ksr/YACC1-2020/PCB/Working - Under Develolpment/Index Registers 1.2/Notes.rtf

Index registers V1.0

Next version 1.1

Changes since 1.0

Signal -IN and -OUT converted to In and OUT. Neither used in Index Register board

BUS Description PDF dated June 18 2020 is updated to new spec

NOTE from old design

Up or Down on rising edge other line must be high

IC38 switched to 4077 pin compatible with 74266

Version 1.1 to production

Next version 1.2
SEE page 7
Is bus direction correct, should it be based on -rd-sel
