ksr/YACC1-2020/PCB/Production/ALU-V3.0-2 layer/Notes.rtf

SCRAP. ARGh no vcc and gnd

Board labeled YACC1 ALYU BOARD V1.0

ALU V3.0

Sent to Production using files in “gerbers” directory. This was missing outline file, should have used alu4_2020-06-14.zip in this directory this had outline file.

This is a 2 layer board, should have been a 4 layer board

Signal -IN and -OUT converted to In and OUT. Only IN is used in ALU

No changes made to production files but BUS is now treated as active HI for IN and OUT. TBC Schematic/PCB shows active low but will be assumed input from bus is active HI

BUS Description PDF dated June 18 2020 is updated to new spec

Mask shows V1.0, should read 3.0
