ksr/YACC1-2020/PCB/Production/Bus Jumper Horizontal V3.2/Notes.rtf

Changes since production Horizontal Bus Jumper 3.0

3.2
Increase trace width spacing and add layers

Next version V3.3
