ksr/YACC1-2020/PCB/Production/Index Registers - no address1.0/Notes.rtf

Index registers V3.0

Signal -IN and -OUT converted to In and OUT. Neither used in Index Register board

BUS Description PDF dated June 18 2020 is updated to new spec

IC38 switched to 4077 pin compatible with 74266
