ksr/YACC1-2020/PCB/Production/Mem Switch V1.0/Notes.rtf

Changes since production to V3.1

Added -Valid Memory Address (-VMA) to bus Row C pin 12)

Next version V3.2
