ksr/YACC1-2020/Photos & Videos/alu v3.2 top.jpeg

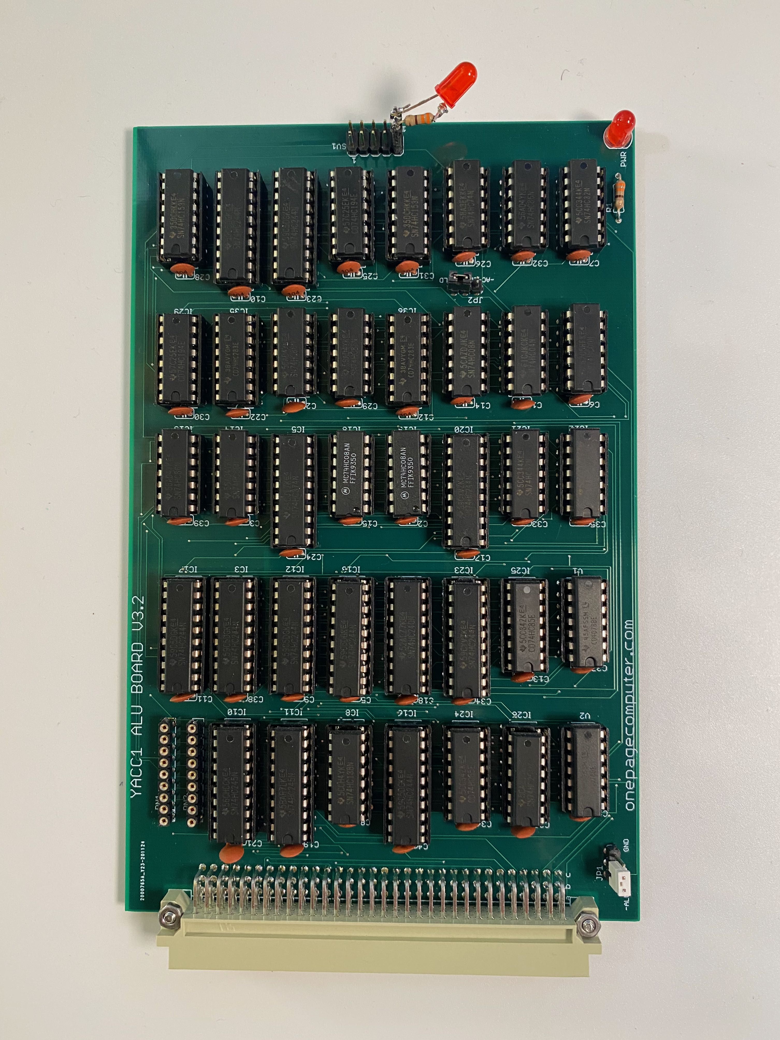
Photos & Videos/alu v3.2 top.jpeg
