ksr/YACC1-2020/Photos & Videos/bus v1.0 top.jpeg

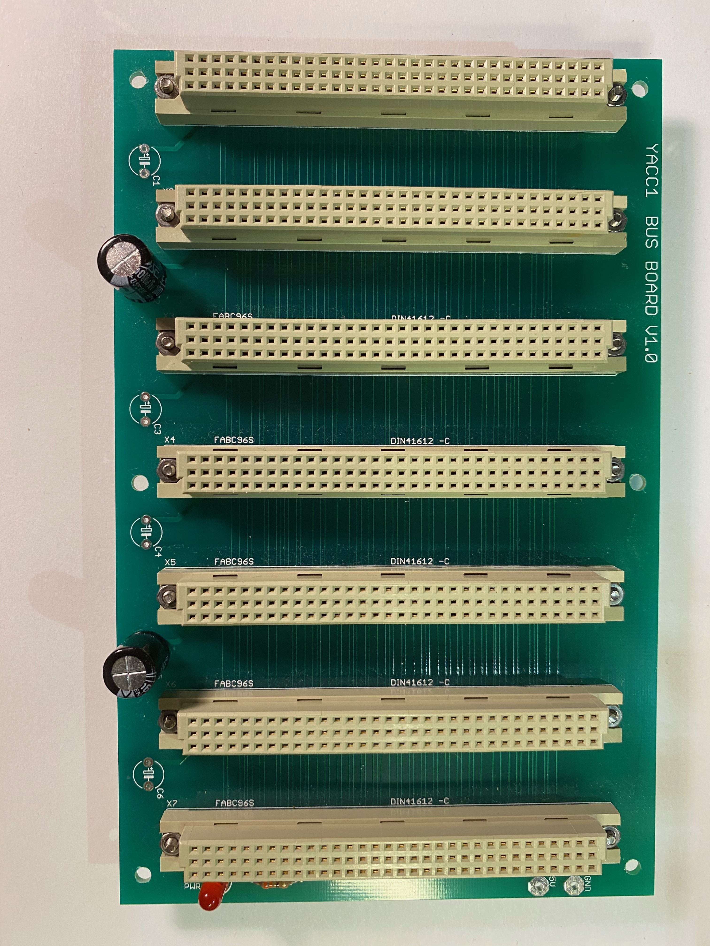
Photos & Videos/bus v1.0 top.jpeg
