ksr/YACC1-2020/Photos & Videos/index register v1.1 top.jpeg

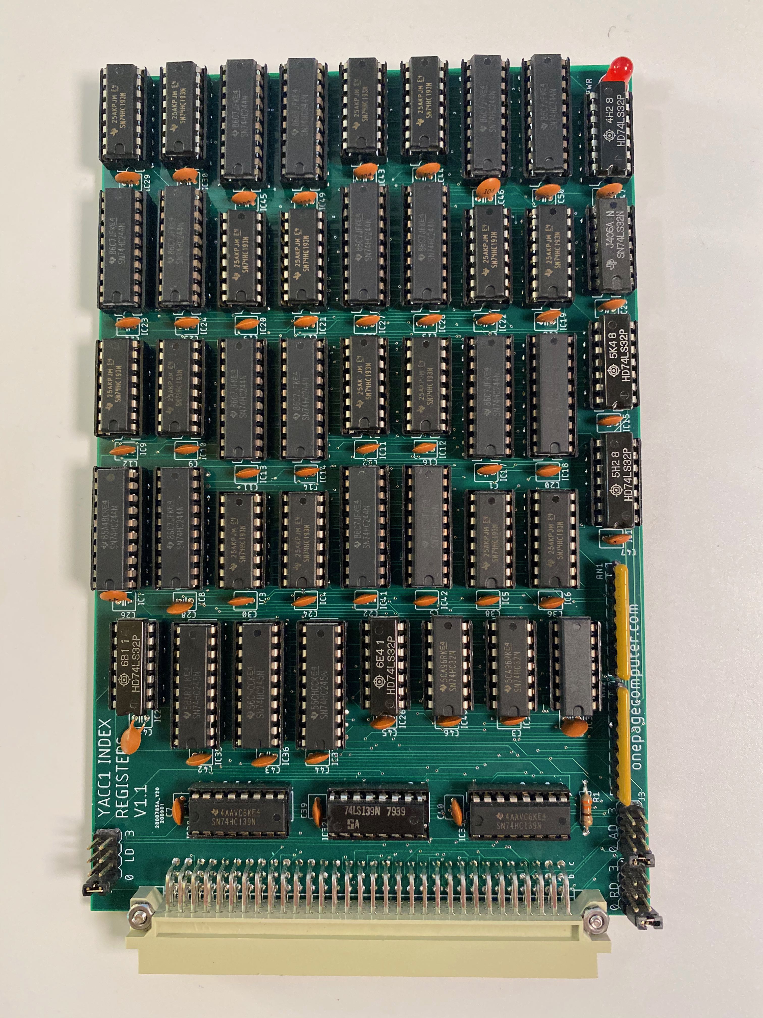
Photos & Videos/index register v1.1 top.jpeg
