ksr/YACC1-2020/Photos & Videos/io v1.1 bottom.jpeg

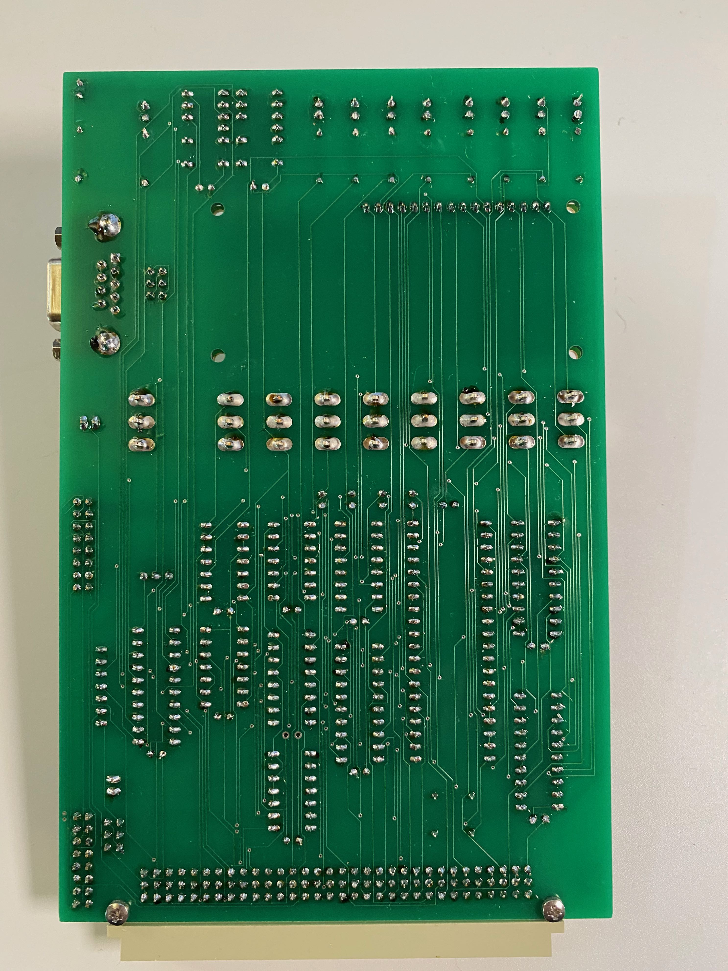
Photos & Videos/io v1.1 bottom.jpeg
