ksr/YACC1-2020/Photos & Videos/sequencer memory v2.1 top.jpeg

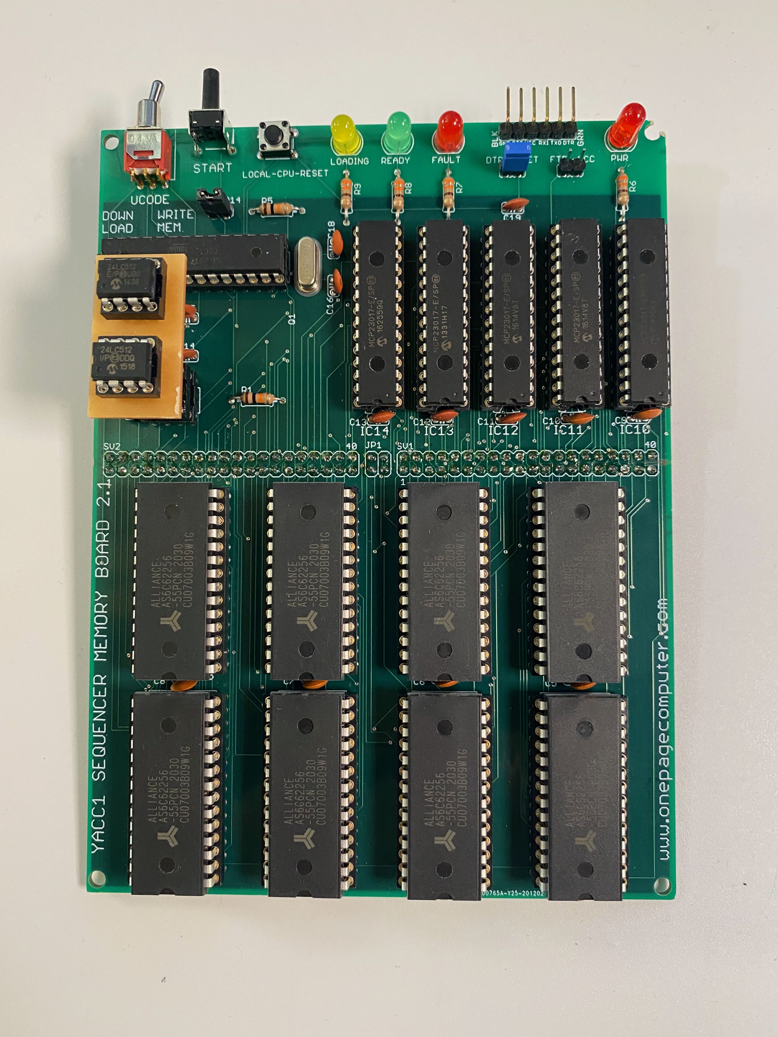
Photos & Videos/sequencer memory v2.1 top.jpeg
