ksr/YACC1-2020/Photos & Videos/sequencer top.jpeg

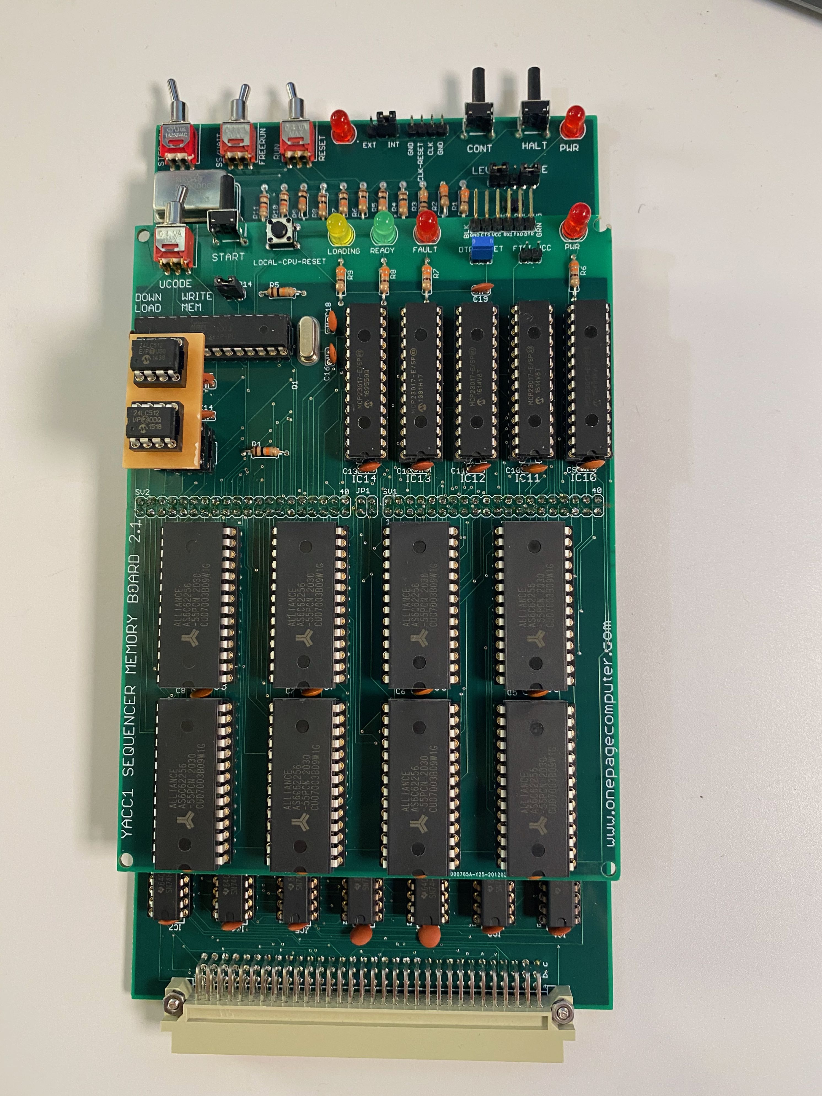
Photos & Videos/sequencer top.jpeg
