ksr/YACC1-2020/Photos & Videos/system1.jpeg

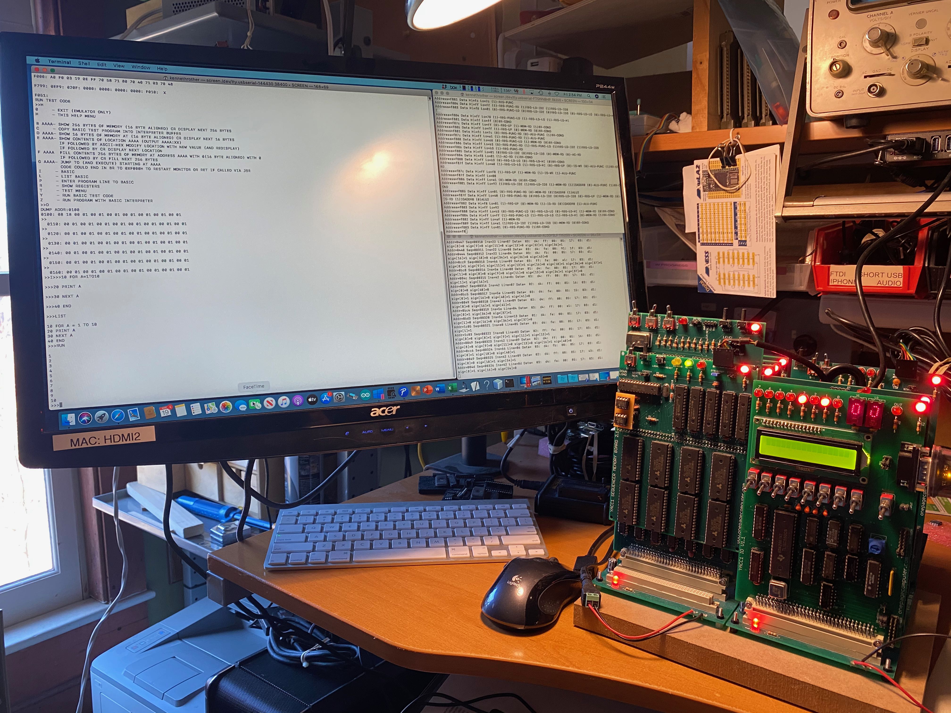
Photos & Videos/system1.jpeg
