ksr/YACC1-2020/Photos & Videos/bus v1.1 solder.jpeg

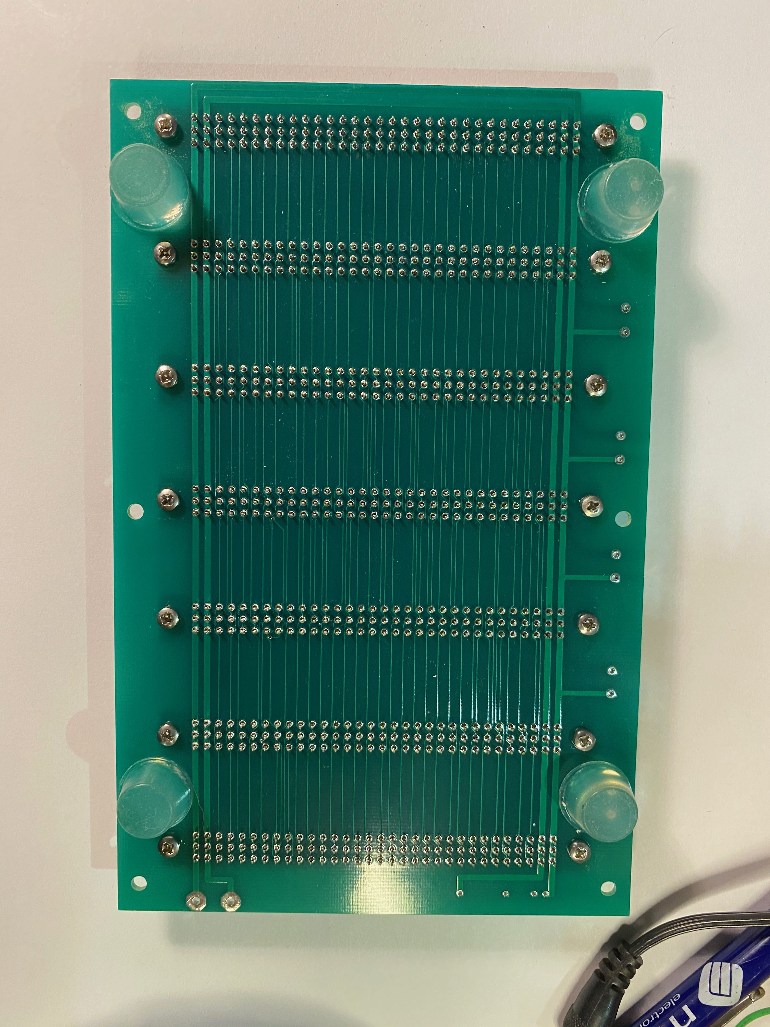
Photos & Videos/bus v1.1 solder.jpeg
