ksr/YACC1-2020/Photos & Videos/index register v1.1 solder.jpeg

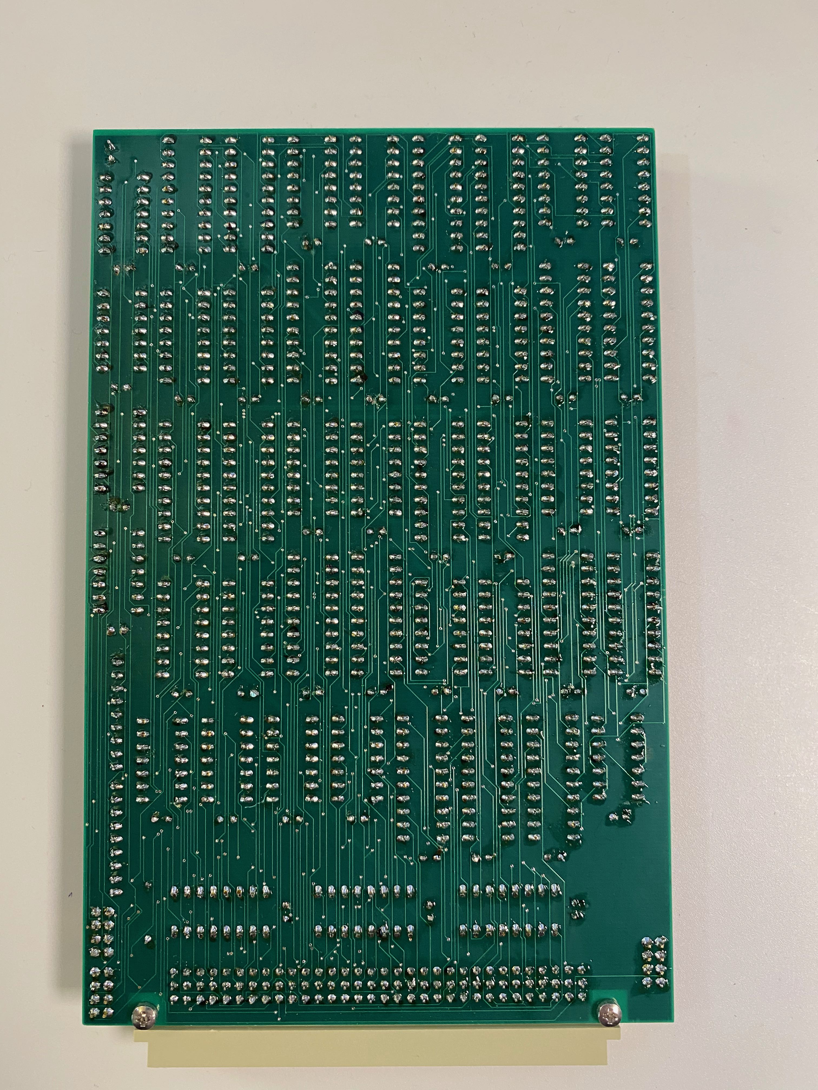
Photos & Videos/index register v1.1 solder.jpeg
