ksr/YACC1-2020/Photos & Videos/sequencer memory v2.1 solder.jpeg

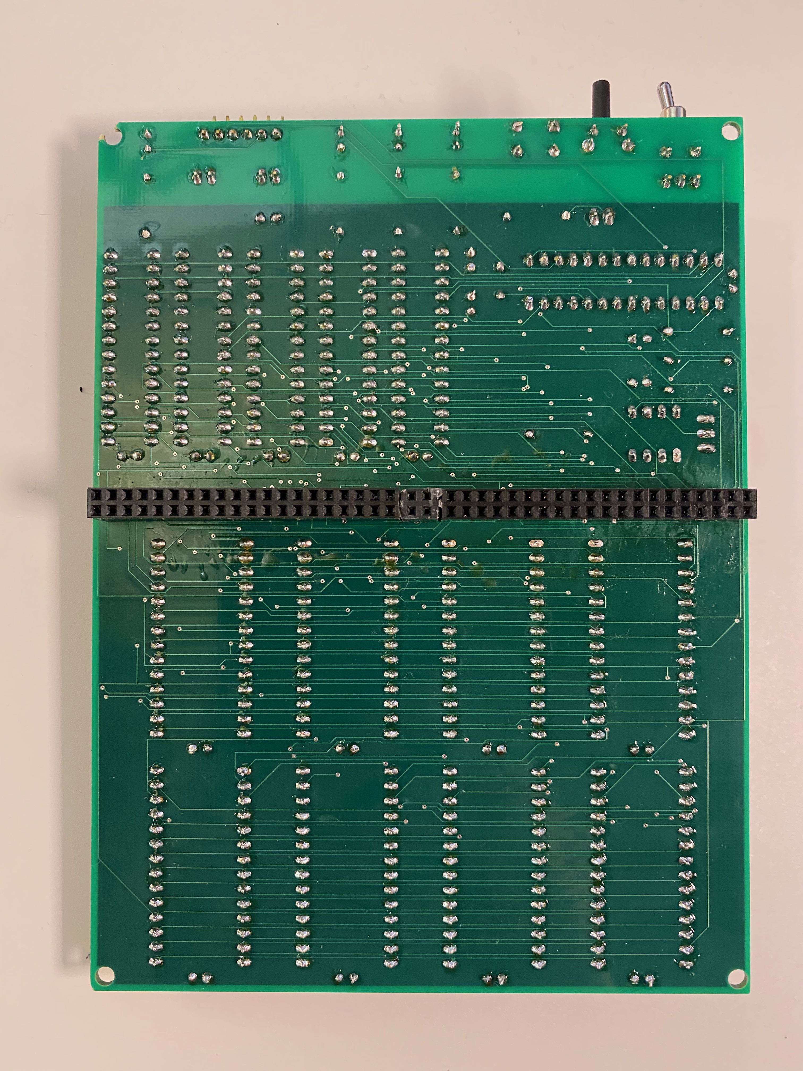
Photos & Videos/sequencer memory v2.1 solder.jpeg
