ksr/YACC1-2020/Photos & Videos/test board v1.1 top.jpeg

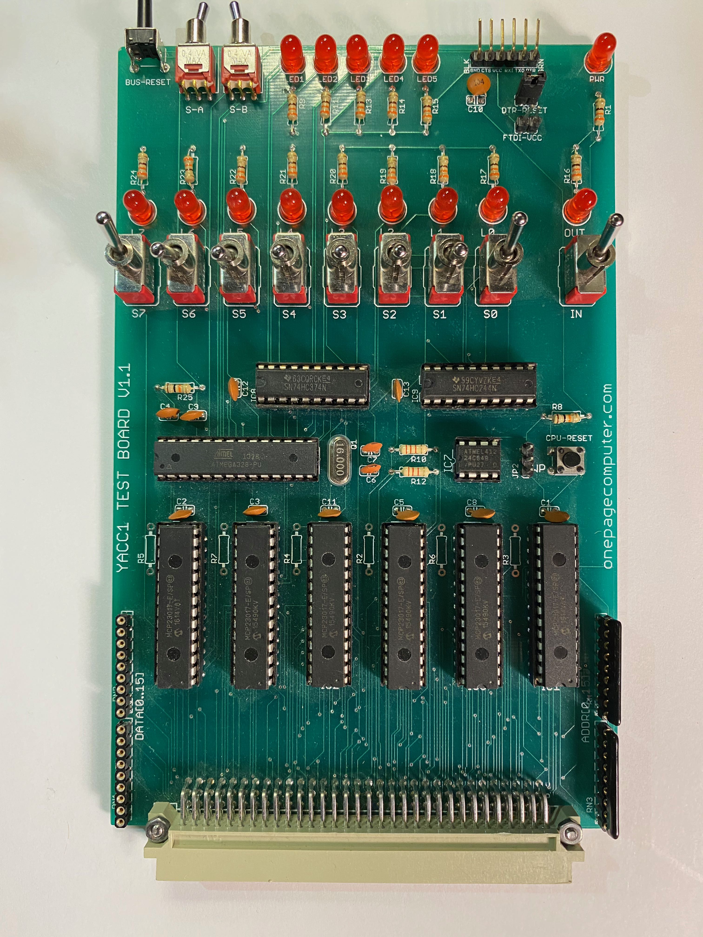
Photos & Videos/test board v1.1 top.jpeg
