ksr/YACC1-2020/PCB/Working - Under Develolpment/Mem Register V1.0/YACC1 Connector - V3.1.pdf

YACC1 Connector | YACC 3.1
Pin | A | A | A | B | B | B | C | C | C

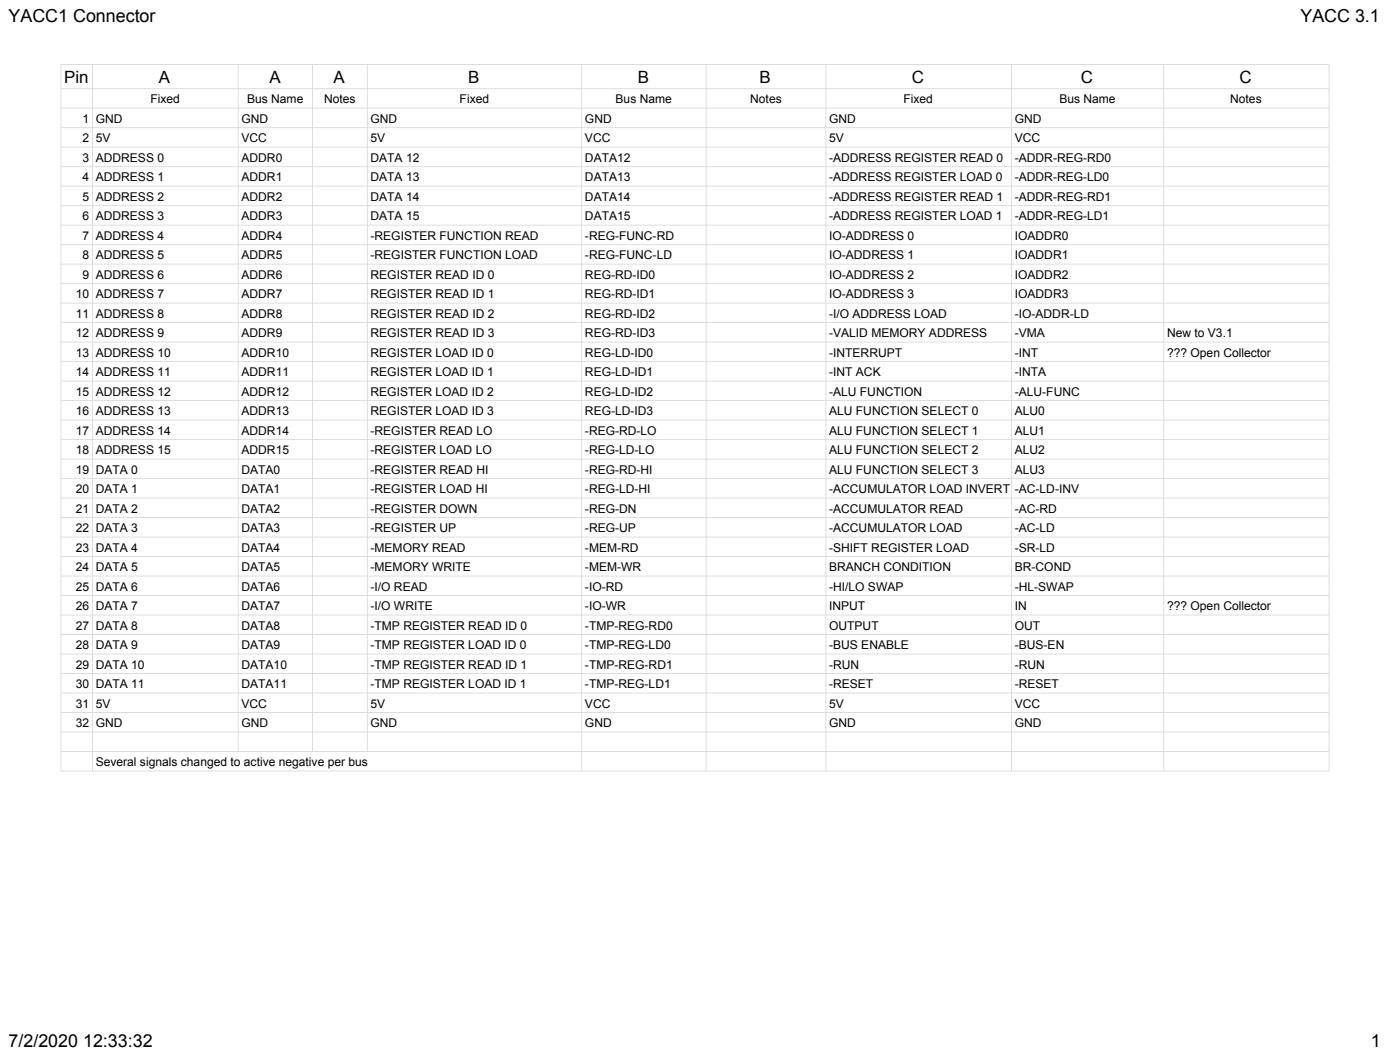
[picture p26: page 1]
Fixed; Bus Name; Notes; 1 GND; GND; VCC; 3 ADDRESS 0; ADDR0; DATA 12; DATA12; -ADDRESS REGISTER READ 0 -ADDR-REG-RD0; 4 ADDRESS 1; ADDR1; DATA 13; DATA13; -ADDRESS REGISTER LOAD 0 -ADDR-REG-LD0; 5 ADDRESS 2; ADDR2; DATA 14; DATA14; -ADDRESS REGISTER READ 1 -ADDR-REG-RD1; 6 ADDRESS 3; ADDR3; DATA 15; DATA15; -ADDRESS REGISTER LOAD 1 -ADDR-REG-LD1; 7 ADDRESS 4; ADDR4; -REGISTER FUNCTION READ; -REG-FUNC-RD; IO-ADDRESS 0; IOADDR0; 8 ADDRESS 5; ADDR5; -REGISTER FUNCTION LOAD; -REG-FUNC-LD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

Several signals changed to active negative per bus
