ksr/YACC1-2020/PCB/Working - Under Develolpment/Memory v1.3/Memory V1.2.pdf

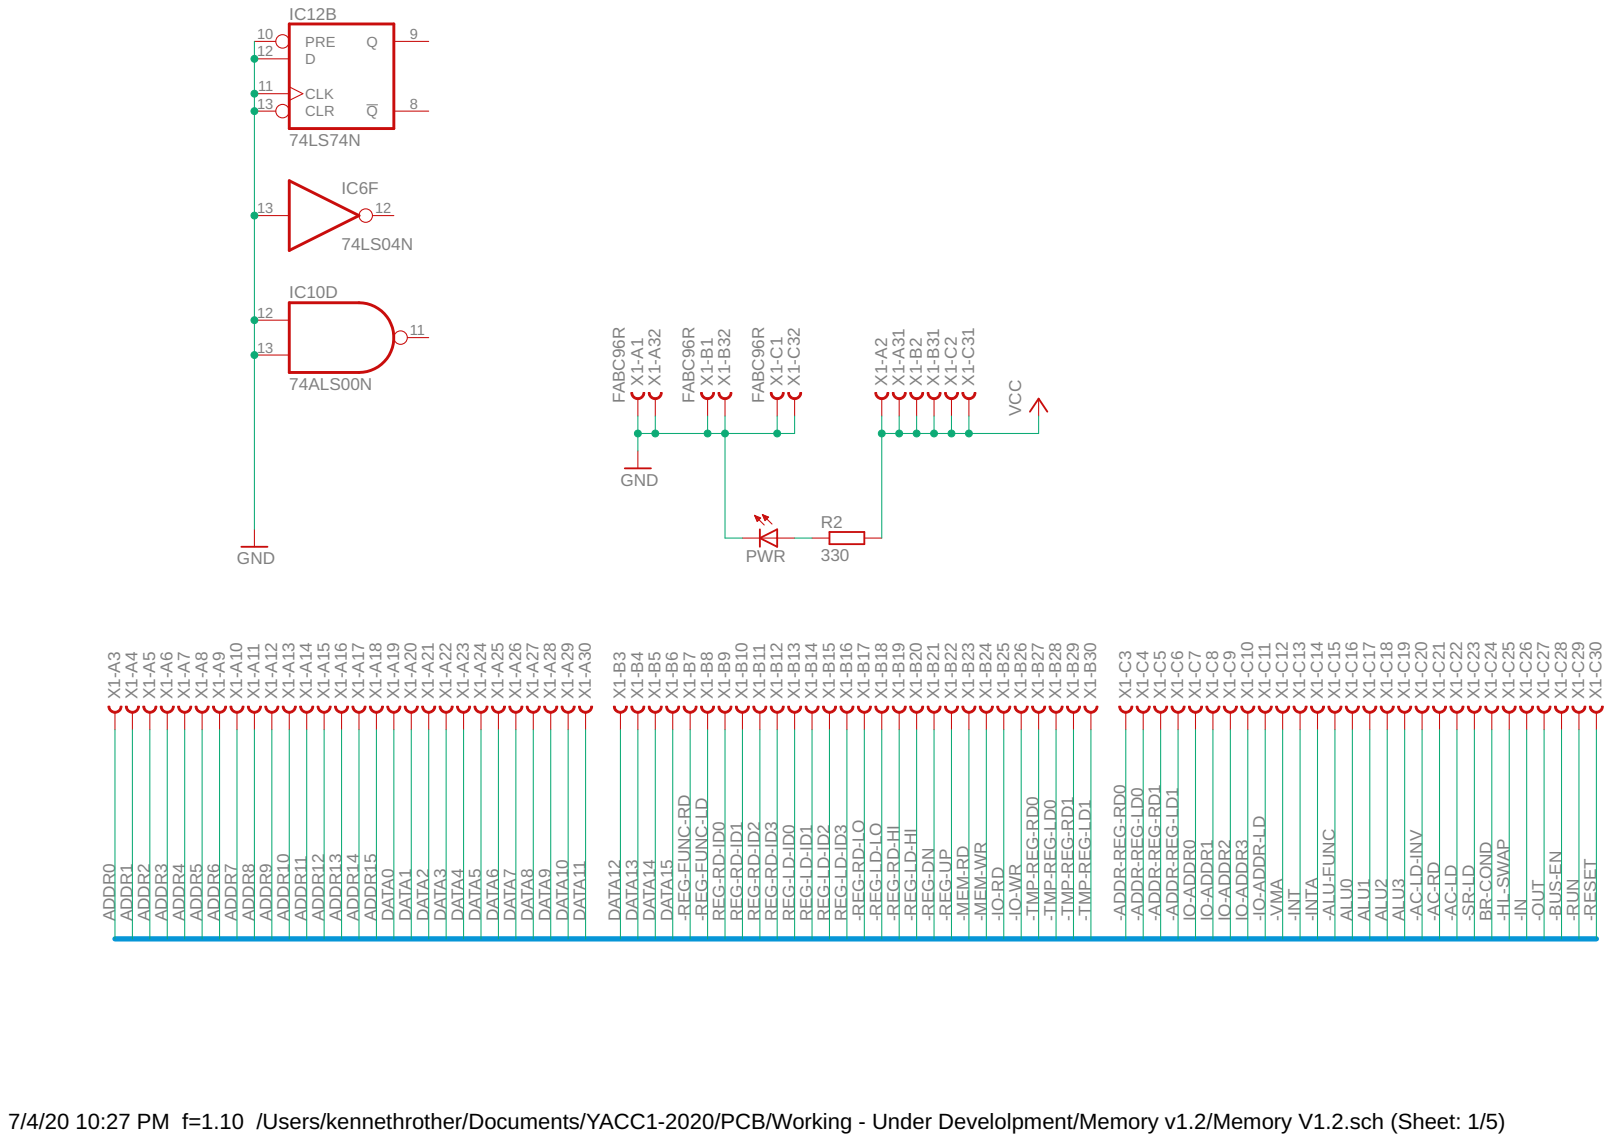
[picture p27: page 1]

D-ID2 REG-LD-ID3 REG-LD-ID1 REG-LD-ID2

D-HI -REG-LD-HI

7/4/20 10:27 PM f=1.10 /Users/kennethrother/Documents/YACC1-2020/PCB/Working - Under Develolpment/Memory v1.2/Memory V1.2.sch (Sheet: 1/5)

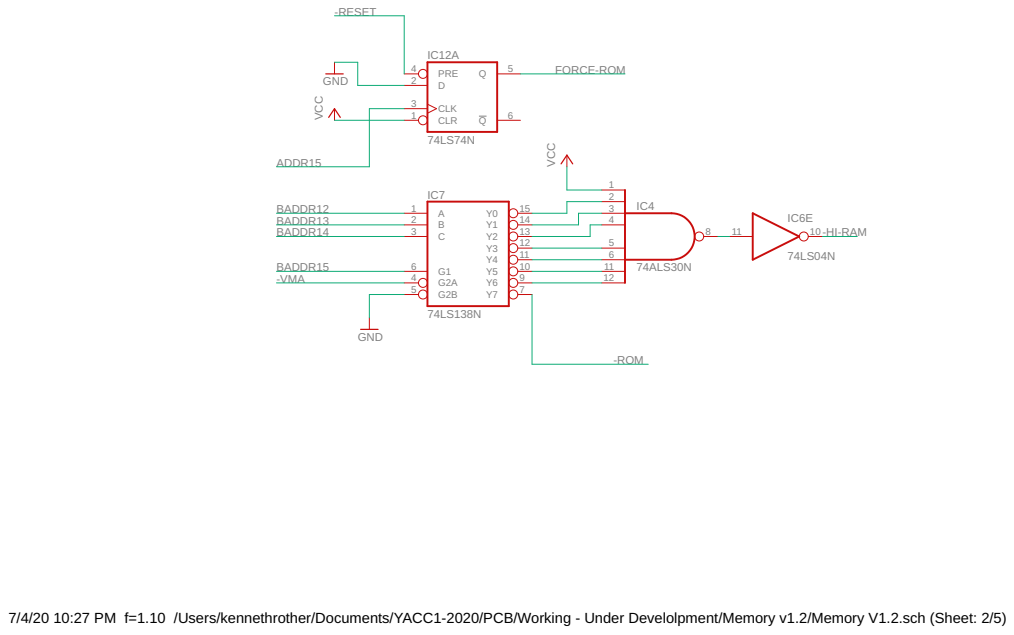
[picture p28: page 2]

7/4/20 10:27 PM f=1.10 /Users/kennethrother/Documents/YACC1-2020/PCB/Working - Under Develolpment/Memory v1.2/Memory V1.2.sch (Sheet: 2/5)

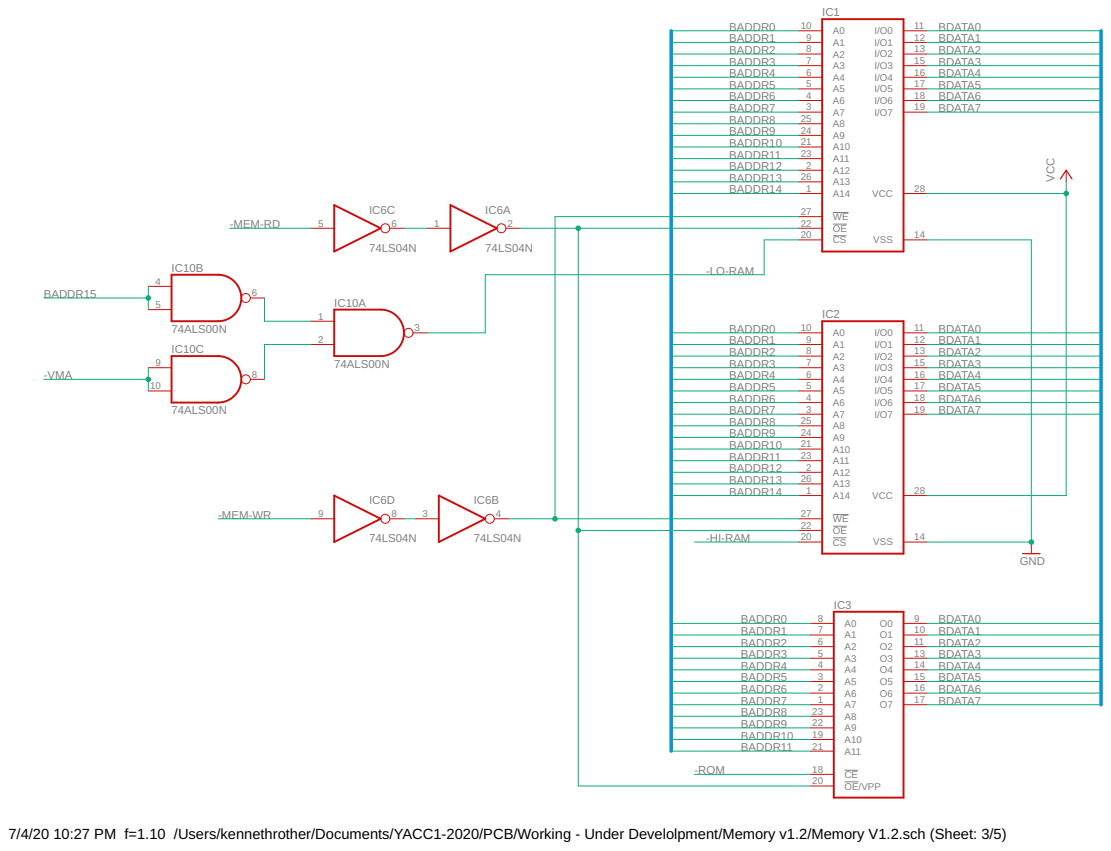
[picture p29: page 3]

BADDR1 9 | 12 BDATA1
BADDR2 8 | 13 BDATA2
BADDR3 7 | 15 BDATA3
BADDR4 6 | 16 BDATA4
BADDR5 5 | 17 BDATA5
BADDR6 4 | 18 BDATA6
3 BADDR7 | 19 BDATA7

27 | 14
22 20

4 BADDR6 | 18 BDATA6
BADDR7 3 | 19 BDATA7
BADDR8 25 | 28

7/4/20 10:27 PM f=1.10 /Users/kennethrother/Documents/YACC1-2020/PCB/Working - Under Develolpment/Memory v1.2/Memory V1.2.sch (Sheet: 3/5)

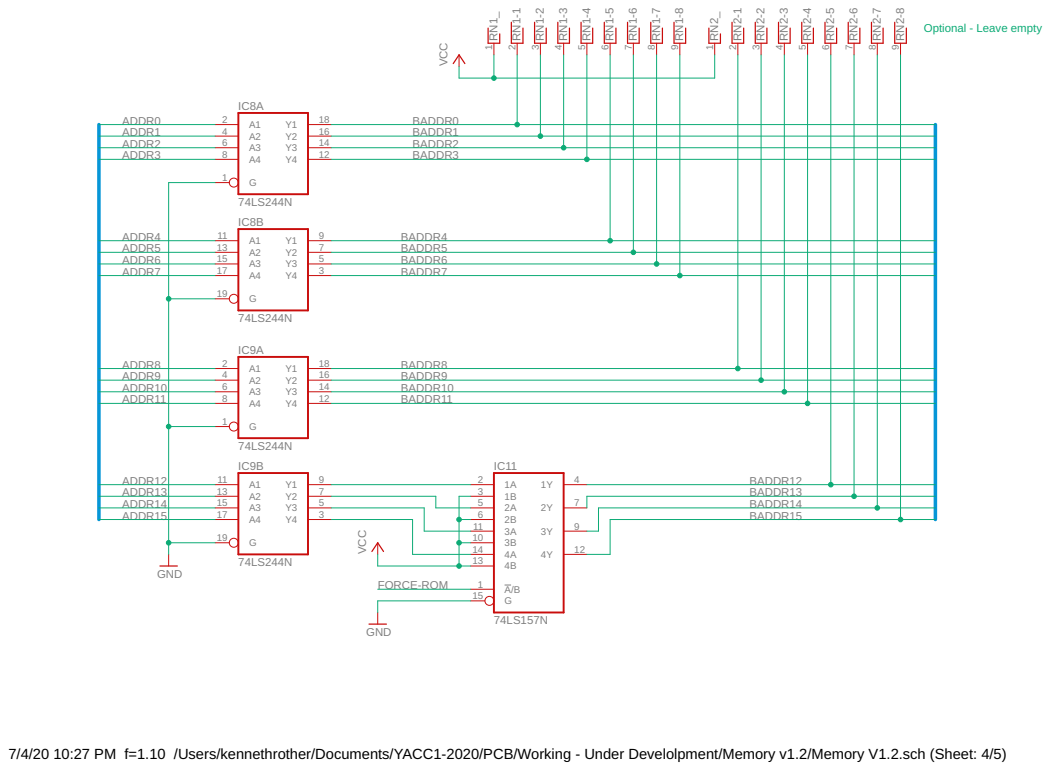
[picture p30: page 4]

ADDR1 4 | BADDR1
ADDR2 6 | 14 Y2 BADDR2
ADDR3 | 12 Y3 BADDR3

ADDR5 | 13 | 7 Y1 BADDR5 5 Y2
ADDR6 | 15 | BADDR6 3 Y3

ADDR9 | 4 | 16 Y1 BADDR9
ADDR10 | 6 | 14 Y2 BADDR10

7/4/20 10:27 PM f=1.10 /Users/kennethrother/Documents/YACC1-2020/PCB/Working - Under Develolpment/Memory v1.2/Memory V1.2.sch (Sheet: 4/5)

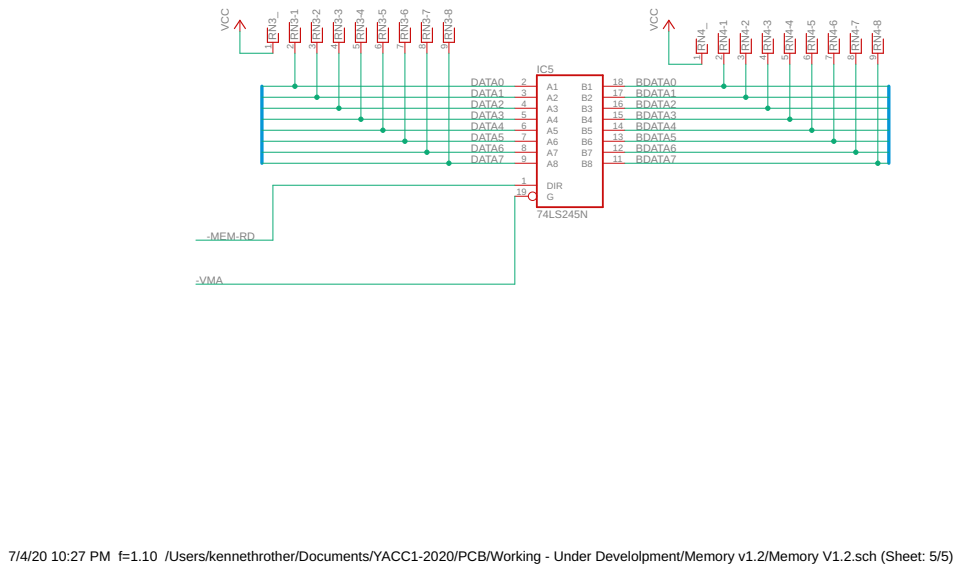
[picture p31: page 5]

DATA1 3 | 17 B1 BDATA1
DATA2 4 | 16 B2 BDATA2 15 B3
DATA3 5 | BDATA3 14 B4
DATA4 6 | BDATA4
DATA5 7 | 13 B5 BDATA5
DATA6 8 | 12 B6 BDATA6
DATA7 | 11 B7 BDATA7

7/4/20 10:27 PM f=1.10 /Users/kennethrother/Documents/YACC1-2020/PCB/Working - Under Develolpment/Memory v1.2/Memory V1.2.sch (Sheet: 5/5)
