ksr/YACC1-2020/PCB/Production/BUS-PROD-V1.1/yacc2buss.pdf

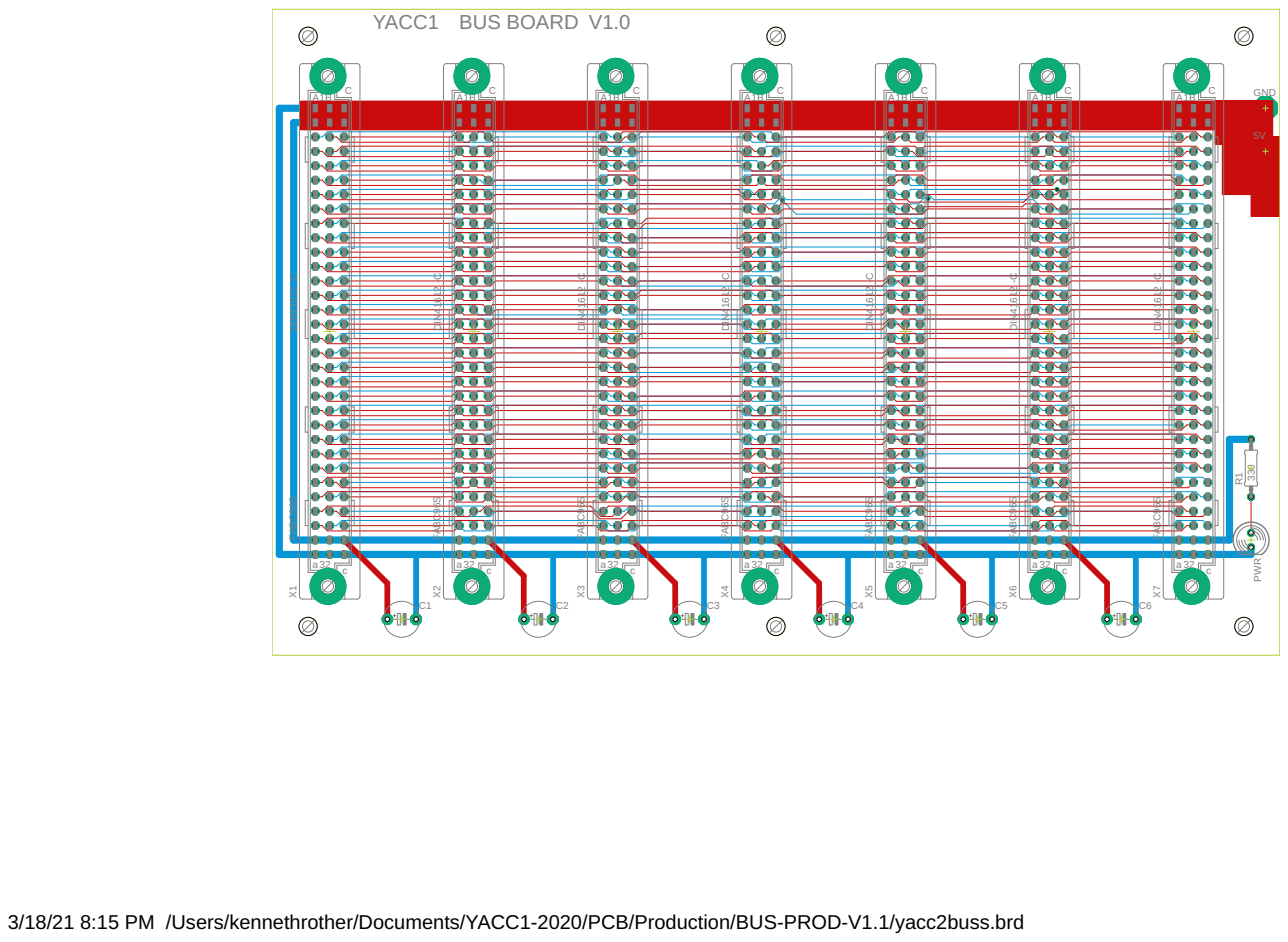
[picture p36: page 1]

3/18/21 8:15 PM /Users/kennethrother/Documents/YACC1-2020/PCB/Production/BUS-PROD-V1.1/yacc2buss.brd
