ksr/YACC1-2020/PCB/Working - Under Develolpment/Sequencer-Memory-V2.1/old-YACC1/Sequencer-Memory-V1.0-3.pdf

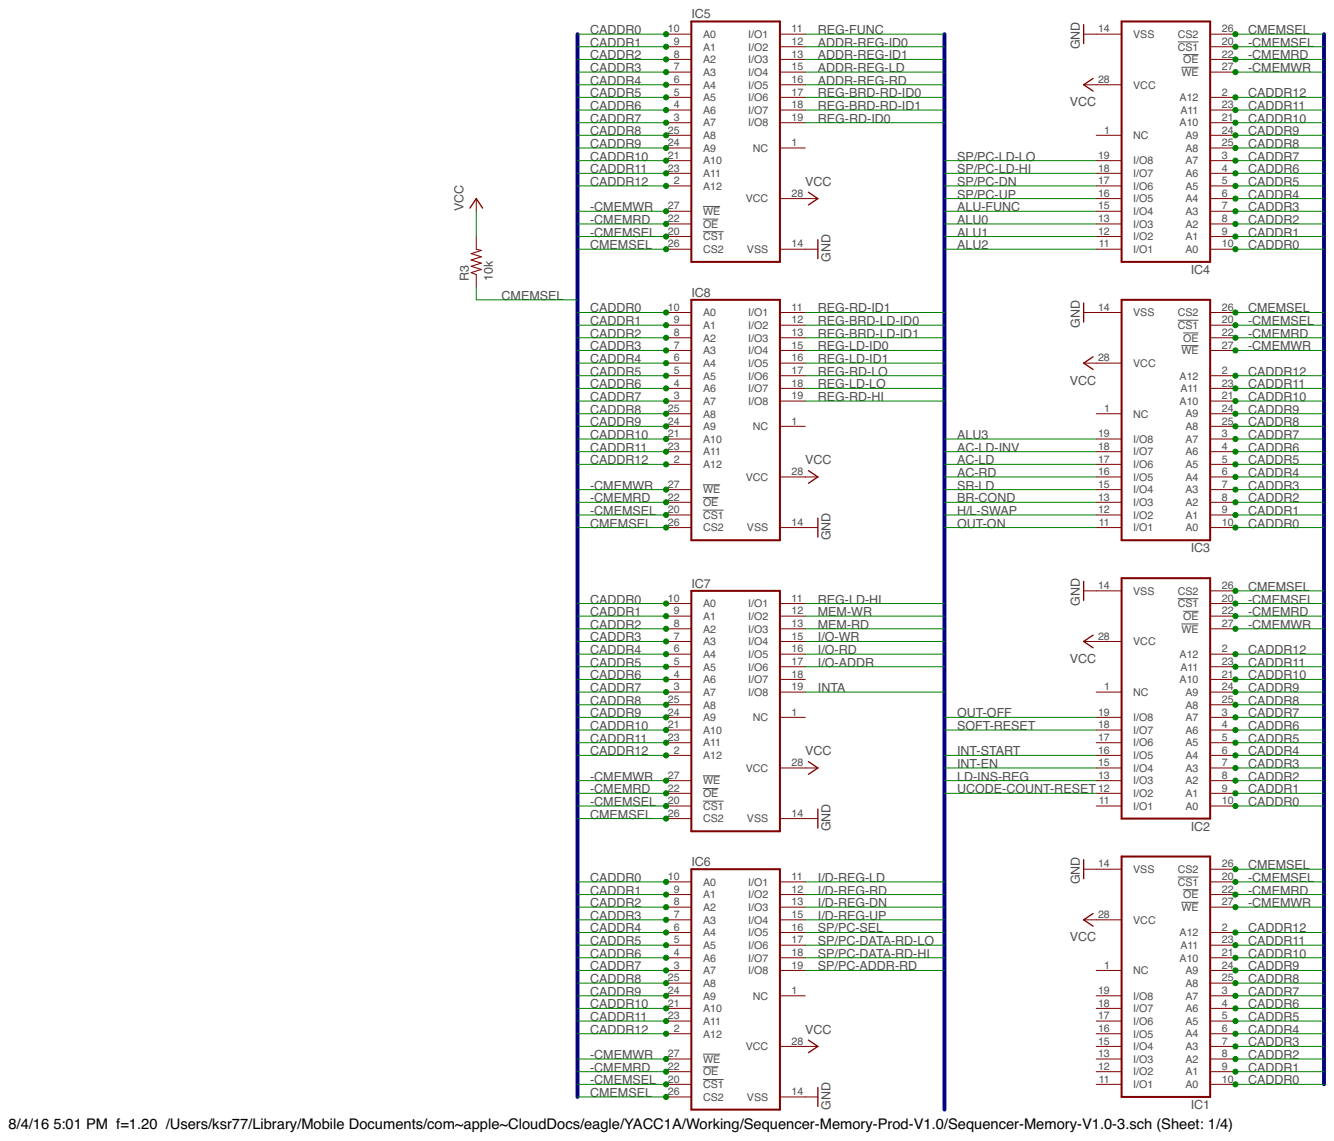
[picture p37: page 1]

CADDR11 23 | SP/PC-LD-HI 18 | 4 A7 CADDR6
2 CADDR12 | 17 SP/PC-DN | 5 A6 CADDR5
-CMEMWR 27 | SP/PC-UP 16 | 6 A5 CADDR4

ALU-FUNC 15 | 7 A4 CADDR3

-CMEMRD 22 | ALU0 13 | 8 A3 CADDR2
-CMEMSEL 20 | ALU1 12 | 9 A2 CADDR1

8/4/16 5:01 PM f=1.20 /Users/ksr77/Library/Mobile Documents/com~apple~CloudDocs/eagle/YACC1A/Working/Sequencer-Memory-Prod-V1.0/Sequencer-Memory-V1.0-3.sch (Sheet: 1/4)

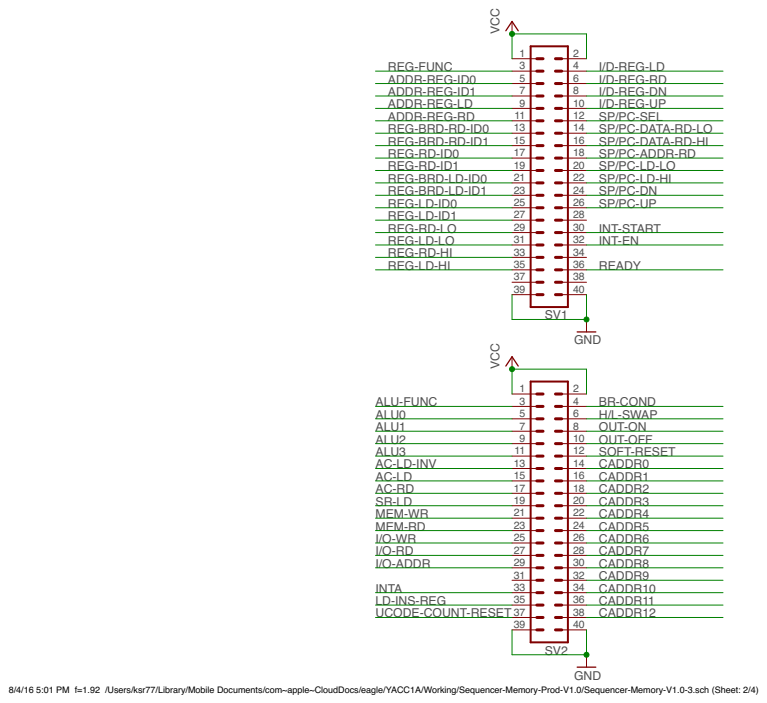
[picture p38: page 2]

8/4/16 5:01 PM f=1.92 /Users/ksr77/Library/Mobile Documents/com~apple~CloudDocs/eagle/YACC1A/Working/Sequencer-Memory-Prod-V1.0/Sequencer-Memory-V1.0-3.sch (Sheet: 2/4)

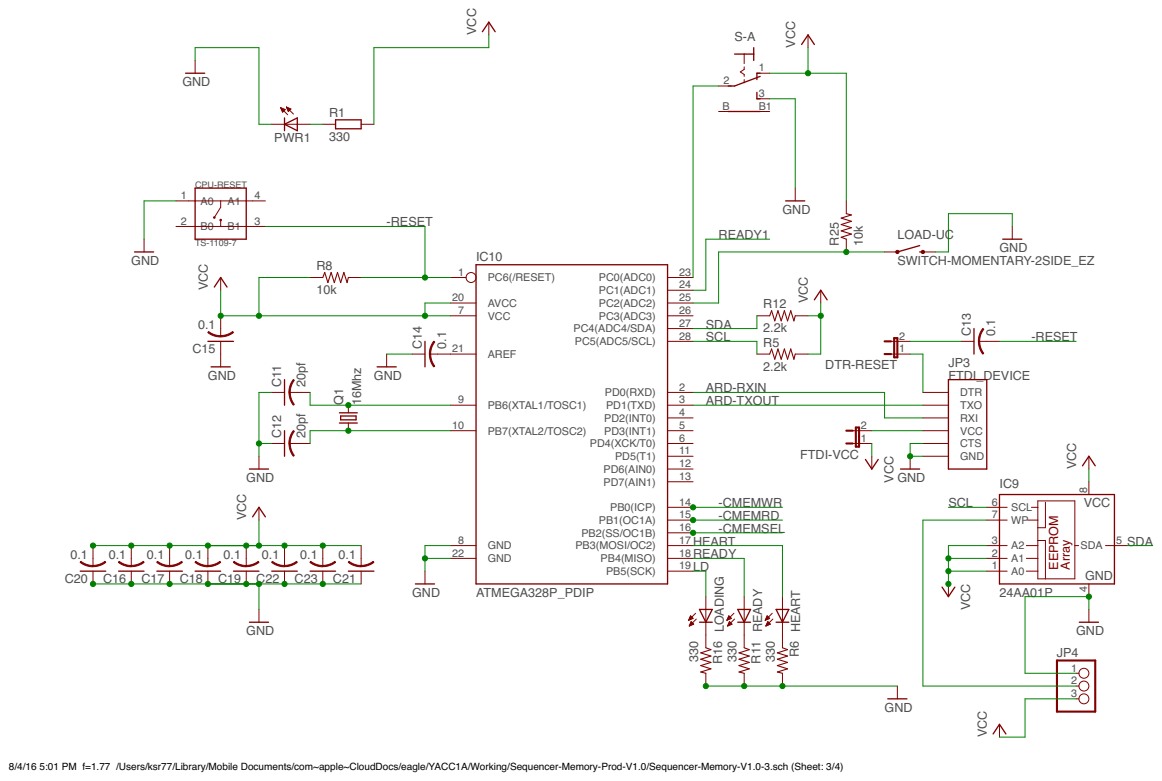
[picture p39: page 3]

8/4/16 5:01 PM f=1.77 /Users/ksr77/Library/Mobile Documents/com~apple~CloudDocs/eagle/YACC1A/Working/Sequencer-Memory-Prod-V1.0/Sequencer-Memory-V1.0-3.sch (Sheet: 3/4)

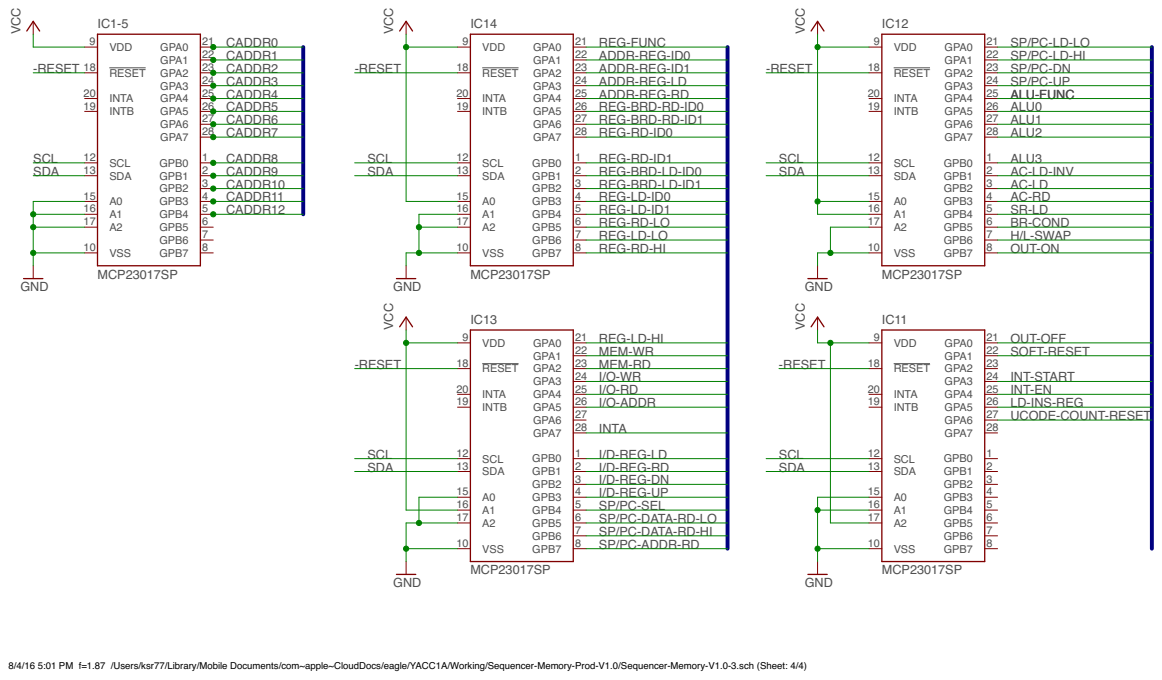
[picture p40: page 4]

8/4/16 5:01 PM f=1.87 /Users/ksr77/Library/Mobile Documents/com~apple~CloudDocs/eagle/YACC1A/Working/Sequencer-Memory-Prod-V1.0/Sequencer-Memory-V1.0-3.sch (Sheet: 4/4)
