ksr/YACC1-2020/PCB/Working - Under Develolpment/Sequencer-Memory-V2.1/old-YACC1/Sequencer-Memory-V1.0-2.brd

## EAGLE design PCB/Working - Under Develolpment/Sequencer-Memory-V2.1/old-YACC1/Sequencer-Memory-V1.0-2.brd (2020-08-23, an earlier design)

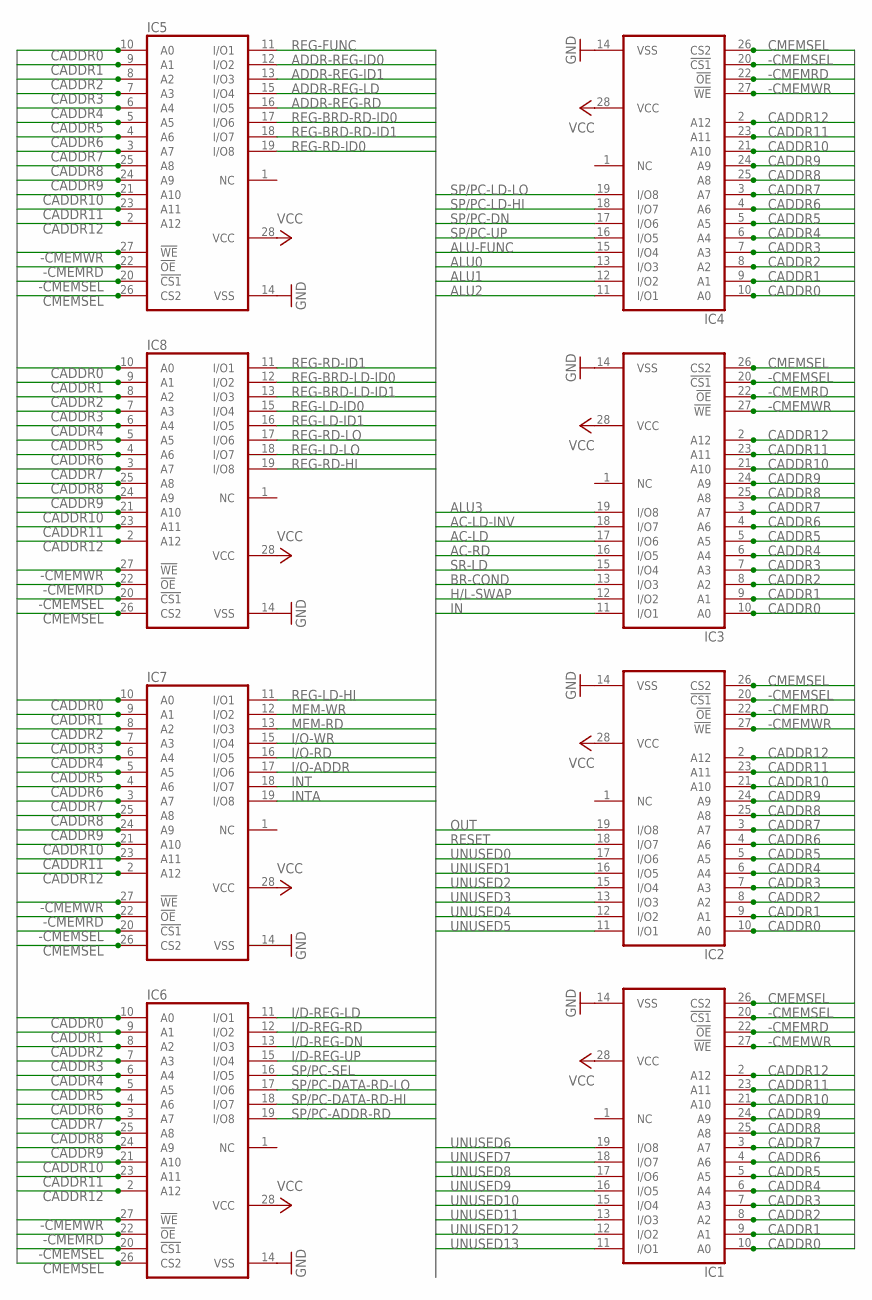
[picture p94: schematic Sequencer-Memory-V1.0-2.sch, sheet 1, Memory]

Parts:
IC1, IC2, IC3, IC4, IC5, IC6, IC7, IC8: 6264A; DIL28-6

Connections:
-CMEMRD: IC1.22 (!OE), IC2.22 (!OE), IC3.22 (!OE), IC4.22 (!OE), IC5.22 (!OE), IC6.22 (!OE), IC7.22 (!OE), IC8.22 (!OE); also elsewhere on the board
-CMEMSEL: IC1.20 (!CS1), IC2.20 (!CS1), IC3.20 (!CS1), IC4.20 (!CS1), IC5.20 (!CS1), IC6.20 (!CS1), IC7.20 (!CS1), IC8.20 (!CS1); also elsewhere on the board
-CMEMWR: IC1.27 (!WE), IC2.27 (!WE), IC3.27 (!WE), IC4.27 (!WE), IC5.27 (!WE), IC6.27 (!WE), IC7.27 (!WE), IC8.27 (!WE); also elsewhere on the board
AC-LD: IC3.17 (I/O6); also elsewhere on the board
AC-LD-INV: IC3.18 (I/O7); also elsewhere on the board
AC-RD: IC3.16 (I/O5); also elsewhere on the board
ADDR-REG-ID0: IC5.12 (I/O2); also elsewhere on the board
ADDR-REG-ID1: IC5.13 (I/O3); also elsewhere on the board
ADDR-REG-LD: IC5.15 (I/O4); also elsewhere on the board
ADDR-REG-RD: IC5.16 (I/O5); also elsewhere on the board
ALU0: IC4.13 (I/O3); also elsewhere on the board
ALU1: IC4.12 (I/O2); also elsewhere on the board
ALU2: IC4.11 (I/O1); also elsewhere on the board
ALU3: IC3.19 (I/O8); also elsewhere on the board
ALU-FUNC: IC4.15 (I/O4); also elsewhere on the board
BR-COND: IC3.13 (I/O3); also elsewhere on the board
CADDR0: IC1.10 (A0), IC2.10 (A0), IC3.10 (A0), IC4.10 (A0), IC5.10 (A0), IC6.10 (A0), IC7.10 (A0), IC8.10 (A0); also elsewhere on the board
CADDR1: IC1.9 (A1), IC2.9 (A1), IC3.9 (A1), IC4.9 (A1), IC5.9 (A1), IC6.9 (A1), IC7.9 (A1), IC8.9 (A1); also elsewhere on the board
CADDR2: IC1.8 (A2), IC2.8 (A2), IC3.8 (A2), IC4.8 (A2), IC5.8 (A2), IC6.8 (A2), IC7.8 (A2), IC8.8 (A2); also elsewhere on the board
CADDR3: IC1.7 (A3), IC2.7 (A3), IC3.7 (A3), IC4.7 (A3), IC5.7 (A3), IC6.7 (A3), IC7.7 (A3), IC8.7 (A3); also elsewhere on the board
CADDR4: IC1.6 (A4), IC2.6 (A4), IC3.6 (A4), IC4.6 (A4), IC5.6 (A4), IC6.6 (A4), IC7.6 (A4), IC8.6 (A4); also elsewhere on the board
CADDR5: IC1.5 (A5), IC2.5 (A5), IC3.5 (A5), IC4.5 (A5), IC5.5 (A5), IC6.5 (A5), IC7.5 (A5), IC8.5 (A5); also elsewhere on the board
CADDR6: IC1.4 (A6), IC2.4 (A6), IC3.4 (A6), IC4.4 (A6), IC5.4 (A6), IC6.4 (A6), IC7.4 (A6), IC8.4 (A6); also elsewhere on the board
CADDR7: IC1.3 (A7), IC2.3 (A7), IC3.3 (A7), IC4.3 (A7), IC5.3 (A7), IC6.3 (A7), IC7.3 (A7), IC8.3 (A7); also elsewhere on the board
CADDR8: IC1.25 (A8), IC2.25 (A8), IC3.25 (A8), IC4.25 (A8), IC5.25 (A8), IC6.25 (A8), IC7.25 (A8), IC8.25 (A8); also elsewhere on the board
CADDR9: IC1.24 (A9), IC2.24 (A9), IC3.24 (A9), IC4.24 (A9), IC5.24 (A9), IC6.24 (A9), IC7.24 (A9), IC8.24 (A9); also elsewhere on the board
CADDR10: IC1.21 (A10), IC2.21 (A10), IC3.21 (A10), IC4.21 (A10), IC5.21 (A10), IC6.21 (A10), IC7.21 (A10), IC8.21 (A10); also elsewhere on the board
CADDR11: IC1.23 (A11), IC2.23 (A11), IC3.23 (A11), IC4.23 (A11), IC5.23 (A11), IC6.23 (A11), IC7.23 (A11), IC8.23 (A11); also elsewhere on the board
CADDR12: IC1.2 (A12), IC2.2 (A12), IC3.2 (A12), IC4.2 (A12), IC5.2 (A12), IC6.2 (A12), IC7.2 (A12), IC8.2 (A12); also elsewhere on the board
CMEMSEL: IC1.26 (CS2), IC2.26 (CS2), IC3.26 (CS2), IC4.26 (CS2), IC5.26 (CS2), IC6.26 (CS2), IC7.26 (CS2), IC8.26 (CS2); also elsewhere on the board
GND: IC1.14 (VSS), IC2.14 (VSS), IC3.14 (VSS), IC4.14 (VSS), IC5.14 (VSS), IC6.14 (VSS), IC7.14 (VSS), IC8.14 (VSS); also elsewhere on the board
H/L-SWAP: IC3.12 (I/O2); also elsewhere on the board
I/D-REG-DN: IC6.13 (I/O3); also elsewhere on the board
I/D-REG-LD: IC6.11 (I/O1); also elsewhere on the board
I/D-REG-RD: IC6.12 (I/O2); also elsewhere on the board
I/D-REG-UP: IC6.15 (I/O4); also elsewhere on the board
I/O-ADDR: IC7.17 (I/O6); also elsewhere on the board
I/O-RD: IC7.16 (I/O5); also elsewhere on the board
I/O-WR: IC7.15 (I/O4); also elsewhere on the board
IN: IC3.11 (I/O1); also elsewhere on the board
INT: IC7.18 (I/O7); also elsewhere on the board
INTA: IC7.19 (I/O8); also elsewhere on the board
MEM-RD: IC7.13 (I/O3); also elsewhere on the board
MEM-WR: IC7.12 (I/O2); also elsewhere on the board
OUT: IC2.19 (I/O8); also elsewhere on the board
REG-BRD-LD-ID0: IC8.12 (I/O2); also elsewhere on the board
REG-BRD-LD-ID1: IC8.13 (I/O3); also elsewhere on the board
REG-BRD-RD-ID0: IC5.17 (I/O6); also elsewhere on the board
REG-BRD-RD-ID1: IC5.18 (I/O7); also elsewhere on the board
REG-FUNC: IC5.11 (I/O1); also elsewhere on the board
REG-LD-HI: IC7.11 (I/O1); also elsewhere on the board
REG-LD-ID0: IC8.15 (I/O4); also elsewhere on the board
REG-LD-ID1: IC8.16 (I/O5); also elsewhere on the board
REG-LD-LO: IC8.18 (I/O7); also elsewhere on the board
REG-RD-HI: IC8.19 (I/O8); also elsewhere on the board
REG-RD-ID0: IC5.19 (I/O8); also elsewhere on the board
REG-RD-ID1: IC8.11 (I/O1); also elsewhere on the board
REG-RD-LO: IC8.17 (I/O6); also elsewhere on the board
RESET: IC2.18 (I/O7); also elsewhere on the board
SP/PC-ADDR-RD: IC6.19 (I/O8); also elsewhere on the board
SP/PC-DATA-RD-HI: IC6.18 (I/O7); also elsewhere on the board
SP/PC-DATA-RD-LO: IC6.17 (I/O6); also elsewhere on the board
SP/PC-DN: IC4.17 (I/O6); also elsewhere on the board
SP/PC-LD-HI: IC4.18 (I/O7); also elsewhere on the board
SP/PC-LD-LO: IC4.19 (I/O8); also elsewhere on the board
SP/PC-SEL: IC6.16 (I/O5); also elsewhere on the board
SP/PC-UP: IC4.16 (I/O5); also elsewhere on the board
SR-LD: IC3.15 (I/O4); also elsewhere on the board
UNUSED0: IC2.17 (I/O6); also elsewhere on the board
UNUSED1: IC2.16 (I/O5); also elsewhere on the board
UNUSED2: IC2.15 (I/O4); also elsewhere on the board
UNUSED3: IC2.13 (I/O3)
UNUSED4: IC2.12 (I/O2)
UNUSED5: IC2.11 (I/O1)
UNUSED6: IC1.19 (I/O8)
UNUSED7: IC1.18 (I/O7)
UNUSED8: IC1.17 (I/O6)
UNUSED9: IC1.16 (I/O5)
UNUSED10: IC1.15 (I/O4)
UNUSED11: IC1.13 (I/O3)
UNUSED12: IC1.12 (I/O2)
UNUSED13: IC1.11 (I/O1)
VCC: IC1.28 (VCC), IC2.28 (VCC), IC3.28 (VCC), IC4.28 (VCC), IC5.28 (VCC), IC6.28 (VCC), IC7.28 (VCC), IC8.28 (VCC); also elsewhere on the board

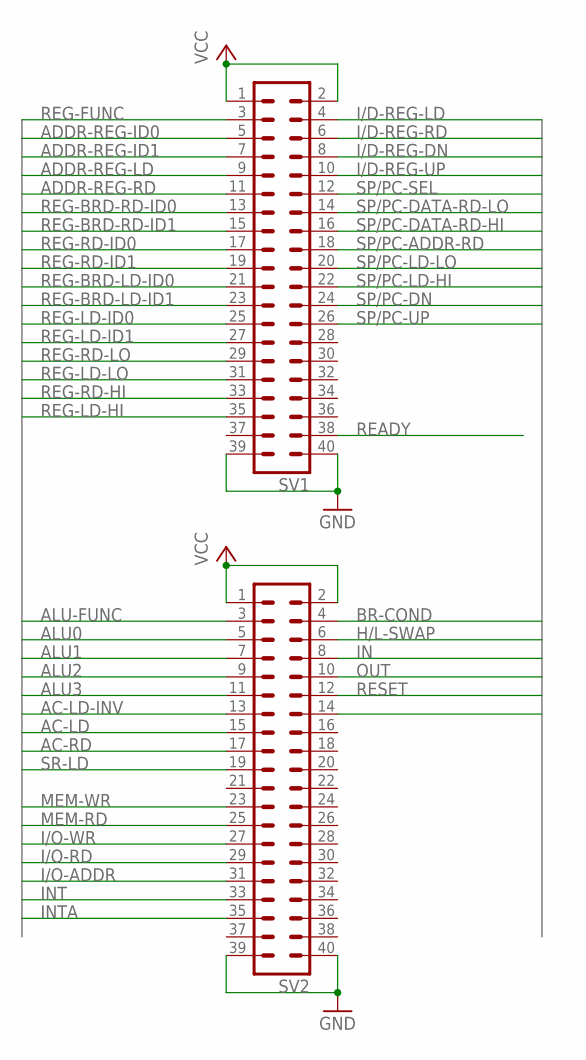
[picture p95: schematic Sequencer-Memory-V1.0-2.sch, sheet 2, Connector]

Parts:
SV1, SV2: MA20-2

Connections:
AC-LD: SV2.15; also elsewhere on the board
AC-LD-INV: SV2.13; also elsewhere on the board
AC-RD: SV2.17; also elsewhere on the board
ADDR-REG-ID0: SV1.5; also elsewhere on the board
ADDR-REG-ID1: SV1.7; also elsewhere on the board
ADDR-REG-LD: SV1.9; also elsewhere on the board
ADDR-REG-RD: SV1.11; also elsewhere on the board
ALU0: SV2.5; also elsewhere on the board
ALU1: SV2.7; also elsewhere on the board
ALU2: SV2.9; also elsewhere on the board
ALU3: SV2.11; also elsewhere on the board
ALU-FUNC: SV2.3; also elsewhere on the board
BR-COND: SV2.4; also elsewhere on the board
GND: SV1.39, SV1.40, SV2.39, SV2.40; also elsewhere on the board
H/L-SWAP: SV2.6; also elsewhere on the board
I/D-REG-DN: SV1.8; also elsewhere on the board
I/D-REG-LD: SV1.4; also elsewhere on the board
I/D-REG-RD: SV1.6; also elsewhere on the board
I/D-REG-UP: SV1.10; also elsewhere on the board
I/O-ADDR: SV2.31; also elsewhere on the board
I/O-RD: SV2.29; also elsewhere on the board
I/O-WR: SV2.27; also elsewhere on the board
IN: SV2.8; also elsewhere on the board
INT: SV2.33; also elsewhere on the board
INTA: SV2.35; also elsewhere on the board
MEM-RD: SV2.25; also elsewhere on the board
MEM-WR: SV2.23; also elsewhere on the board
OUT: SV2.10; also elsewhere on the board
READY: SV1.38; also elsewhere on the board
REG-BRD-LD-ID0: SV1.21; also elsewhere on the board
REG-BRD-LD-ID1: SV1.23; also elsewhere on the board
REG-BRD-RD-ID0: SV1.13; also elsewhere on the board
REG-BRD-RD-ID1: SV1.15; also elsewhere on the board
REG-FUNC: SV1.3; also elsewhere on the board
REG-LD-HI: SV1.35; also elsewhere on the board
REG-LD-ID0: SV1.25; also elsewhere on the board
REG-LD-ID1: SV1.27; also elsewhere on the board
REG-LD-LO: SV1.31; also elsewhere on the board
REG-RD-HI: SV1.33; also elsewhere on the board
REG-RD-ID0: SV1.17; also elsewhere on the board
REG-RD-ID1: SV1.19; also elsewhere on the board
REG-RD-LO: SV1.29; also elsewhere on the board
RESET: SV2.12; also elsewhere on the board
SP/PC-ADDR-RD: SV1.18; also elsewhere on the board
SP/PC-DATA-RD-HI: SV1.16; also elsewhere on the board
SP/PC-DATA-RD-LO: SV1.14; also elsewhere on the board
SP/PC-DN: SV1.24; also elsewhere on the board
SP/PC-LD-HI: SV1.22; also elsewhere on the board
SP/PC-LD-LO: SV1.20; also elsewhere on the board
SP/PC-SEL: SV1.12; also elsewhere on the board
SP/PC-UP: SV1.26; also elsewhere on the board
SR-LD: SV2.19; also elsewhere on the board
UNUSED0: SV2.14; also elsewhere on the board
VCC: SV1.1, SV1.2, SV2.1, SV2.2; also elsewhere on the board

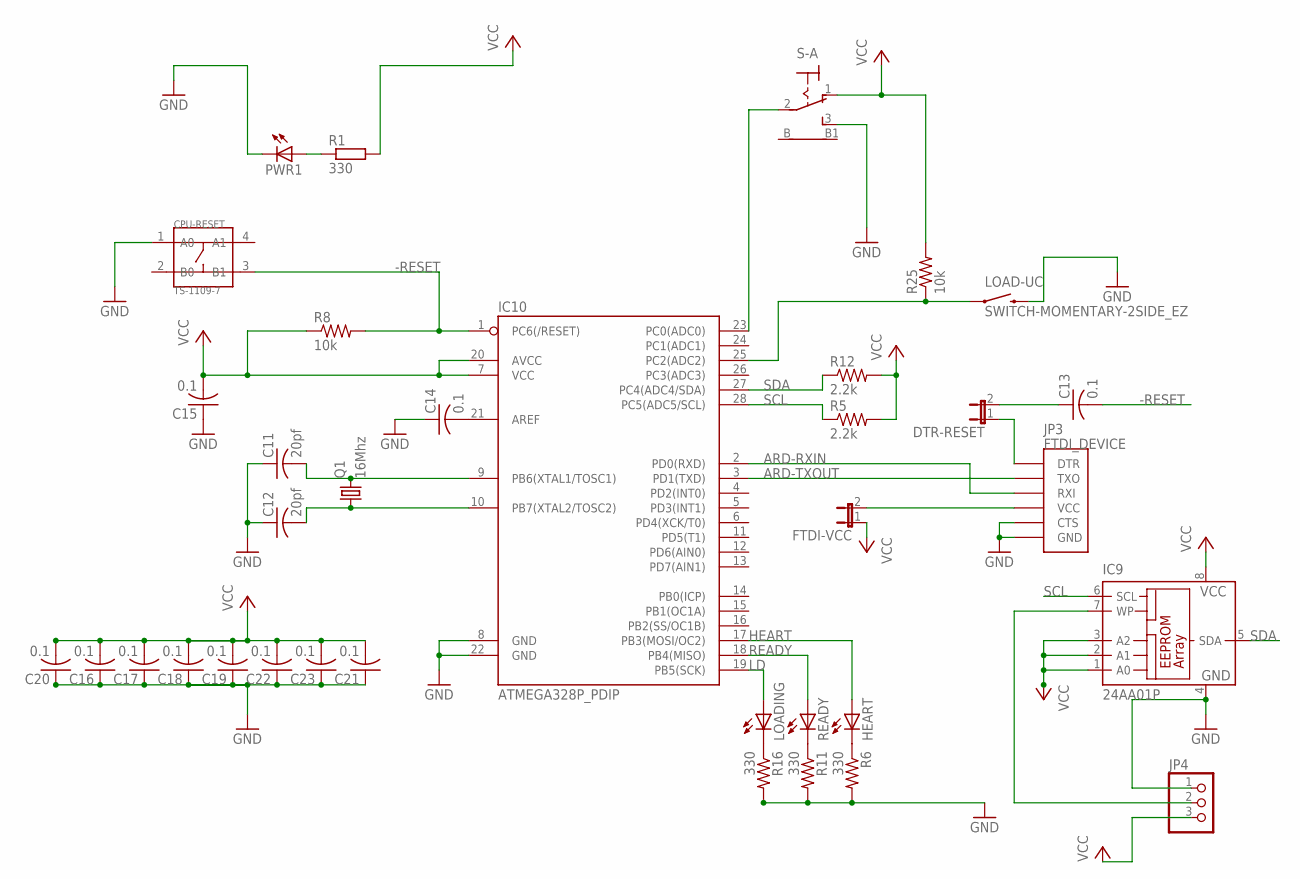
[picture p96: schematic Sequencer-Memory-V1.0-2.sch, sheet 3, CPU]

Parts:
C11, C12: 20pf; C025-024X044
C13, C14, C15, C16, C17, C18, C19, C20, C21, C22, C23: 0.1; C025-024X044
CPU-RESET: TS-1109-7; SW4-6.2X6.2X5.0MM
DTR-RESET: JP1E; JP1
FTDI-VCC: JP1E; JP1
HEART: LED5MM
IC9: 24AA01P; DIL8
IC10: ATMEGA328P_PDIP; DIL28-3
JP3: FTDI_DEVICE; FTDI_DEVICE_SIDE
JP4: PINHD-1X3; 1X03
LOAD-UC: SWITCH-MOMENTARY-2SIDE_EZ; TACTILE-PTH-SIDEEZ
LOADING: LED5MM
PWR1: LED5MM
Q1: 16Mhz; HC49/S
R1, R6, R11, R16: 330; 0207/10
R5, R12: 2.2k; 0207/10
R8, R25: 10k; 0207/10
READY: LED5MM
S-A: 9070-1W

Connections:
-RESET: C13.2, CPU-RESET.3 (B1), IC10.1 (PC6(/RESET)), R8.2; also elsewhere on the board
ARD-RXIN: IC10.2 (PD0(RXD)), JP3.P$3 (RXI)
ARD-TXOUT: IC10.3 (PD1(TXD)), JP3.P$2 (TXO)
GND: C11.1, C12.1, C14.1, C15.1, C16.1, C17.1, C18.1, C19.1, C20.1, C21.1, C22.1, C23.1, CPU-RESET.1 (A0), IC9.4 (GND), IC10.8 (GND), IC10.22 (GND), JP3.P$5 (CTS), JP3.P$6 (GND), JP4.1, LOAD-UC.2, PWR1.K (C), R6.2, R11.2, R16.2, S-A.3 (S); also elsewhere on the board
HEART: HEART.A, IC10.17 (PB3(MOSI/OC2))
LD: IC10.19 (PB5(SCK)), LOADING.A
unnamed: PWR1.A, R1.1
unnamed: C11.2, IC10.9 (PB6(XTAL1/TOSC1)), Q1.2
unnamed: C12.2, IC10.10 (PB7(XTAL2/TOSC2)), Q1.1
unnamed: C13.1, DTR-RESET.2
unnamed: C14.2, IC10.21 (AREF)
unnamed: R11.1, READY.K (C)
unnamed: LOADING.K (C), R16.1
unnamed: HEART.K (C), R6.1
unnamed: IC10.23 (PC0(ADC0)), S-A.2
unnamed: IC9.7 (WP), JP4.2
unnamed: DTR-RESET.1, JP3.P$1 (DTR)
unnamed: FTDI-VCC.2, JP3.P$4 (VCC)
unnamed: IC10.25 (PC2(ADC2)), LOAD-UC.1, R25.1
READY: IC10.18 (PB4(MISO)), READY.A; also elsewhere on the board
SCL: IC9.6 (SCL), IC10.28 (PC5(ADC5/SCL)), R5.1; also elsewhere on the board
SDA: IC9.5 (SDA), IC10.27 (PC4(ADC4/SDA)), R12.1; also elsewhere on the board
VCC: C15.2, C16.2, C17.2, C18.2, C19.2, C20.2, C21.2, C22.2, C23.2, FTDI-VCC.1, IC9.1 (A0), IC9.2 (A1), IC9.3 (A2), IC9.8 (VCC), IC10.7 (VCC), IC10.20 (AVCC), JP4.3, R1.2, R5.2, R8.1, R12.2, R25.2, S-A.1 (O); also elsewhere on the board

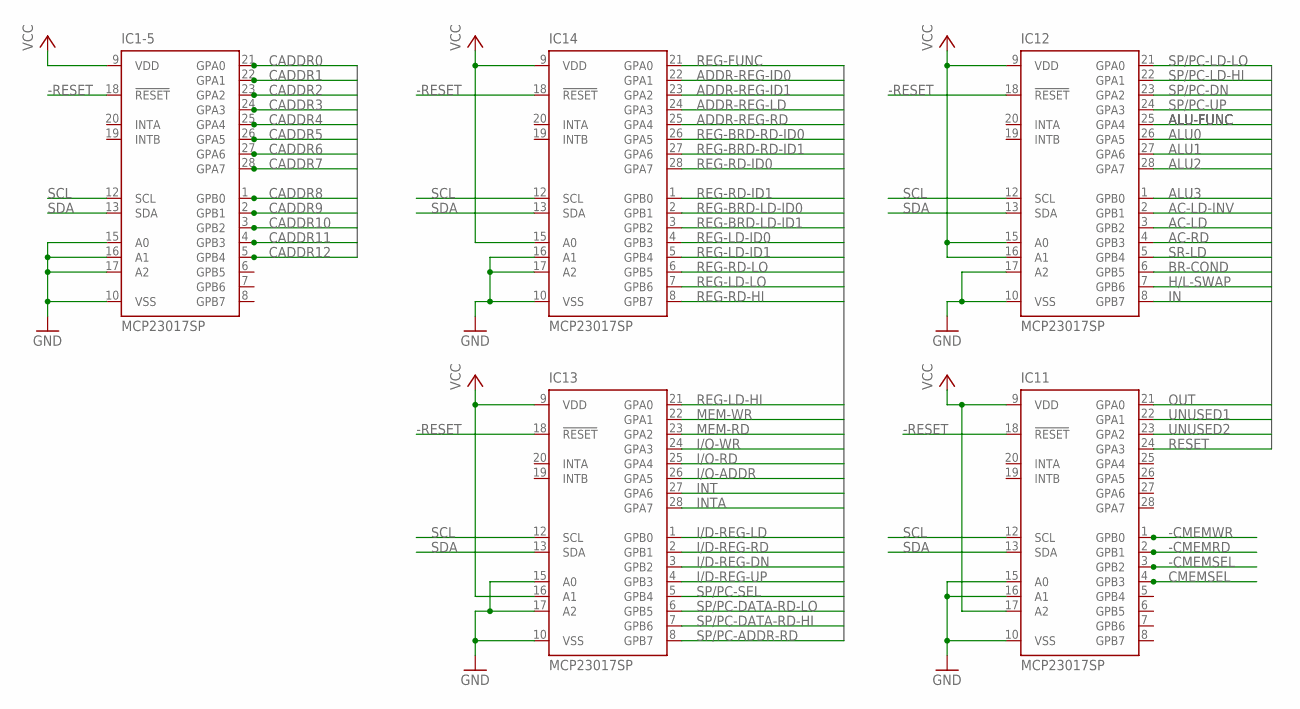
[picture p97: schematic Sequencer-Memory-V1.0-2.sch, sheet 4, IO]

Parts:
IC1-5, IC11, IC12, IC13, IC14: MCP23017SP; DIL28-3

Connections:
-CMEMRD: IC11.2 (GPB1); also elsewhere on the board
-CMEMSEL: IC11.3 (GPB2); also elsewhere on the board
-CMEMWR: IC11.1 (GPB0); also elsewhere on the board
-RESET: IC1-5.18 (!RESET), IC11.18 (!RESET), IC12.18 (!RESET), IC13.18 (!RESET), IC14.18 (!RESET); also elsewhere on the board
AC-LD: IC12.3 (GPB2); also elsewhere on the board
AC-LD-INV: IC12.2 (GPB1); also elsewhere on the board
AC-RD: IC12.4 (GPB3); also elsewhere on the board
ADDR-REG-ID0: IC14.22 (GPA1); also elsewhere on the board
ADDR-REG-ID1: IC14.23 (GPA2); also elsewhere on the board
ADDR-REG-LD: IC14.24 (GPA3); also elsewhere on the board
ADDR-REG-RD: IC14.25 (GPA4); also elsewhere on the board
ALU0: IC12.26 (GPA5); also elsewhere on the board
ALU1: IC12.27 (GPA6); also elsewhere on the board
ALU2: IC12.28 (GPA7); also elsewhere on the board
ALU3: IC12.1 (GPB0); also elsewhere on the board
ALU-FUNC: IC12.25 (GPA4); also elsewhere on the board
BR-COND: IC12.6 (GPB5); also elsewhere on the board
CADDR0: IC1-5.21 (GPA0); also elsewhere on the board
CADDR1: IC1-5.22 (GPA1); also elsewhere on the board
CADDR2: IC1-5.23 (GPA2); also elsewhere on the board
CADDR3: IC1-5.24 (GPA3); also elsewhere on the board
CADDR4: IC1-5.25 (GPA4); also elsewhere on the board
CADDR5: IC1-5.26 (GPA5); also elsewhere on the board
CADDR6: IC1-5.27 (GPA6); also elsewhere on the board
CADDR7: IC1-5.28 (GPA7); also elsewhere on the board
CADDR8: IC1-5.1 (GPB0); also elsewhere on the board
CADDR9: IC1-5.2 (GPB1); also elsewhere on the board
CADDR10: IC1-5.3 (GPB2); also elsewhere on the board
CADDR11: IC1-5.4 (GPB3); also elsewhere on the board
CADDR12: IC1-5.5 (GPB4); also elsewhere on the board
CMEMSEL: IC11.4 (GPB3); also elsewhere on the board
GND: IC1-5.10 (VSS), IC1-5.15 (A0), IC1-5.16 (A1), IC1-5.17 (A2), IC11.10 (VSS), IC11.15 (A0), IC11.16 (A1), IC12.10 (VSS), IC12.17 (A2), IC13.10 (VSS), IC13.15 (A0), IC13.17 (A2), IC14.10 (VSS), IC14.16 (A1), IC14.17 (A2); also elsewhere on the board
H/L-SWAP: IC12.7 (GPB6); also elsewhere on the board
I/D-REG-DN: IC13.3 (GPB2); also elsewhere on the board
I/D-REG-LD: IC13.1 (GPB0); also elsewhere on the board
I/D-REG-RD: IC13.2 (GPB1); also elsewhere on the board
I/D-REG-UP: IC13.4 (GPB3); also elsewhere on the board
I/O-ADDR: IC13.26 (GPA5); also elsewhere on the board
I/O-RD: IC13.25 (GPA4); also elsewhere on the board
I/O-WR: IC13.24 (GPA3); also elsewhere on the board
IN: IC12.8 (GPB7); also elsewhere on the board
INT: IC13.27 (GPA6); also elsewhere on the board
INTA: IC13.28 (GPA7); also elsewhere on the board
MEM-RD: IC13.23 (GPA2); also elsewhere on the board
MEM-WR: IC13.22 (GPA1); also elsewhere on the board
OUT: IC11.21 (GPA0); also elsewhere on the board
REG-BRD-LD-ID0: IC14.2 (GPB1); also elsewhere on the board
REG-BRD-LD-ID1: IC14.3 (GPB2); also elsewhere on the board
REG-BRD-RD-ID0: IC14.26 (GPA5); also elsewhere on the board
REG-BRD-RD-ID1: IC14.27 (GPA6); also elsewhere on the board
REG-FUNC: IC14.21 (GPA0); also elsewhere on the board
REG-LD-HI: IC13.21 (GPA0); also elsewhere on the board
REG-LD-ID0: IC14.4 (GPB3); also elsewhere on the board
REG-LD-ID1: IC14.5 (GPB4); also elsewhere on the board
REG-LD-LO: IC14.7 (GPB6); also elsewhere on the board
REG-RD-HI: IC14.8 (GPB7); also elsewhere on the board
REG-RD-ID0: IC14.28 (GPA7); also elsewhere on the board
REG-RD-ID1: IC14.1 (GPB0); also elsewhere on the board
REG-RD-LO: IC14.6 (GPB5); also elsewhere on the board
RESET: IC11.24 (GPA3); also elsewhere on the board
SCL: IC1-5.12 (SCL), IC11.12 (SCL), IC12.12 (SCL), IC13.12 (SCL), IC14.12 (SCL); also elsewhere on the board
SDA: IC1-5.13 (SDA), IC11.13 (SDA), IC12.13 (SDA), IC13.13 (SDA), IC14.13 (SDA); also elsewhere on the board
SP/PC-ADDR-RD: IC13.8 (GPB7); also elsewhere on the board
SP/PC-DATA-RD-HI: IC13.7 (GPB6); also elsewhere on the board
SP/PC-DATA-RD-LO: IC13.6 (GPB5); also elsewhere on the board
SP/PC-DN: IC12.23 (GPA2); also elsewhere on the board
SP/PC-LD-HI: IC12.22 (GPA1); also elsewhere on the board
SP/PC-LD-LO: IC12.21 (GPA0); also elsewhere on the board
SP/PC-SEL: IC13.5 (GPB4); also elsewhere on the board
SP/PC-UP: IC12.24 (GPA3); also elsewhere on the board
SR-LD: IC12.5 (GPB4); also elsewhere on the board
UNUSED1: IC11.22 (GPA1); also elsewhere on the board
UNUSED2: IC11.23 (GPA2); also elsewhere on the board
VCC: IC1-5.9 (VDD), IC11.9 (VDD), IC11.17 (A2), IC12.9 (VDD), IC12.15 (A0), IC12.16 (A1), IC13.9 (VDD), IC13.16 (A1), IC14.9 (VDD), IC14.15 (A0); also elsewhere on the board

Board: 2 copper layers, 50 parts (0 on the bottom side), 93 nets, no tracks yet.
