ksr/YACC1-2020/PCB/Working - Under Develolpment/Sequencer-Memory-V2.1/old-YACC1/Sequencer-Memory-V1.0-1.brd

## EAGLE design PCB/Working - Under Develolpment/Sequencer-Memory-V2.1/old-YACC1/Sequencer-Memory-V1.0-1.brd (2020-08-23, an earlier design)

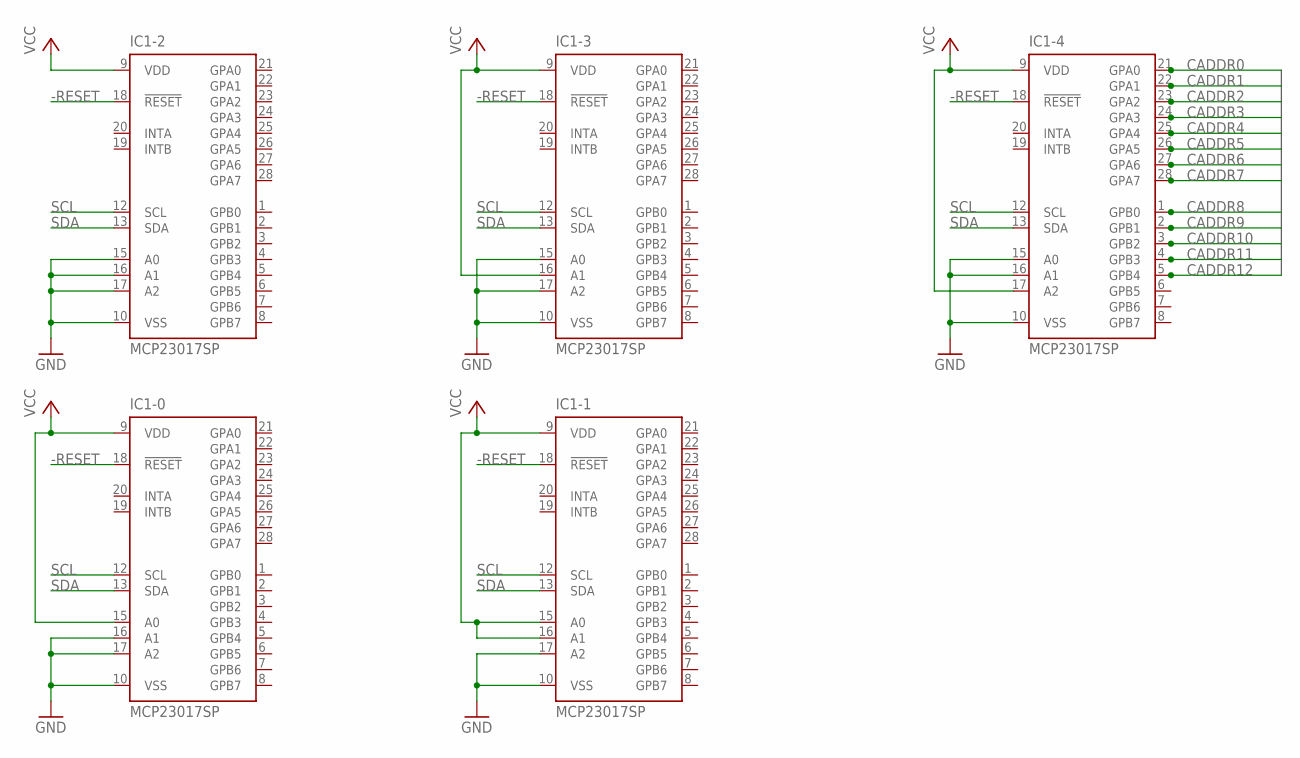
[picture p98: schematic Sequencer-Memory-V1.0-1.sch, sheet 1, I/O]

Parts:
IC1-0, IC1-1, IC1-2, IC1-3, IC1-4: MCP23017SP; DIL28-3

Connections:
-RESET: IC1-0.18 (!RESET), IC1-1.18 (!RESET), IC1-2.18 (!RESET), IC1-3.18 (!RESET), IC1-4.18 (!RESET); also elsewhere on the board
CADDR0: IC1-4.21 (GPA0); also elsewhere on the board
CADDR1: IC1-4.22 (GPA1); also elsewhere on the board
CADDR2: IC1-4.23 (GPA2); also elsewhere on the board
CADDR3: IC1-4.24 (GPA3); also elsewhere on the board
CADDR4: IC1-4.25 (GPA4); also elsewhere on the board
CADDR5: IC1-4.26 (GPA5); also elsewhere on the board
CADDR6: IC1-4.27 (GPA6); also elsewhere on the board
CADDR7: IC1-4.28 (GPA7); also elsewhere on the board
CADDR8: IC1-4.1 (GPB0); also elsewhere on the board
CADDR9: IC1-4.2 (GPB1); also elsewhere on the board
CADDR10: IC1-4.3 (GPB2); also elsewhere on the board
CADDR11: IC1-4.4 (GPB3); also elsewhere on the board
CADDR12: IC1-4.5 (GPB4); also elsewhere on the board
GND: IC1-0.10 (VSS), IC1-0.16 (A1), IC1-0.17 (A2), IC1-1.10 (VSS), IC1-1.17 (A2), IC1-2.10 (VSS), IC1-2.15 (A0), IC1-2.16 (A1), IC1-2.17 (A2), IC1-3.10 (VSS), IC1-3.15 (A0), IC1-3.17 (A2), IC1-4.10 (VSS), IC1-4.15 (A0), IC1-4.16 (A1); also elsewhere on the board
SCL: IC1-0.12 (SCL), IC1-1.12 (SCL), IC1-2.12 (SCL), IC1-3.12 (SCL), IC1-4.12 (SCL); also elsewhere on the board
SDA: IC1-0.13 (SDA), IC1-1.13 (SDA), IC1-2.13 (SDA), IC1-3.13 (SDA), IC1-4.13 (SDA); also elsewhere on the board
VCC: IC1-0.9 (VDD), IC1-0.15 (A0), IC1-1.9 (VDD), IC1-1.15 (A0), IC1-1.16 (A1), IC1-2.9 (VDD), IC1-3.9 (VDD), IC1-3.16 (A1), IC1-4.9 (VDD), IC1-4.17 (A2); also elsewhere on the board
