ksr/YACC1-2020/PCB/Production/IO-V-1.1/IO V1.1.brd

## EAGLE design PCB/Production/IO-V-1.1/IO V1.1.brd (continued)

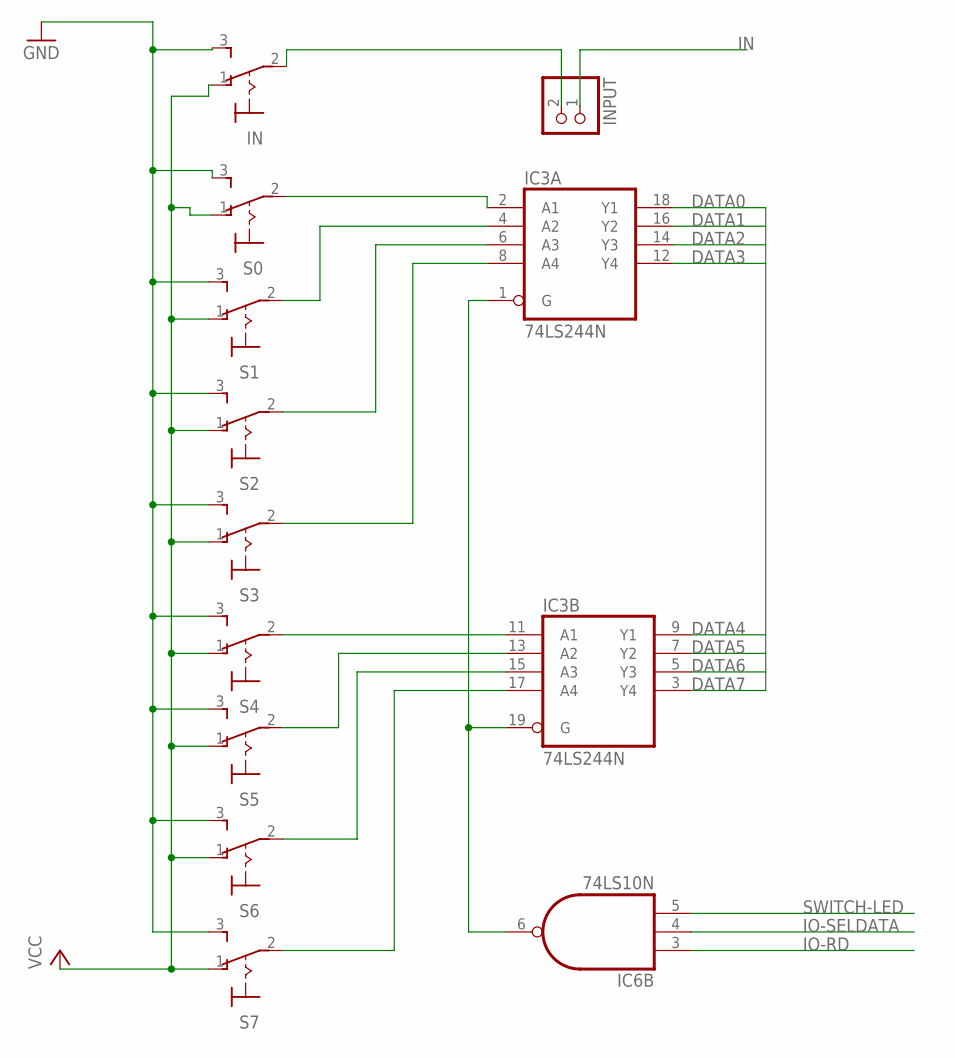
[picture p108: schematic IO V1.1.sch, sheet 4, Input]

Parts:
IC3: 74LS244N; DIL20
IC6: 74LS10N; DIL14
IN: M9040P
INPUT: PINHD-1X2; 1X02
S0, S1, S2, S3, S4, S5, S6, S7: M9040P

Connections:
DATA0: IC3.18 (Y1); also elsewhere on the board
DATA1: IC3.16 (Y2); also elsewhere on the board
DATA2: IC3.14 (Y3); also elsewhere on the board
DATA3: IC3.12 (Y4); also elsewhere on the board
DATA4: IC3.9 (Y1); also elsewhere on the board
DATA5: IC3.7 (Y2); also elsewhere on the board
DATA6: IC3.5 (Y3); also elsewhere on the board
DATA7: IC3.3 (Y4); also elsewhere on the board
GND: IC3.10 (GND), IC6.7 (GND), IN.3 (S), S0.3 (S), S1.3 (S), S2.3 (S), S3.3 (S), S4.3 (S), S5.3 (S), S6.3 (S), S7.3 (S); also elsewhere on the board
IN: INPUT.1; also elsewhere on the board
IO-RD: IC6.3 (I0); also elsewhere on the board
IO-SELDATA: IC6.4 (I1); also elsewhere on the board
unnamed: IC3.2 (A1), S0.2
unnamed: IC3.4 (A2), S1.2
unnamed: IC3.6 (A3), S2.2
unnamed: IC3.8 (A4), S3.2
unnamed: IC3.11 (A1), S4.2
unnamed: IC3.13 (A2), S5.2
unnamed: IC3.15 (A3), S6.2
unnamed: IC3.17 (A4), S7.2
unnamed: IC3.1 (G), IC3.19 (G), IC6.6 (O)
unnamed: IN.2, INPUT.2
SWITCH-LED: IC6.5 (I2); also elsewhere on the board
VCC: IC3.20 (VCC), IC6.14 (VCC), IN.1 (O), S0.1 (O), S1.1 (O), S2.1 (O), S3.1 (O), S4.1 (O), S5.1 (O), S6.1 (O), S7.1 (O); also elsewhere on the board

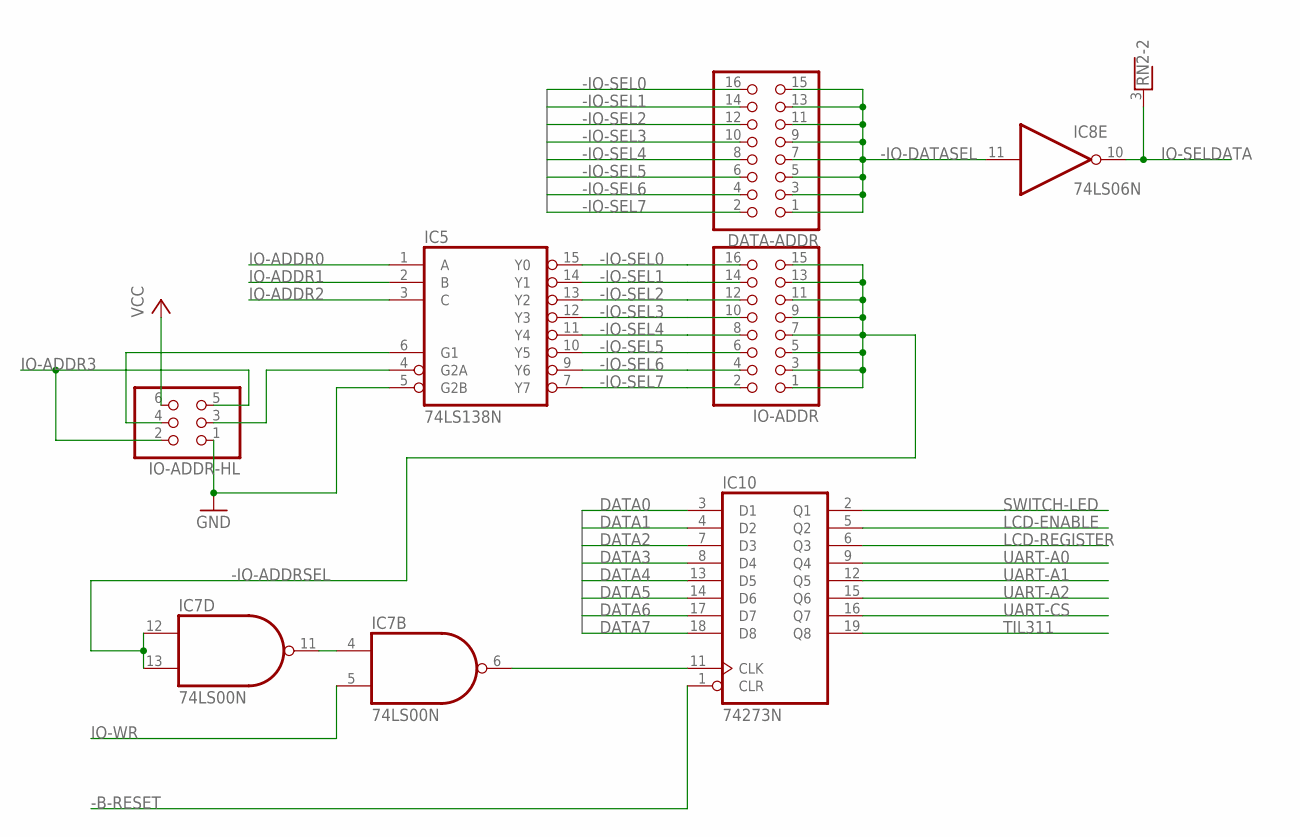
[picture p109: schematic IO V1.1.sch, sheet 5, Board Select logic]

Parts:
DATA-ADDR: PINHD-2X8; 2X08
IC5: 74LS138N; DIL16
IC7: 74LS00N; DIL14
IC8: 74LS06N; DIL14
IC10: 74273N; DIL20
IO-ADDR: PINHD-2X8; 2X08
IO-ADDR-HL: PINHD-2X3; 2X03
RN2: RNX6; RN-7

Connections:
-B-RESET: IC10.1 (CLR); also elsewhere on the board
-IO-ADDRSEL: IC7.12 (I0), IC7.13 (I1), IO-ADDR.1, IO-ADDR.3, IO-ADDR.5, IO-ADDR.7, IO-ADDR.9, IO-ADDR.11, IO-ADDR.13, IO-ADDR.15
-IO-DATASEL: DATA-ADDR.1, DATA-ADDR.3, DATA-ADDR.5, DATA-ADDR.7, DATA-ADDR.9, DATA-ADDR.11, DATA-ADDR.13, DATA-ADDR.15, IC8.11 (I)
-IO-SEL0: DATA-ADDR.16, IC5.15 (Y0), IO-ADDR.16
-IO-SEL1: DATA-ADDR.14, IC5.14 (Y1), IO-ADDR.14
-IO-SEL2: DATA-ADDR.12, IC5.13 (Y2), IO-ADDR.12
-IO-SEL3: DATA-ADDR.10, IC5.12 (Y3), IO-ADDR.10
-IO-SEL4: DATA-ADDR.8, IC5.11 (Y4), IO-ADDR.8
-IO-SEL5: DATA-ADDR.6, IC5.10 (Y5), IO-ADDR.6
-IO-SEL6: DATA-ADDR.4, IC5.9 (Y6), IO-ADDR.4
-IO-SEL7: DATA-ADDR.2, IC5.7 (Y7), IO-ADDR.2
DATA0: IC10.3 (D1); also elsewhere on the board
DATA1: IC10.4 (D2); also elsewhere on the board
DATA2: IC10.7 (D3); also elsewhere on the board
DATA3: IC10.8 (D4); also elsewhere on the board
DATA4: IC10.13 (D5); also elsewhere on the board
DATA5: IC10.14 (D6); also elsewhere on the board
DATA6: IC10.17 (D7); also elsewhere on the board
DATA7: IC10.18 (D8); also elsewhere on the board
GND: IC5.5 (G2B), IC5.8 (GND), IC7.7 (GND), IC8.7 (GND), IC10.10 (GND), IO-ADDR-HL.1; also elsewhere on the board
IO-ADDR0: IC5.1 (A); also elsewhere on the board
IO-ADDR1: IC5.2 (B); also elsewhere on the board
IO-ADDR2: IC5.3 (C); also elsewhere on the board
IO-ADDR3: IO-ADDR-HL.2, IO-ADDR-HL.5; also elsewhere on the board
IO-SELDATA: IC8.10 (O), RN2.3; also elsewhere on the board
IO-WR: IC7.5 (I1); also elsewhere on the board
LCD-ENABLE: IC10.5 (Q2); also elsewhere on the board
LCD-REGISTER: IC10.6 (Q3); also elsewhere on the board
unnamed: IC5.4 (G2A), IO-ADDR-HL.3
unnamed: IC5.6 (G1), IO-ADDR-HL.4
unnamed: IC7.6 (O), IC10.11 (CLK)
unnamed: IC7.4 (I0), IC7.11 (O)
SWITCH-LED: IC10.2 (Q1); also elsewhere on the board
TIL311: IC10.19 (Q8); also elsewhere on the board
UART-A0: IC10.9 (Q4); also elsewhere on the board
UART-A1: IC10.12 (Q5); also elsewhere on the board
UART-A2: IC10.15 (Q6); also elsewhere on the board
UART-CS: IC10.16 (Q7); also elsewhere on the board
VCC: IC5.16 (VCC), IC7.14 (VCC), IC8.14 (VCC), IC10.20 (VCC), IO-ADDR-HL.6; also elsewhere on the board

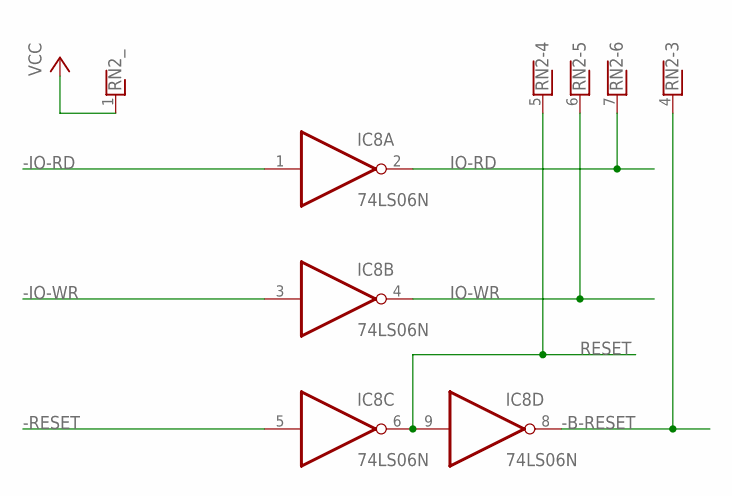
[picture p110: schematic IO V1.1.sch, sheet 6, Bus Buffering]

Parts:
IC8: 74LS06N; DIL14
RN2: RNX6; RN-7

Connections:
-B-RESET: IC8.8 (O), RN2.4; also elsewhere on the board
-IO-RD: IC8.1 (I); also elsewhere on the board
-IO-WR: IC8.3 (I); also elsewhere on the board
-RESET: IC8.5 (I); also elsewhere on the board
GND: IC8.7 (GND); also elsewhere on the board
IO-RD: IC8.2 (O), RN2.7; also elsewhere on the board
IO-WR: IC8.4 (O), RN2.6; also elsewhere on the board
RESET: IC8.6 (O), IC8.9 (I), RN2.5; also elsewhere on the board
VCC: IC8.14 (VCC), RN2.1; also elsewhere on the board

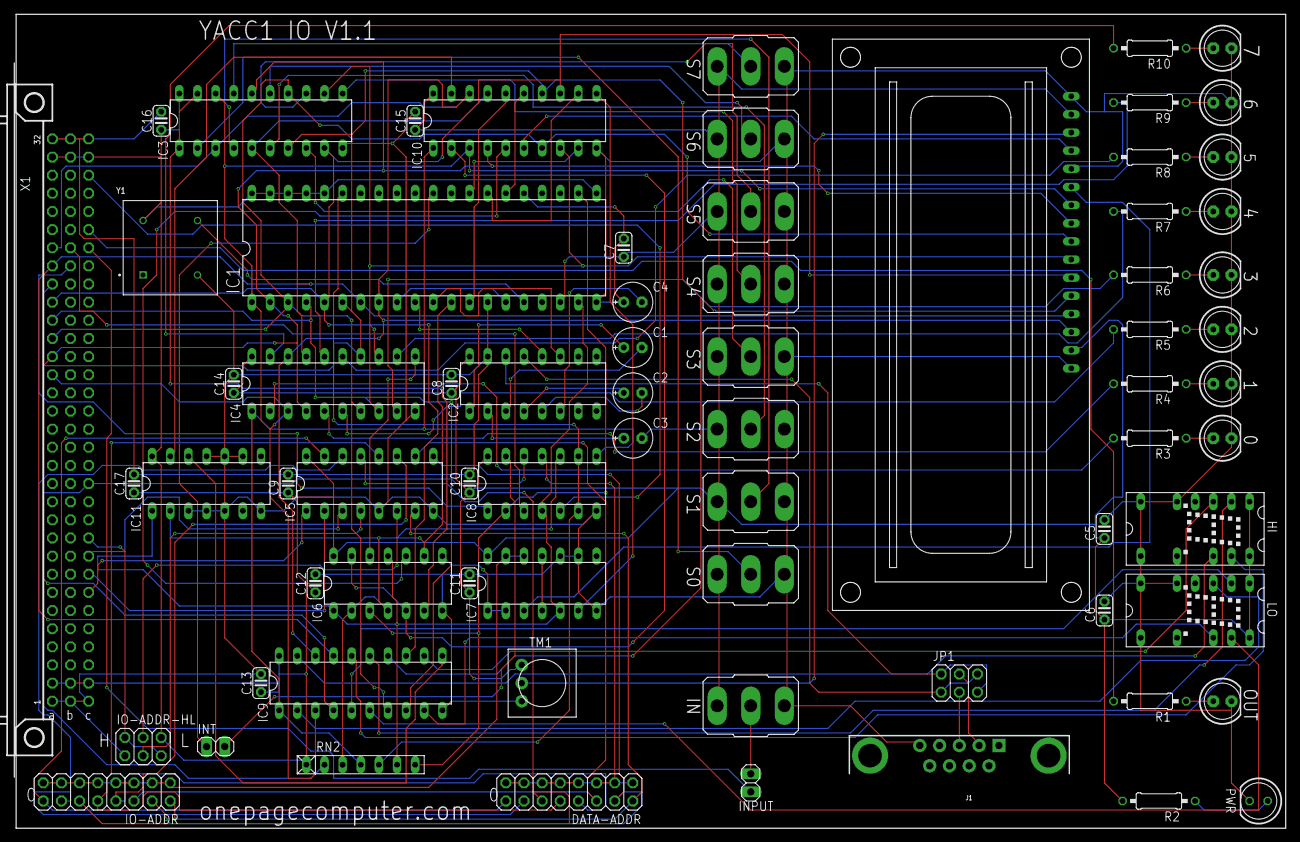
[picture p111: board IO V1.1.brd from above]

Board: 2 copper layers, 177.8 x 114.0 mm, 71 parts (0 on the bottom side), 104 nets.
