ksr/YACC1-2020/PCB/Production/Index Registers - no address1.0/Index Registers - 1.0.brd

## EAGLE design PCB/Production/Index Registers - no address1.0/Index Registers - 1.0.brd (2020-08-23)

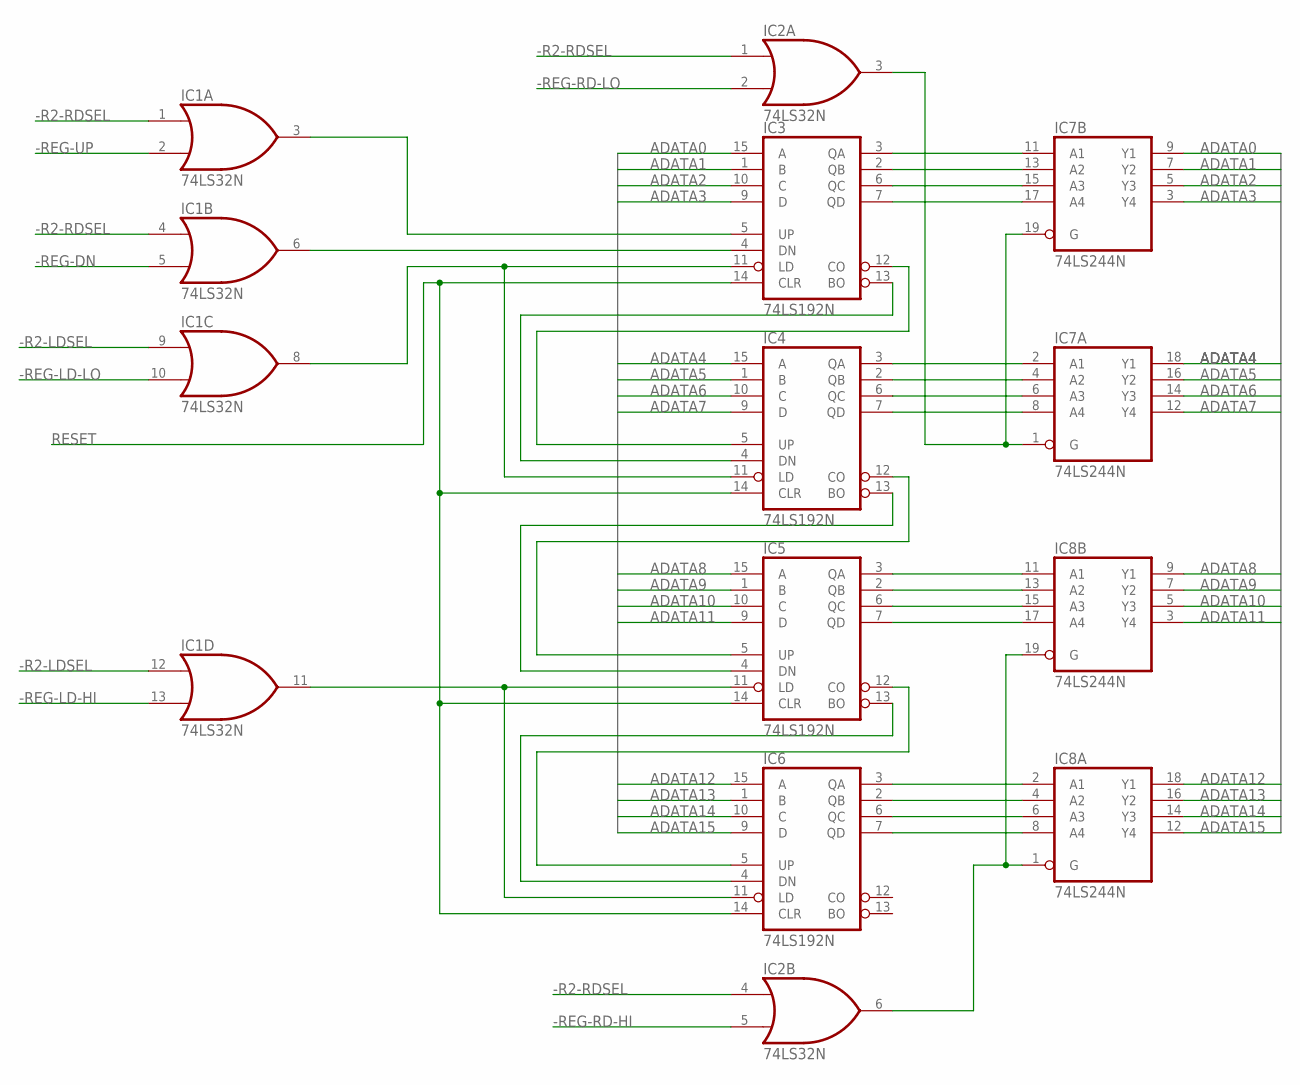
[picture p112: schematic Index Registers - 1.0.sch, sheet 1, R2]

Parts:
IC1, IC2: 74LS32N; DIL14
IC3, IC4, IC5, IC6: 74LS192N; DIL16
IC7, IC8: 74LS244N; DIL20

Connections:
-R2-LDSEL: IC1.9 (I0), IC1.12 (I0); also elsewhere on the board
-R2-RDSEL: IC1.1 (I0), IC1.4 (I0), IC2.1 (I0), IC2.4 (I0); also elsewhere on the board
-REG-DN: IC1.5 (I1); also elsewhere on the board
-REG-LD-HI: IC1.13 (I1); also elsewhere on the board
-REG-LD-LO: IC1.10 (I1); also elsewhere on the board
-REG-RD-HI: IC2.5 (I1); also elsewhere on the board
-REG-RD-LO: IC2.2 (I1); also elsewhere on the board
-REG-UP: IC1.2 (I1); also elsewhere on the board
ADATA0: IC3.15 (A), IC7.9 (Y1); also elsewhere on the board
ADATA1: IC3.1 (B), IC7.7 (Y2); also elsewhere on the board
ADATA2: IC3.10 (C), IC7.5 (Y3); also elsewhere on the board
ADATA3: IC3.9 (D), IC7.3 (Y4); also elsewhere on the board
ADATA4: IC4.15 (A), IC7.18 (Y1); also elsewhere on the board
ADATA5: IC4.1 (B), IC7.16 (Y2); also elsewhere on the board
ADATA6: IC4.10 (C), IC7.14 (Y3); also elsewhere on the board
ADATA7: IC4.9 (D), IC7.12 (Y4); also elsewhere on the board
ADATA8: IC5.15 (A), IC8.9 (Y1); also elsewhere on the board
ADATA9: IC5.1 (B), IC8.7 (Y2); also elsewhere on the board
ADATA10: IC5.10 (C), IC8.5 (Y3); also elsewhere on the board
ADATA11: IC5.9 (D), IC8.3 (Y4); also elsewhere on the board
ADATA12: IC6.15 (A), IC8.18 (Y1); also elsewhere on the board
ADATA13: IC6.1 (B), IC8.16 (Y2); also elsewhere on the board
ADATA14: IC6.10 (C), IC8.14 (Y3); also elsewhere on the board
ADATA15: IC6.9 (D), IC8.12 (Y4); also elsewhere on the board
GND: IC1.7 (GND), IC2.7 (GND), IC3.8 (GND), IC4.8 (GND), IC5.8 (GND), IC6.8 (GND), IC7.10 (GND), IC8.10 (GND); also elsewhere on the board
unnamed: IC3.13 (BO), IC4.4 (DN)
unnamed: IC3.12 (CO), IC4.5 (UP)
unnamed: IC4.13 (BO), IC5.4 (DN)
unnamed: IC4.12 (CO), IC5.5 (UP)
unnamed: IC5.13 (BO), IC6.4 (DN)
unnamed: IC5.12 (CO), IC6.5 (UP)
unnamed: IC1.8 (O), IC3.11 (LD), IC4.11 (LD)
unnamed: IC1.3 (O), IC3.5 (UP)
unnamed: IC1.6 (O), IC3.4 (DN)
unnamed: IC2.3 (O), IC7.1 (G), IC7.19 (G)
unnamed: IC2.6 (O), IC8.1 (G), IC8.19 (G)
unnamed: IC1.11 (O), IC5.11 (LD), IC6.11 (LD)
unnamed: IC3.3 (QA), IC7.11 (A1)
unnamed: IC3.2 (QB), IC7.13 (A2)
unnamed: IC3.6 (QC), IC7.15 (A3)
unnamed: IC3.7 (QD), IC7.17 (A4)
unnamed: IC4.3 (QA), IC7.2 (A1)
unnamed: IC4.2 (QB), IC7.4 (A2)
unnamed: IC4.6 (QC), IC7.6 (A3)
unnamed: IC4.7 (QD), IC7.8 (A4)
unnamed: IC5.3 (QA), IC8.11 (A1)
unnamed: IC5.2 (QB), IC8.13 (A2)
unnamed: IC5.6 (QC), IC8.15 (A3)
unnamed: IC5.7 (QD), IC8.17 (A4)
unnamed: IC6.3 (QA), IC8.2 (A1)
unnamed: IC6.2 (QB), IC8.4 (A2)
unnamed: IC6.6 (QC), IC8.6 (A3)
unnamed: IC6.7 (QD), IC8.8 (A4)
RESET: IC3.14 (CLR), IC4.14 (CLR), IC5.14 (CLR), IC6.14 (CLR); also elsewhere on the board
VCC: IC1.14 (VCC), IC2.14 (VCC), IC3.16 (VCC), IC4.16 (VCC), IC5.16 (VCC), IC6.16 (VCC), IC7.20 (VCC), IC8.20 (VCC); also elsewhere on the board

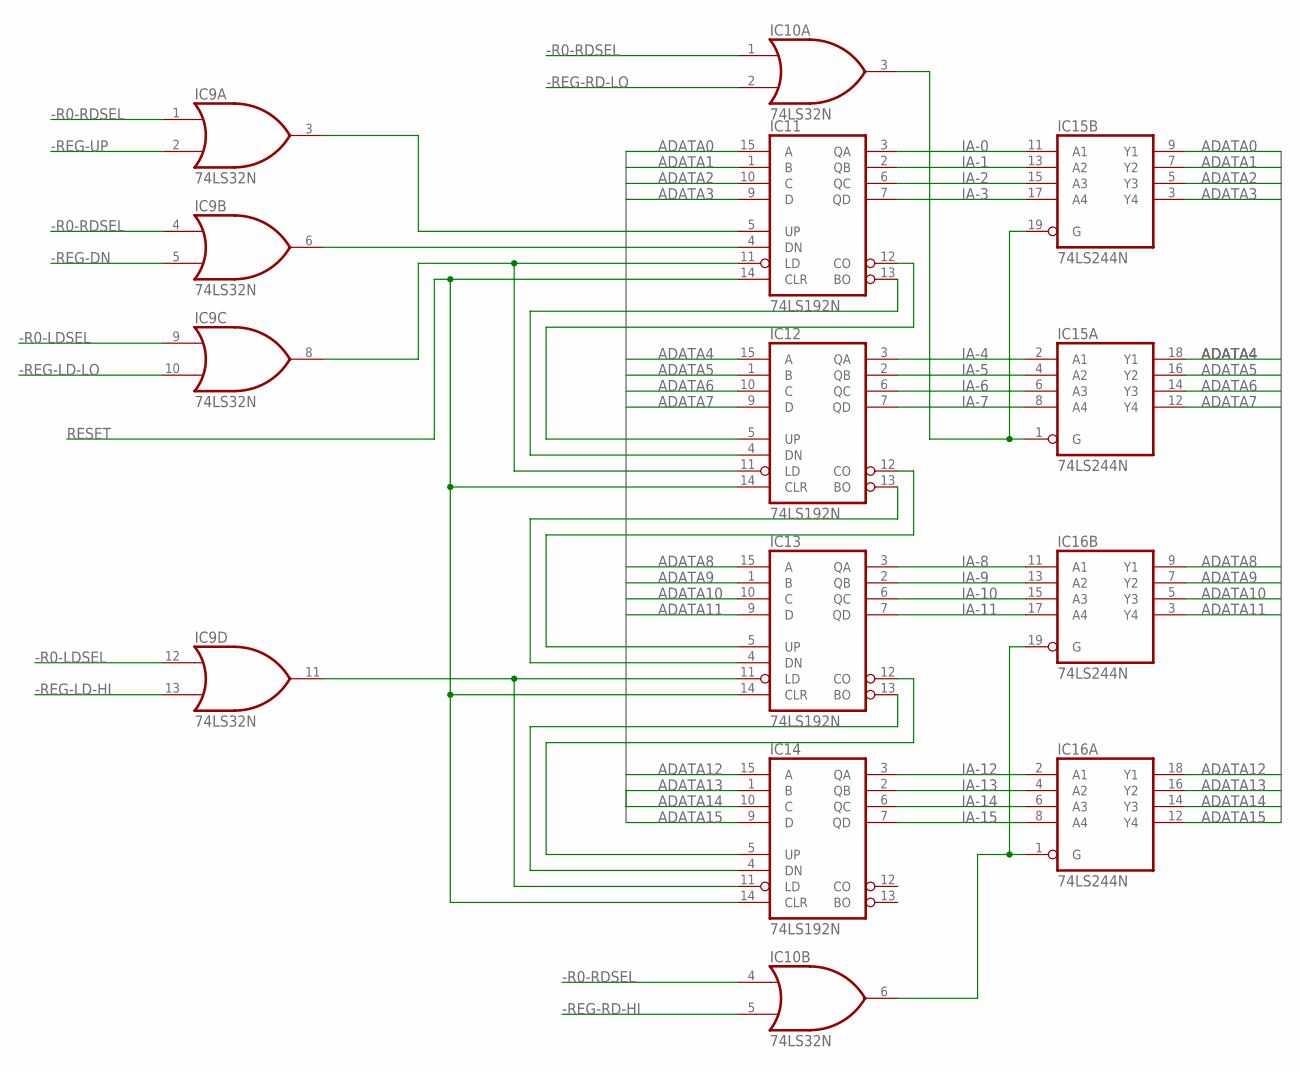
[picture p113: schematic Index Registers - 1.0.sch, sheet 2, R0]

Parts:
IC9, IC10: 74LS32N; DIL14
IC11, IC12, IC13, IC14: 74LS192N; DIL16
IC15, IC16: 74LS244N; DIL20

Connections:
-R0-LDSEL: IC9.9 (I0), IC9.12 (I0); also elsewhere on the board
-R0-RDSEL: IC9.1 (I0), IC9.4 (I0), IC10.1 (I0), IC10.4 (I0); also elsewhere on the board
-REG-DN: IC9.5 (I1); also elsewhere on the board
-REG-LD-HI: IC9.13 (I1); also elsewhere on the board
-REG-LD-LO: IC9.10 (I1); also elsewhere on the board
-REG-RD-HI: IC10.5 (I1); also elsewhere on the board
-REG-RD-LO: IC10.2 (I1); also elsewhere on the board
-REG-UP: IC9.2 (I1); also elsewhere on the board
ADATA0: IC11.15 (A), IC15.9 (Y1); also elsewhere on the board
ADATA1: IC11.1 (B), IC15.7 (Y2); also elsewhere on the board
ADATA2: IC11.10 (C), IC15.5 (Y3); also elsewhere on the board
ADATA3: IC11.9 (D), IC15.3 (Y4); also elsewhere on the board
ADATA4: IC12.15 (A), IC15.18 (Y1); also elsewhere on the board
ADATA5: IC12.1 (B), IC15.16 (Y2); also elsewhere on the board
ADATA6: IC12.10 (C), IC15.14 (Y3); also elsewhere on the board
ADATA7: IC12.9 (D), IC15.12 (Y4); also elsewhere on the board
ADATA8: IC13.15 (A), IC16.9 (Y1); also elsewhere on the board
ADATA9: IC13.1 (B), IC16.7 (Y2); also elsewhere on the board
ADATA10: IC13.10 (C), IC16.5 (Y3); also elsewhere on the board
ADATA11: IC13.9 (D), IC16.3 (Y4); also elsewhere on the board
ADATA12: IC14.15 (A), IC16.18 (Y1); also elsewhere on the board
ADATA13: IC14.1 (B), IC16.16 (Y2); also elsewhere on the board
ADATA14: IC14.10 (C), IC16.14 (Y3); also elsewhere on the board
ADATA15: IC14.9 (D), IC16.12 (Y4); also elsewhere on the board
GND: IC9.7 (GND), IC10.7 (GND), IC11.8 (GND), IC12.8 (GND), IC13.8 (GND), IC14.8 (GND), IC15.10 (GND), IC16.10 (GND); also elsewhere on the board
IA-0: IC11.3 (QA), IC15.11 (A1); also elsewhere on the board
IA-1: IC11.2 (QB), IC15.13 (A2); also elsewhere on the board
IA-2: IC11.6 (QC), IC15.15 (A3); also elsewhere on the board
IA-3: IC11.7 (QD), IC15.17 (A4); also elsewhere on the board
IA-4: IC12.3 (QA), IC15.2 (A1); also elsewhere on the board
IA-5: IC12.2 (QB), IC15.4 (A2); also elsewhere on the board
IA-6: IC12.6 (QC), IC15.6 (A3); also elsewhere on the board
IA-7: IC12.7 (QD), IC15.8 (A4); also elsewhere on the board
IA-8: IC13.3 (QA), IC16.11 (A1); also elsewhere on the board
IA-9: IC13.2 (QB), IC16.13 (A2); also elsewhere on the board
IA-10: IC13.6 (QC), IC16.15 (A3); also elsewhere on the board
IA-11: IC13.7 (QD), IC16.17 (A4); also elsewhere on the board
IA-12: IC14.3 (QA), IC16.2 (A1); also elsewhere on the board
IA-13: IC14.2 (QB), IC16.4 (A2); also elsewhere on the board
IA-14: IC14.6 (QC), IC16.6 (A3); also elsewhere on the board
IA-15: IC14.7 (QD), IC16.8 (A4); also elsewhere on the board
unnamed: IC11.13 (BO), IC12.4 (DN)
unnamed: IC11.12 (CO), IC12.5 (UP)
unnamed: IC12.13 (BO), IC13.4 (DN)
unnamed: IC12.12 (CO), IC13.5 (UP)
unnamed: IC13.13 (BO), IC14.4 (DN)
unnamed: IC13.12 (CO), IC14.5 (UP)
unnamed: IC9.8 (O), IC11.11 (LD), IC12.11 (LD)
unnamed: IC9.3 (O), IC11.5 (UP)
unnamed: IC9.6 (O), IC11.4 (DN)
unnamed: IC10.3 (O), IC15.1 (G), IC15.19 (G)
unnamed: IC10.6 (O), IC16.1 (G), IC16.19 (G)
unnamed: IC9.11 (O), IC13.11 (LD), IC14.11 (LD)
RESET: IC11.14 (CLR), IC12.14 (CLR), IC13.14 (CLR), IC14.14 (CLR); also elsewhere on the board
VCC: IC9.14 (VCC), IC10.14 (VCC), IC11.16 (VCC), IC12.16 (VCC), IC13.16 (VCC), IC14.16 (VCC), IC15.20 (VCC), IC16.20 (VCC); also elsewhere on the board

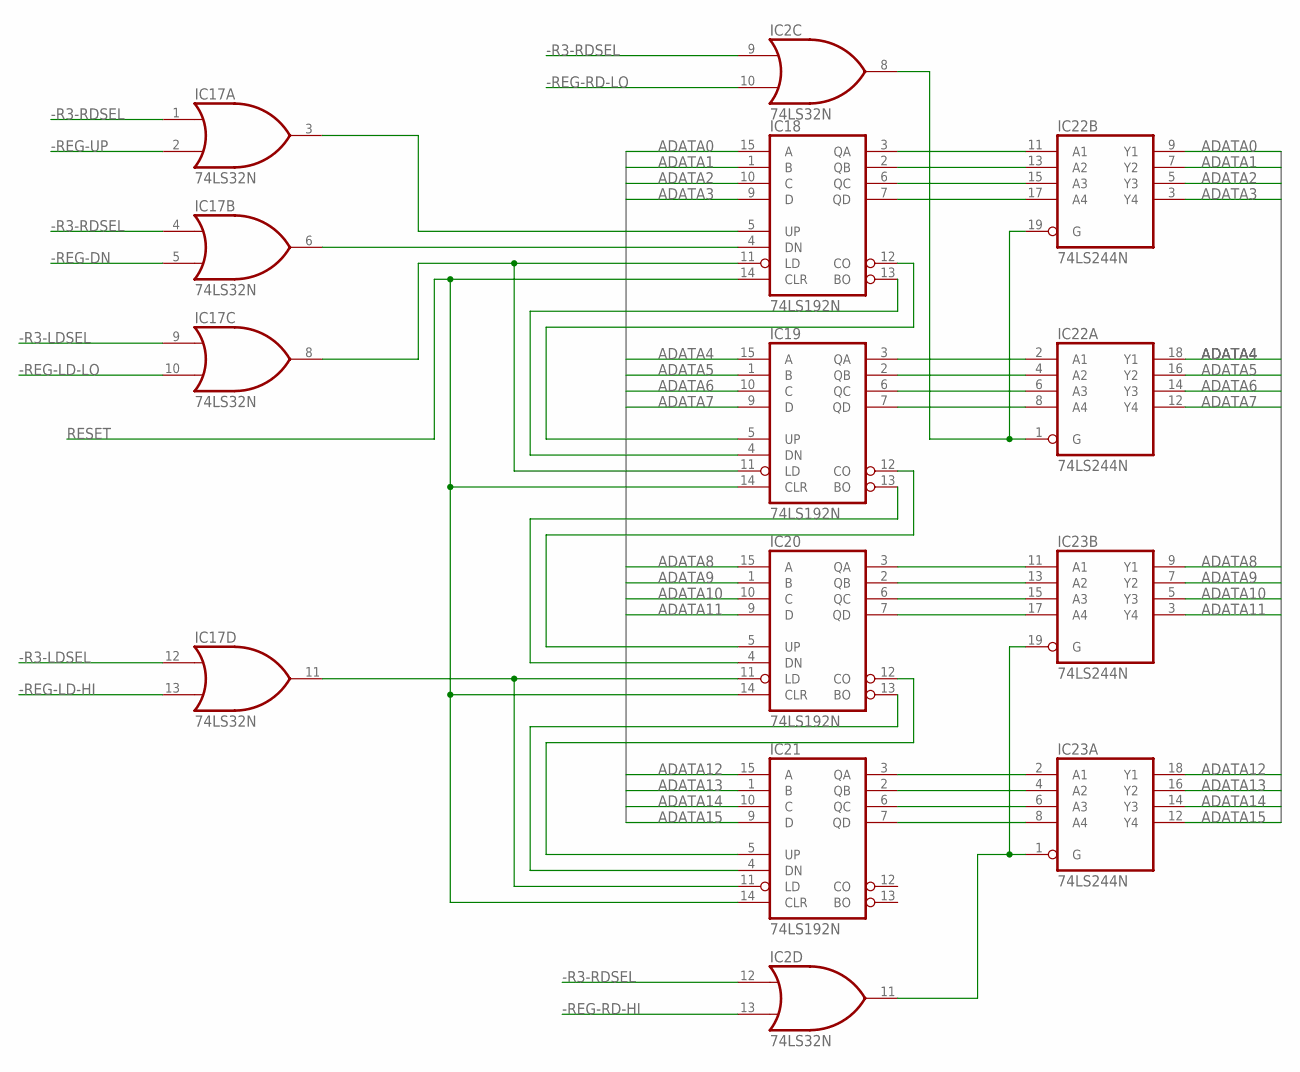
[picture p114: schematic Index Registers - 1.0.sch, sheet 3, R3]

Parts:
IC2, IC17: 74LS32N; DIL14
IC18, IC19, IC20, IC21: 74LS192N; DIL16
IC22, IC23: 74LS244N; DIL20

Connections:
-R3-LDSEL: IC17.9 (I0), IC17.12 (I0); also elsewhere on the board
-R3-RDSEL: IC2.9 (I0), IC2.12 (I0), IC17.1 (I0), IC17.4 (I0); also elsewhere on the board
-REG-DN: IC17.5 (I1); also elsewhere on the board
-REG-LD-HI: IC17.13 (I1); also elsewhere on the board
-REG-LD-LO: IC17.10 (I1); also elsewhere on the board
-REG-RD-HI: IC2.13 (I1); also elsewhere on the board
-REG-RD-LO: IC2.10 (I1); also elsewhere on the board
-REG-UP: IC17.2 (I1); also elsewhere on the board
ADATA0: IC18.15 (A), IC22.9 (Y1); also elsewhere on the board
ADATA1: IC18.1 (B), IC22.7 (Y2); also elsewhere on the board
ADATA2: IC18.10 (C), IC22.5 (Y3); also elsewhere on the board
ADATA3: IC18.9 (D), IC22.3 (Y4); also elsewhere on the board
ADATA4: IC19.15 (A), IC22.18 (Y1); also elsewhere on the board
ADATA5: IC19.1 (B), IC22.16 (Y2); also elsewhere on the board
ADATA6: IC19.10 (C), IC22.14 (Y3); also elsewhere on the board
ADATA7: IC19.9 (D), IC22.12 (Y4); also elsewhere on the board
ADATA8: IC20.15 (A), IC23.9 (Y1); also elsewhere on the board
ADATA9: IC20.1 (B), IC23.7 (Y2); also elsewhere on the board
ADATA10: IC20.10 (C), IC23.5 (Y3); also elsewhere on the board
ADATA11: IC20.9 (D), IC23.3 (Y4); also elsewhere on the board
ADATA12: IC21.15 (A), IC23.18 (Y1); also elsewhere on the board
ADATA13: IC21.1 (B), IC23.16 (Y2); also elsewhere on the board
ADATA14: IC21.10 (C), IC23.14 (Y3); also elsewhere on the board
ADATA15: IC21.9 (D), IC23.12 (Y4); also elsewhere on the board
GND: IC2.7 (GND), IC17.7 (GND), IC18.8 (GND), IC19.8 (GND), IC20.8 (GND), IC21.8 (GND), IC22.10 (GND), IC23.10 (GND); also elsewhere on the board
unnamed: IC18.13 (BO), IC19.4 (DN)
unnamed: IC18.12 (CO), IC19.5 (UP)
unnamed: IC19.13 (BO), IC20.4 (DN)
unnamed: IC19.12 (CO), IC20.5 (UP)
unnamed: IC20.13 (BO), IC21.4 (DN)
unnamed: IC20.12 (CO), IC21.5 (UP)
unnamed: IC17.8 (O), IC18.11 (LD), IC19.11 (LD)
unnamed: IC17.3 (O), IC18.5 (UP)
unnamed: IC17.6 (O), IC18.4 (DN)
unnamed: IC18.3 (QA), IC22.11 (A1)
unnamed: IC18.2 (QB), IC22.13 (A2)
unnamed: IC18.6 (QC), IC22.15 (A3)
unnamed: IC18.7 (QD), IC22.17 (A4)
unnamed: IC2.8 (O), IC22.1 (G), IC22.19 (G)
unnamed: IC2.11 (O), IC23.1 (G), IC23.19 (G)
unnamed: IC17.11 (O), IC20.11 (LD), IC21.11 (LD)
unnamed: IC19.3 (QA), IC22.2 (A1)
unnamed: IC19.2 (QB), IC22.4 (A2)
unnamed: IC19.6 (QC), IC22.6 (A3)
unnamed: IC19.7 (QD), IC22.8 (A4)
unnamed: IC20.3 (QA), IC23.11 (A1)
unnamed: IC20.2 (QB), IC23.13 (A2)
unnamed: IC20.6 (QC), IC23.15 (A3)
unnamed: IC20.7 (QD), IC23.17 (A4)
unnamed: IC21.3 (QA), IC23.2 (A1)
unnamed: IC21.2 (QB), IC23.4 (A2)
unnamed: IC21.6 (QC), IC23.6 (A3)
unnamed: IC21.7 (QD), IC23.8 (A4)
RESET: IC18.14 (CLR), IC19.14 (CLR), IC20.14 (CLR), IC21.14 (CLR); also elsewhere on the board
VCC: IC2.14 (VCC), IC17.14 (VCC), IC18.16 (VCC), IC19.16 (VCC), IC20.16 (VCC), IC21.16 (VCC), IC22.20 (VCC), IC23.20 (VCC); also elsewhere on the board

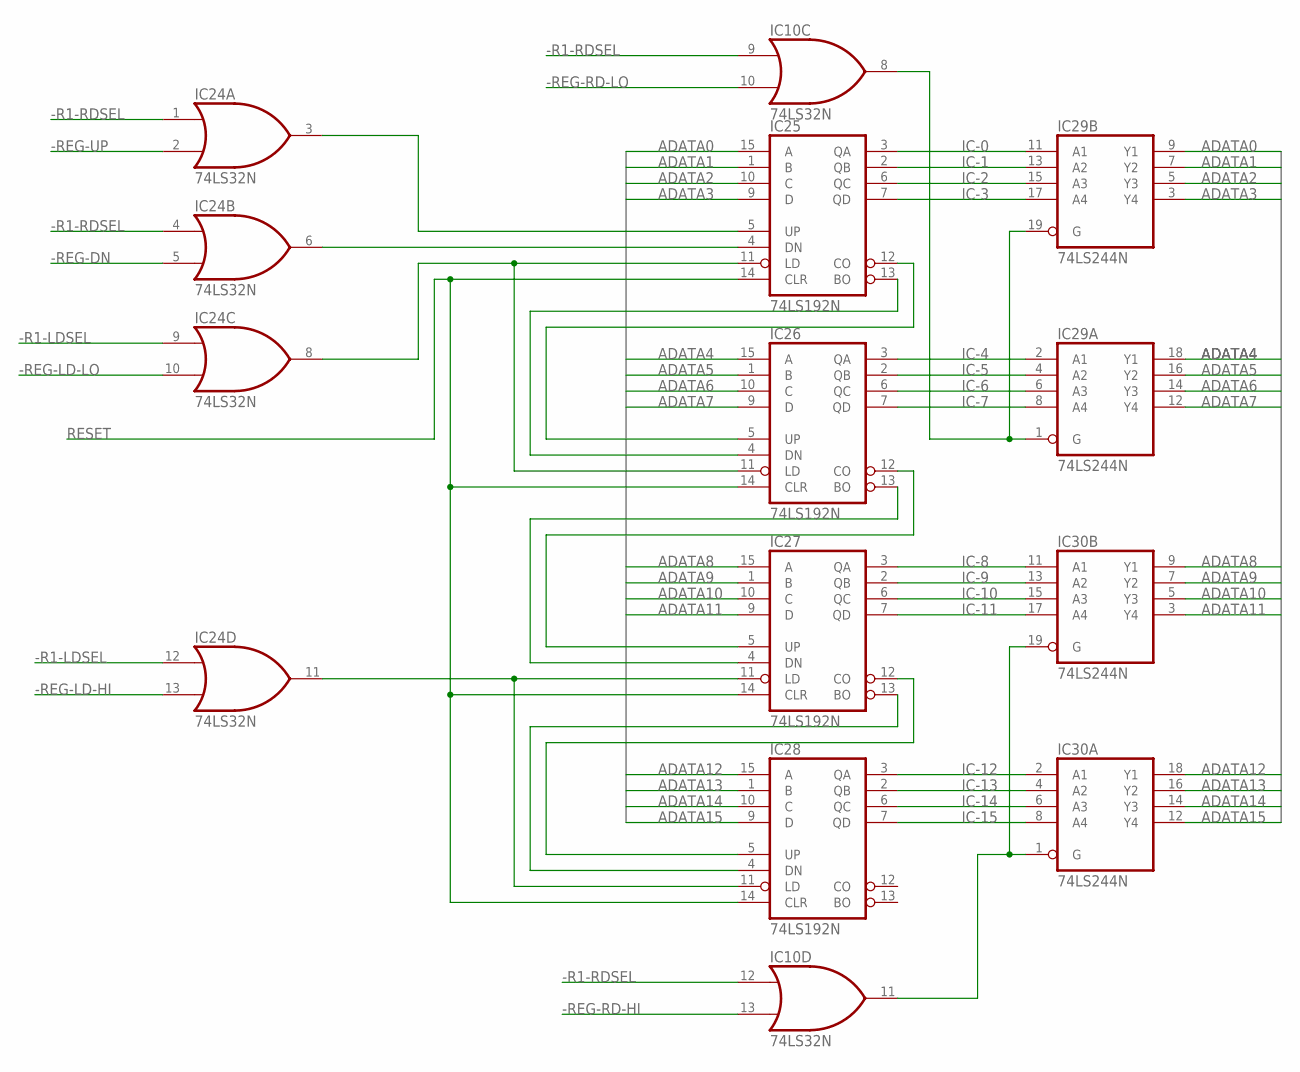
[picture p115: schematic Index Registers - 1.0.sch, sheet 4, R1]

Parts:
IC10, IC24: 74LS32N; DIL14
IC25, IC26, IC27, IC28: 74LS192N; DIL16
IC29, IC30: 74LS244N; DIL20

Connections:
-R1-LDSEL: IC24.9 (I0), IC24.12 (I0); also elsewhere on the board
-R1-RDSEL: IC10.9 (I0), IC10.12 (I0), IC24.1 (I0), IC24.4 (I0); also elsewhere on the board
-REG-DN: IC24.5 (I1); also elsewhere on the board
-REG-LD-HI: IC24.13 (I1); also elsewhere on the board
-REG-LD-LO: IC24.10 (I1); also elsewhere on the board
-REG-RD-HI: IC10.13 (I1); also elsewhere on the board
-REG-RD-LO: IC10.10 (I1); also elsewhere on the board
-REG-UP: IC24.2 (I1); also elsewhere on the board
ADATA0: IC25.15 (A), IC29.9 (Y1); also elsewhere on the board
ADATA1: IC25.1 (B), IC29.7 (Y2); also elsewhere on the board
ADATA2: IC25.10 (C), IC29.5 (Y3); also elsewhere on the board
ADATA3: IC25.9 (D), IC29.3 (Y4); also elsewhere on the board
ADATA4: IC26.15 (A), IC29.18 (Y1); also elsewhere on the board
ADATA5: IC26.1 (B), IC29.16 (Y2); also elsewhere on the board
ADATA6: IC26.10 (C), IC29.14 (Y3); also elsewhere on the board
ADATA7: IC26.9 (D), IC29.12 (Y4); also elsewhere on the board
ADATA8: IC27.15 (A), IC30.9 (Y1); also elsewhere on the board
ADATA9: IC27.1 (B), IC30.7 (Y2); also elsewhere on the board
ADATA10: IC27.10 (C), IC30.5 (Y3); also elsewhere on the board
ADATA11: IC27.9 (D), IC30.3 (Y4); also elsewhere on the board
ADATA12: IC28.15 (A), IC30.18 (Y1); also elsewhere on the board
ADATA13: IC28.1 (B), IC30.16 (Y2); also elsewhere on the board
ADATA14: IC28.10 (C), IC30.14 (Y3); also elsewhere on the board
ADATA15: IC28.9 (D), IC30.12 (Y4); also elsewhere on the board
GND: IC10.7 (GND), IC24.7 (GND), IC25.8 (GND), IC26.8 (GND), IC27.8 (GND), IC28.8 (GND), IC29.10 (GND), IC30.10 (GND); also elsewhere on the board
IC-0: IC25.3 (QA), IC29.11 (A1); also elsewhere on the board
IC-1: IC25.2 (QB), IC29.13 (A2); also elsewhere on the board
IC-2: IC25.6 (QC), IC29.15 (A3); also elsewhere on the board
IC-3: IC25.7 (QD), IC29.17 (A4); also elsewhere on the board
IC-4: IC26.3 (QA), IC29.2 (A1); also elsewhere on the board
IC-5: IC26.2 (QB), IC29.4 (A2); also elsewhere on the board
IC-6: IC26.6 (QC), IC29.6 (A3); also elsewhere on the board
IC-7: IC26.7 (QD), IC29.8 (A4); also elsewhere on the board
IC-8: IC27.3 (QA), IC30.11 (A1); also elsewhere on the board
IC-9: IC27.2 (QB), IC30.13 (A2); also elsewhere on the board
IC-10: IC27.6 (QC), IC30.15 (A3); also elsewhere on the board
IC-11: IC27.7 (QD), IC30.17 (A4); also elsewhere on the board
IC-12: IC28.3 (QA), IC30.2 (A1)
IC-13: IC28.2 (QB), IC30.4 (A2); also elsewhere on the board
IC-14: IC28.6 (QC), IC30.6 (A3); also elsewhere on the board
IC-15: IC28.7 (QD), IC30.8 (A4); also elsewhere on the board
unnamed: IC25.13 (BO), IC26.4 (DN)
unnamed: IC25.12 (CO), IC26.5 (UP)
unnamed: IC26.13 (BO), IC27.4 (DN)
unnamed: IC26.12 (CO), IC27.5 (UP)
unnamed: IC27.13 (BO), IC28.4 (DN)
unnamed: IC27.12 (CO), IC28.5 (UP)
unnamed: IC24.8 (O), IC25.11 (LD), IC26.11 (LD)
unnamed: IC24.3 (O), IC25.5 (UP)
unnamed: IC24.6 (O), IC25.4 (DN)
unnamed: IC10.8 (O), IC29.1 (G), IC29.19 (G)
unnamed: IC10.11 (O), IC30.1 (G), IC30.19 (G)
unnamed: IC24.11 (O), IC27.11 (LD), IC28.11 (LD)
RESET: IC25.14 (CLR), IC26.14 (CLR), IC27.14 (CLR), IC28.14 (CLR); also elsewhere on the board
VCC: IC10.14 (VCC), IC24.14 (VCC), IC25.16 (VCC), IC26.16 (VCC), IC27.16 (VCC), IC28.16 (VCC), IC29.20 (VCC), IC30.20 (VCC); also elsewhere on the board

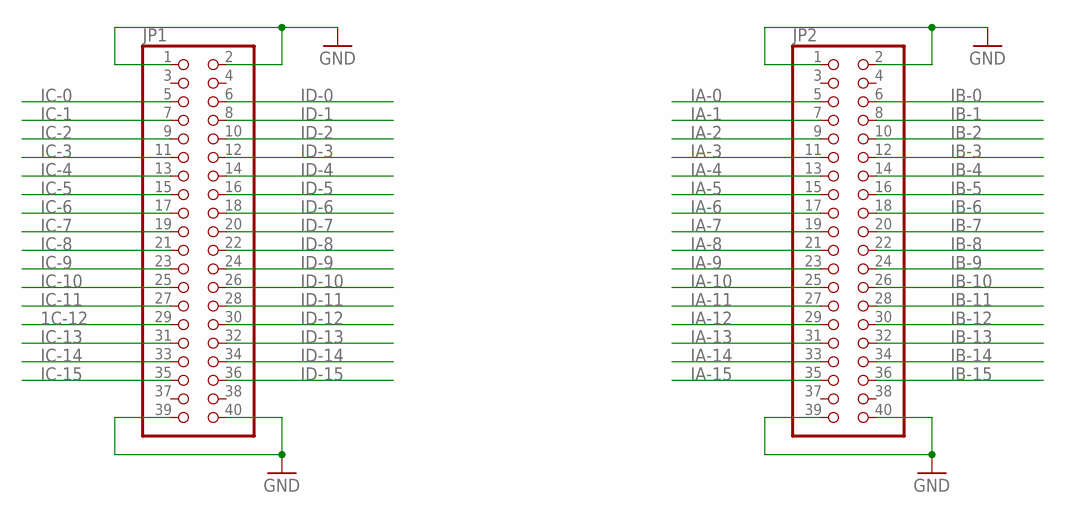
[picture p116: schematic Index Registers - 1.0.sch, sheet 5, Front Panel]

Parts:
JP1, JP2: PINHD-2X20; 2X20

Connections:
1C-12: JP1.29
GND: JP1.1, JP1.2, JP1.39, JP1.40, JP2.1, JP2.2, JP2.39, JP2.40; also elsewhere on the board
IA-0: JP2.5; also elsewhere on the board
IA-1: JP2.7; also elsewhere on the board
IA-2: JP2.9; also elsewhere on the board
IA-3: JP2.11; also elsewhere on the board
IA-4: JP2.13; also elsewhere on the board
IA-5: JP2.15; also elsewhere on the board
IA-6: JP2.17; also elsewhere on the board
IA-7: JP2.19; also elsewhere on the board
IA-8: JP2.21; also elsewhere on the board
IA-9: JP2.23; also elsewhere on the board
IA-10: JP2.25; also elsewhere on the board
IA-11: JP2.27; also elsewhere on the board
IA-12: JP2.29; also elsewhere on the board
IA-13: JP2.31; also elsewhere on the board
IA-14: JP2.33; also elsewhere on the board
IA-15: JP2.35; also elsewhere on the board
IB-0: JP2.6
IB-1: JP2.8
IB-2: JP2.10
IB-3: JP2.12
IB-4: JP2.14
IB-5: JP2.16
IB-6: JP2.18
IB-7: JP2.20
IB-8: JP2.22
IB-9: JP2.24
IB-10: JP2.26
IB-11: JP2.28
IB-12: JP2.30
IB-13: JP2.32
IB-14: JP2.34
IB-15: JP2.36
IC-0: JP1.5; also elsewhere on the board
IC-1: JP1.7; also elsewhere on the board
IC-2: JP1.9; also elsewhere on the board
IC-3: JP1.11; also elsewhere on the board
IC-4: JP1.13; also elsewhere on the board
IC-5: JP1.15; also elsewhere on the board
IC-6: JP1.17; also elsewhere on the board
IC-7: JP1.19; also elsewhere on the board
IC-8: JP1.21; also elsewhere on the board
IC-9: JP1.23; also elsewhere on the board
IC-10: JP1.25; also elsewhere on the board
IC-11: JP1.27; also elsewhere on the board
IC-13: JP1.31; also elsewhere on the board
IC-14: JP1.33; also elsewhere on the board
IC-15: JP1.35; also elsewhere on the board
ID-0: JP1.6
ID-1: JP1.8
ID-2: JP1.10
ID-3: JP1.12
ID-4: JP1.14
ID-5: JP1.16
ID-6: JP1.18
ID-7: JP1.20
ID-8: JP1.22
ID-9: JP1.24
ID-10: JP1.26
ID-11: JP1.28
ID-12: JP1.30
ID-13: JP1.32
ID-14: JP1.34
ID-15: JP1.36
