ksr/YACC1-2020/PCB/Production/Index Registers - no address1.0/Index Registers - 1.0.brd

## EAGLE design PCB/Production/Index Registers - no address1.0/Index Registers - 1.0.brd (continued)

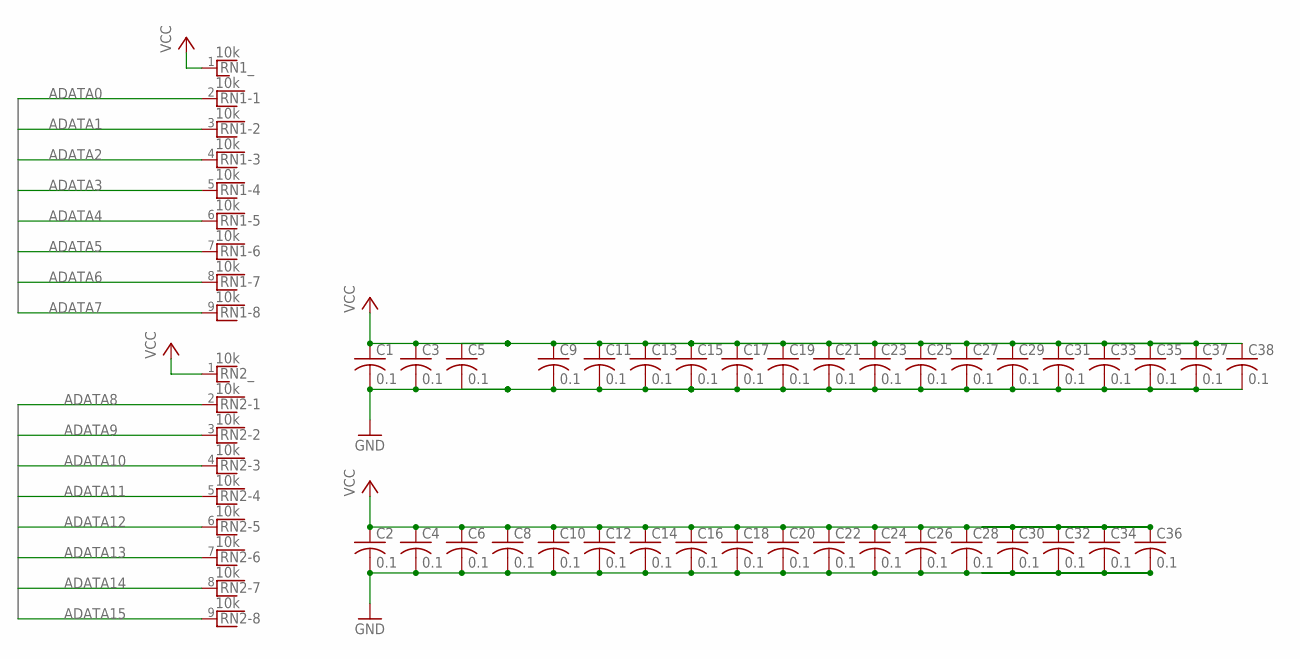
[picture p117: schematic Index Registers - 1.0.sch, sheet 6, PULLUPS & BYPASS & UNUSED]

Parts:
C1, C2, C3, C4, C5, C6, C8, C9, C10, C11, C12, C13, C14, C15, C16, C17, C18, C19, C20, C21, C22, C23, C24, C25, C26, C27, C28, C29, C30, C31, C32, C33, C34, C35, C36, C37, C38: 0.1; C025-040X050
RN1, RN2: 10k; RN-9

Connections:
ADATA0: RN1.2; also elsewhere on the board
ADATA1: RN1.3; also elsewhere on the board
ADATA2: RN1.4; also elsewhere on the board
ADATA3: RN1.5; also elsewhere on the board
ADATA4: RN1.6; also elsewhere on the board
ADATA5: RN1.7; also elsewhere on the board
ADATA6: RN1.8; also elsewhere on the board
ADATA7: RN1.9; also elsewhere on the board
ADATA8: RN2.2; also elsewhere on the board
ADATA9: RN2.3; also elsewhere on the board
ADATA10: RN2.4; also elsewhere on the board
ADATA11: RN2.5; also elsewhere on the board
ADATA12: RN2.6; also elsewhere on the board
ADATA13: RN2.7; also elsewhere on the board
ADATA14: RN2.8; also elsewhere on the board
ADATA15: RN2.9; also elsewhere on the board
GND: C1.2, C2.2, C3.2, C4.2, C5.2, C6.2, C8.2, C9.2, C10.2, C11.2, C12.2, C13.2, C14.2, C15.2, C16.2, C17.2, C18.2, C19.2, C20.2, C21.2, C22.2, C23.2, C24.2, C25.2, C26.2, C27.2, C28.2, C29.2, C30.2, C31.2, C32.2, C33.2, C34.2, C35.2, C36.2, C37.2, C38.2; also elsewhere on the board
VCC: C1.1, C2.1, C3.1, C4.1, C5.1, C6.1, C8.1, C9.1, C10.1, C11.1, C12.1, C13.1, C14.1, C15.1, C16.1, C17.1, C18.1, C19.1, C20.1, C21.1, C22.1, C23.1, C24.1, C25.1, C26.1, C27.1, C28.1, C29.1, C30.1, C31.1, C32.1, C33.1, C34.1, C35.1, C36.1, C37.1, C38.1, RN1.1, RN2.1; also elsewhere on the board

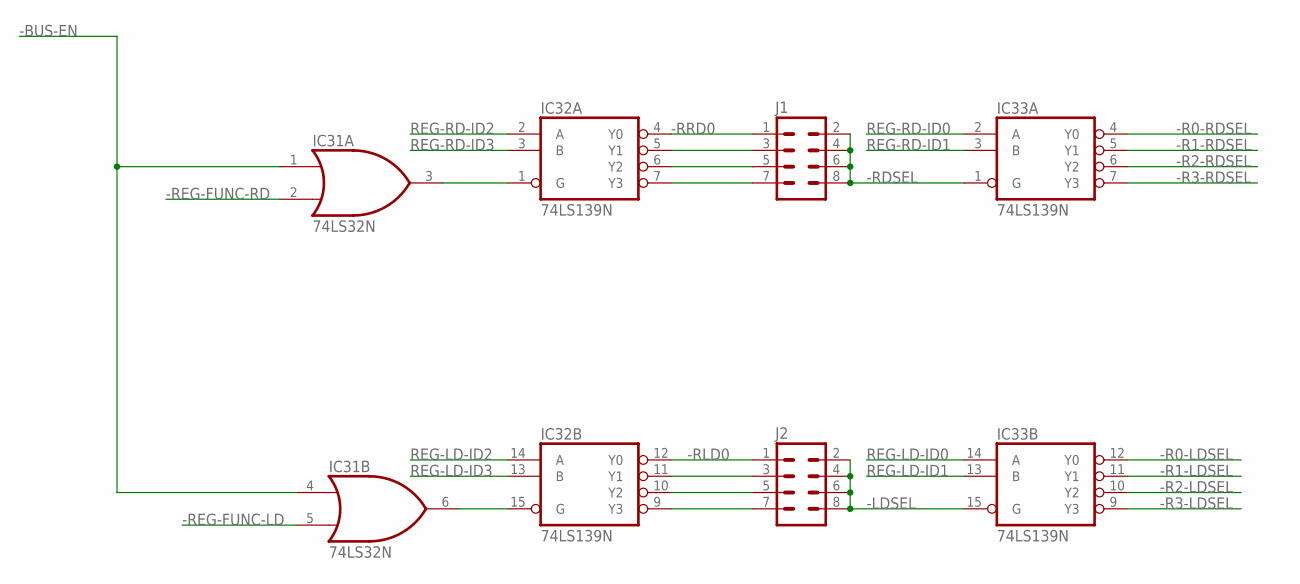
[picture p118: schematic Index Registers - 1.0.sch, sheet 7, Select Logic]

Parts:
IC31: 74LS32N; DIL14
IC32, IC33: 74LS139N; DIL16
J1, J2: M04X2; 2X4

Connections:
-BUS-EN: IC31.1 (I0), IC31.4 (I0); also elsewhere on the board
-LDSEL: IC33.15 (G), J2.2, J2.4, J2.6, J2.8; also elsewhere on the board
-R0-LDSEL: IC33.12 (Y0); also elsewhere on the board
-R0-RDSEL: IC33.4 (Y0); also elsewhere on the board
-R1-LDSEL: IC33.11 (Y1); also elsewhere on the board
-R1-RDSEL: IC33.5 (Y1); also elsewhere on the board
-R2-LDSEL: IC33.10 (Y2); also elsewhere on the board
-R2-RDSEL: IC33.6 (Y2); also elsewhere on the board
-R3-LDSEL: IC33.9 (Y3); also elsewhere on the board
-R3-RDSEL: IC33.7 (Y3); also elsewhere on the board
-RDSEL: IC33.1 (G), J1.2, J1.4, J1.6, J1.8; also elsewhere on the board
-REG-FUNC-LD: IC31.5 (I1); also elsewhere on the board
-REG-FUNC-RD: IC31.2 (I1); also elsewhere on the board
-RLD0: IC32.12 (Y0), J2.1
-RRD0: IC32.4 (Y0), J1.1
GND: IC31.7 (GND), IC32.8 (GND), IC33.8 (GND); also elsewhere on the board
unnamed: IC31.3 (O), IC32.1 (G)
unnamed: IC31.6 (O), IC32.15 (G)
unnamed: IC32.5 (Y1), J1.3
unnamed: IC32.6 (Y2), J1.5
unnamed: IC32.7 (Y3), J1.7
unnamed: IC32.11 (Y1), J2.3
unnamed: IC32.10 (Y2), J2.5
unnamed: IC32.9 (Y3), J2.7
REG-LD-ID0: IC33.14 (A); also elsewhere on the board
REG-LD-ID1: IC33.13 (B); also elsewhere on the board
REG-LD-ID2: IC32.14 (A); also elsewhere on the board
REG-LD-ID3: IC32.13 (B); also elsewhere on the board
REG-RD-ID0: IC33.2 (A); also elsewhere on the board
REG-RD-ID1: IC33.3 (B); also elsewhere on the board
REG-RD-ID2: IC32.2 (A); also elsewhere on the board
REG-RD-ID3: IC32.3 (B); also elsewhere on the board
VCC: IC31.14 (VCC), IC32.16 (VCC), IC33.16 (VCC); also elsewhere on the board

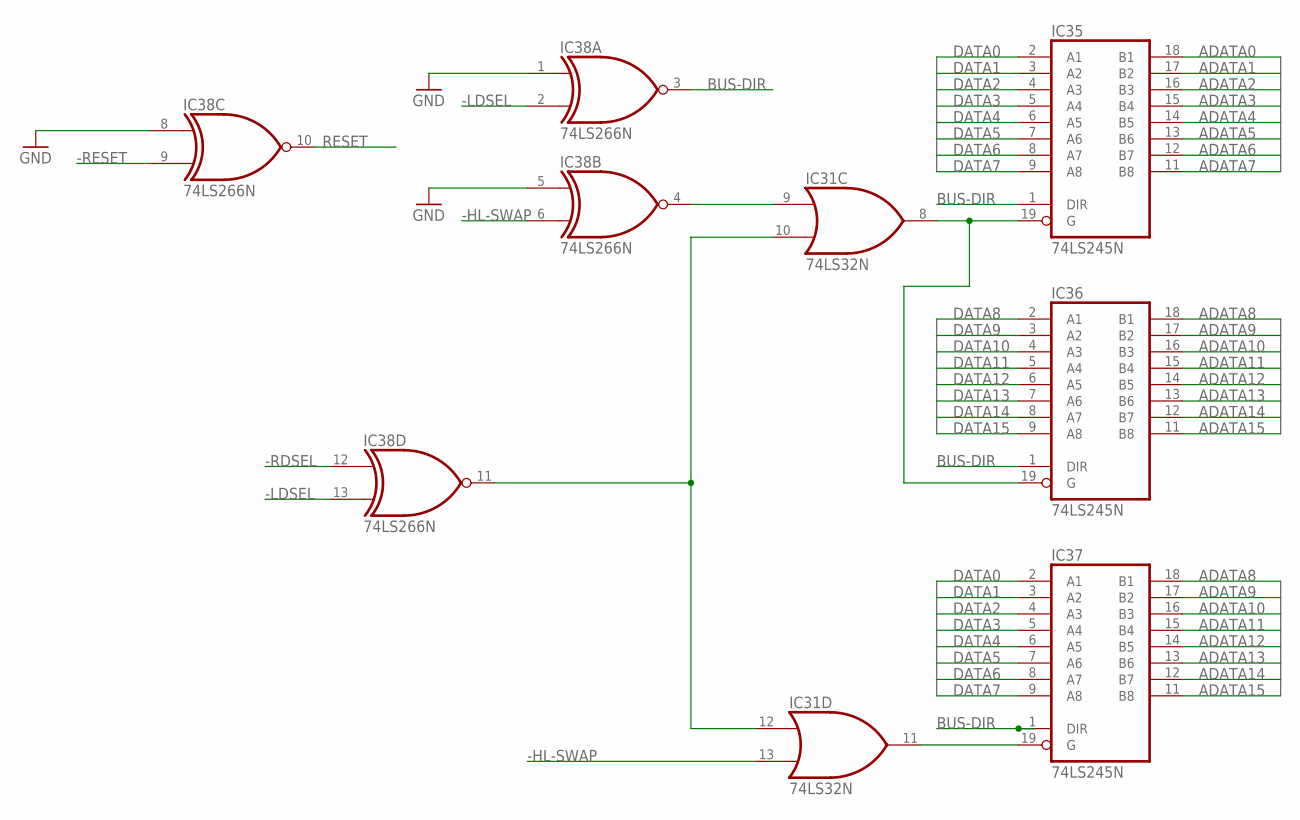
[picture p119: schematic Index Registers - 1.0.sch, sheet 8, bus buffering]

Parts:
IC31: 74LS32N; DIL14
IC35, IC36, IC37: 74LS245N; DIL20
IC38: 74LS266N; DIL14

Connections:
-HL-SWAP: IC31.13 (I1), IC38.6 (I1); also elsewhere on the board
-LDSEL: IC38.2 (I1), IC38.13 (I1); also elsewhere on the board
-RDSEL: IC38.12 (I0); also elsewhere on the board
-RESET: IC38.9 (I1); also elsewhere on the board
ADATA0: IC35.18 (B1); also elsewhere on the board
ADATA1: IC35.17 (B2); also elsewhere on the board
ADATA2: IC35.16 (B3); also elsewhere on the board
ADATA3: IC35.15 (B4); also elsewhere on the board
ADATA4: IC35.14 (B5); also elsewhere on the board
ADATA5: IC35.13 (B6); also elsewhere on the board
ADATA6: IC35.12 (B7); also elsewhere on the board
ADATA7: IC35.11 (B8); also elsewhere on the board
ADATA8: IC36.18 (B1), IC37.18 (B1); also elsewhere on the board
ADATA9: IC36.17 (B2), IC37.17 (B2); also elsewhere on the board
ADATA10: IC36.16 (B3), IC37.16 (B3); also elsewhere on the board
ADATA11: IC36.15 (B4), IC37.15 (B4); also elsewhere on the board
ADATA12: IC36.14 (B5), IC37.14 (B5); also elsewhere on the board
ADATA13: IC36.13 (B6), IC37.13 (B6); also elsewhere on the board
ADATA14: IC36.12 (B7), IC37.12 (B7); also elsewhere on the board
ADATA15: IC36.11 (B8), IC37.11 (B8); also elsewhere on the board
BUS-DIR: IC35.1 (DIR), IC36.1 (DIR), IC37.1 (DIR), IC38.3 (O)
DATA0: IC35.2 (A1), IC37.2 (A1); also elsewhere on the board
DATA1: IC35.3 (A2), IC37.3 (A2); also elsewhere on the board
DATA2: IC35.4 (A3), IC37.4 (A3); also elsewhere on the board
DATA3: IC35.5 (A4), IC37.5 (A4); also elsewhere on the board
DATA4: IC35.6 (A5), IC37.6 (A5); also elsewhere on the board
DATA5: IC35.7 (A6), IC37.7 (A6); also elsewhere on the board
DATA6: IC35.8 (A7), IC37.8 (A7); also elsewhere on the board
DATA7: IC35.9 (A8), IC37.9 (A8); also elsewhere on the board
DATA8: IC36.2 (A1); also elsewhere on the board
DATA9: IC36.3 (A2); also elsewhere on the board
DATA10: IC36.4 (A3); also elsewhere on the board
DATA11: IC36.5 (A4); also elsewhere on the board
DATA12: IC36.6 (A5); also elsewhere on the board
DATA13: IC36.7 (A6); also elsewhere on the board
DATA14: IC36.8 (A7); also elsewhere on the board
DATA15: IC36.9 (A8); also elsewhere on the board
GND: IC31.7 (GND), IC35.10 (GND), IC36.10 (GND), IC37.10 (GND), IC38.1 (I0), IC38.5 (I0), IC38.7 (GND), IC38.8 (I0); also elsewhere on the board
unnamed: IC31.8 (O), IC35.19 (G), IC36.19 (G)
unnamed: IC31.11 (O), IC37.19 (G)
unnamed: IC31.9 (I0), IC38.4 (O)
unnamed: IC31.10 (I1), IC31.12 (I0), IC38.11 (O)
RESET: IC38.10 (O); also elsewhere on the board
VCC: IC31.14 (VCC), IC35.20 (VCC), IC36.20 (VCC), IC37.20 (VCC), IC38.14 (VCC); also elsewhere on the board

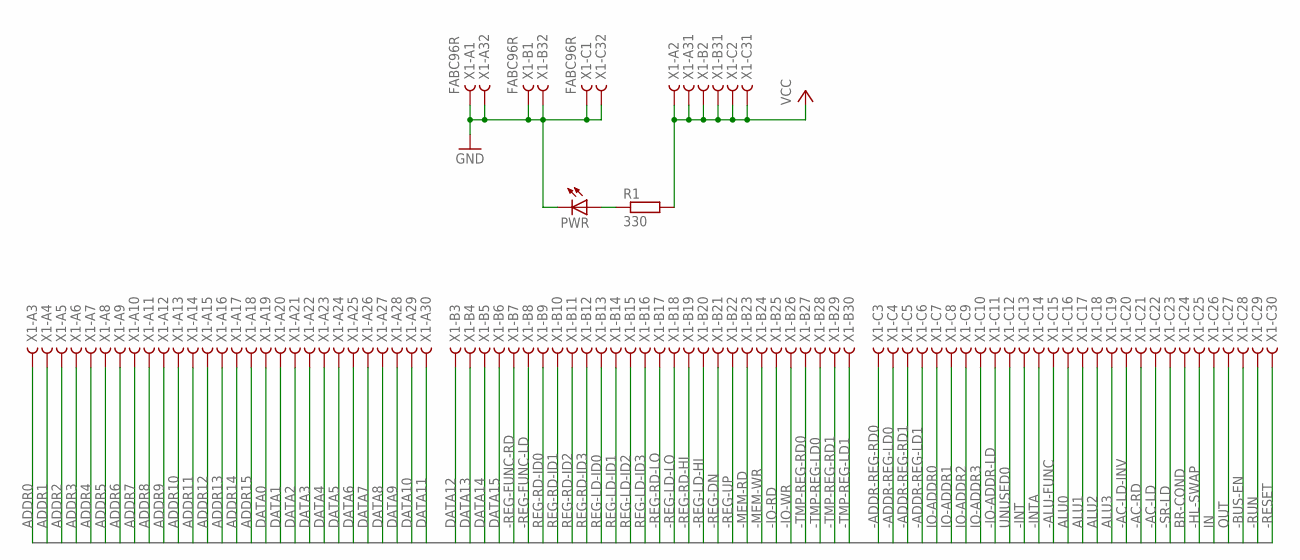
[picture p120: schematic Index Registers - 1.0.sch, sheet 9, BUS]

Parts:
PWR: LED5MM
R1: 330; 0207/10
X1: FABC96R

Connections:
-AC-LD: X1.C22
-AC-LD-INV: X1.C20
-AC-RD: X1.C21
-ADDR-REG-LD0: X1.C4
-ADDR-REG-LD1: X1.C6
-ADDR-REG-RD0: X1.C3
-ADDR-REG-RD1: X1.C5
-ALU-FUNC: X1.C15
-BUS-EN: X1.C28; also elsewhere on the board
-HL-SWAP: X1.C25; also elsewhere on the board
-INT: X1.C13
-INTA: X1.C14
-IO-ADDR-LD: X1.C11
-IO-RD: X1.B25
-IO-WR: X1.B26
-MEM-RD: X1.B23
-MEM-WR: X1.B24
-REG-DN: X1.B21; also elsewhere on the board
-REG-FUNC-LD: X1.B8; also elsewhere on the board
-REG-FUNC-RD: X1.B7; also elsewhere on the board
-REG-LD-HI: X1.B20; also elsewhere on the board
-REG-LD-LO: X1.B18; also elsewhere on the board
-REG-RD-HI: X1.B19; also elsewhere on the board
-REG-RD-LO: X1.B17; also elsewhere on the board
-REG-UP: X1.B22; also elsewhere on the board
-RESET: X1.C30; also elsewhere on the board
-RUN: X1.C29
-SR-LD: X1.C23
-TMP-REG-LD0: X1.B28
-TMP-REG-LD1: X1.B30
-TMP-REG-RD0: X1.B27
-TMP-REG-RD1: X1.B29
ADDR0: X1.A3
ADDR1: X1.A4
ADDR2: X1.A5
ADDR3: X1.A6
ADDR4: X1.A7
ADDR5: X1.A8
ADDR6: X1.A9
ADDR7: X1.A10
ADDR8: X1.A11
ADDR9: X1.A12
ADDR10: X1.A13
ADDR11: X1.A14
ADDR12: X1.A15
ADDR13: X1.A16
ADDR14: X1.A17
ADDR15: X1.A18
ALU0: X1.C16
ALU1: X1.C17
ALU2: X1.C18
ALU3: X1.C19
BR-COND: X1.C24
DATA0: X1.A19; also elsewhere on the board
DATA1: X1.A20; also elsewhere on the board
DATA2: X1.A21; also elsewhere on the board
DATA3: X1.A22; also elsewhere on the board
DATA4: X1.A23; also elsewhere on the board
DATA5: X1.A24; also elsewhere on the board
DATA6: X1.A25; also elsewhere on the board
DATA7: X1.A26; also elsewhere on the board
DATA8: X1.A27; also elsewhere on the board
DATA9: X1.A28; also elsewhere on the board
DATA10: X1.A29; also elsewhere on the board
DATA11: X1.A30; also elsewhere on the board
DATA12: X1.B3; also elsewhere on the board
DATA13: X1.B4; also elsewhere on the board
DATA14: X1.B5; also elsewhere on the board
DATA15: X1.B6; also elsewhere on the board
GND: PWR.K (C), X1.A1, X1.A32, X1.B1, X1.B32, X1.C1, X1.C32; also elsewhere on the board
IN: X1.C26
IO-ADDR0: X1.C7
IO-ADDR1: X1.C8
IO-ADDR2: X1.C9
IO-ADDR3: X1.C10
unnamed: PWR.A, R1.1
OUT: X1.C27
REG-LD-ID0: X1.B13; also elsewhere on the board
REG-LD-ID1: X1.B14; also elsewhere on the board
REG-LD-ID2: X1.B15; also elsewhere on the board
REG-LD-ID3: X1.B16; also elsewhere on the board
REG-RD-ID0: X1.B9; also elsewhere on the board
REG-RD-ID1: X1.B10; also elsewhere on the board
REG-RD-ID2: X1.B11; also elsewhere on the board
REG-RD-ID3: X1.B12; also elsewhere on the board
UNUSED0: X1.C12
VCC: R1.2, X1.A2, X1.A31, X1.B2, X1.B31, X1.C2, X1.C31; also elsewhere on the board

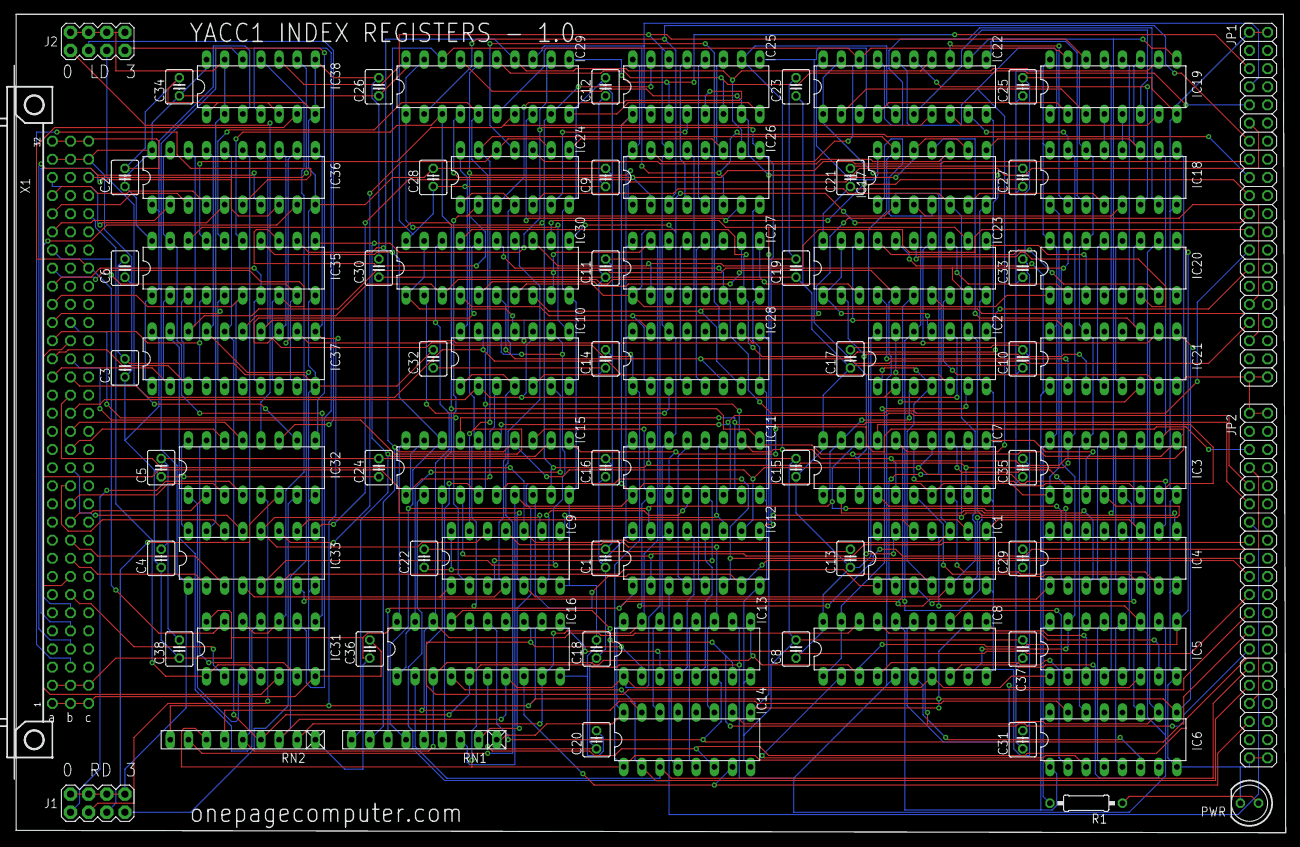
[picture p121: board Index Registers - 1.0.brd from above]

Board: 2 copper layers, 177.8 x 114.6 mm, 83 parts (0 on the bottom side), 192 nets.
