ksr/YACC1-2020/PCB/Production/Bus Tester orig/tester.brd

## EAGLE design PCB/Production/Bus Tester orig/tester.brd (2020-08-23)

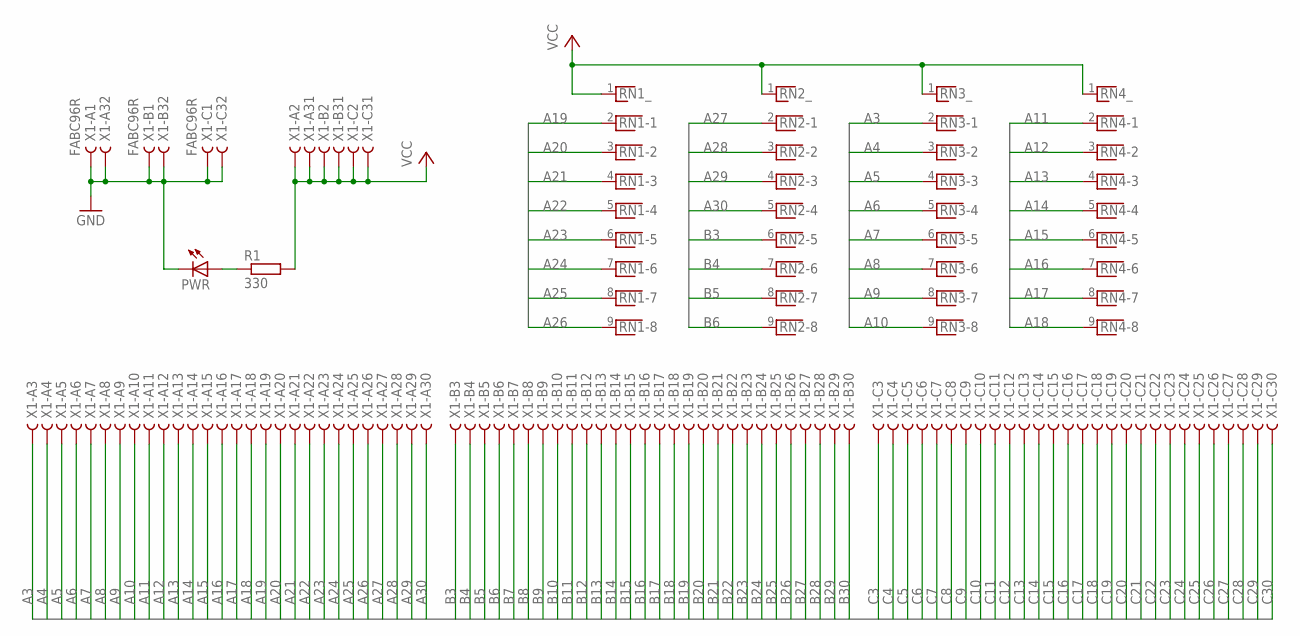
[picture p122: schematic tester.sch, sheet 1, BUS]

Parts:
PWR: LED5MM
R1: 330; 0207/10
RN1, RN2, RN3, RN4: RNX8; RN-9
X1: FABC96R

Connections:
A3: RN3.2, X1.A3; also elsewhere on the board
A4: RN3.3, X1.A4; also elsewhere on the board
A5: RN3.4, X1.A5; also elsewhere on the board
A6: RN3.5, X1.A6; also elsewhere on the board
A7: RN3.6, X1.A7; also elsewhere on the board
A8: RN3.7, X1.A8; also elsewhere on the board
A9: RN3.8, X1.A9; also elsewhere on the board
A10: RN3.9, X1.A10; also elsewhere on the board
A11: RN4.2, X1.A11; also elsewhere on the board
A12: RN4.3, X1.A12; also elsewhere on the board
A13: RN4.4, X1.A13; also elsewhere on the board
A14: RN4.5, X1.A14; also elsewhere on the board
A15: RN4.6, X1.A15; also elsewhere on the board
A16: RN4.7, X1.A16; also elsewhere on the board
A17: RN4.8, X1.A17; also elsewhere on the board
A18: RN4.9, X1.A18; also elsewhere on the board
A19: RN1.2, X1.A19; also elsewhere on the board
A20: RN1.3, X1.A20; also elsewhere on the board
A21: RN1.4, X1.A21; also elsewhere on the board
A22: RN1.5, X1.A22; also elsewhere on the board
A23: RN1.6, X1.A23; also elsewhere on the board
A24: RN1.7, X1.A24; also elsewhere on the board
A25: RN1.8, X1.A25; also elsewhere on the board
A26: RN1.9, X1.A26; also elsewhere on the board
A27: RN2.2, X1.A27; also elsewhere on the board
A28: RN2.3, X1.A28; also elsewhere on the board
A29: RN2.4, X1.A29; also elsewhere on the board
A30: RN2.5, X1.A30; also elsewhere on the board
B3: RN2.6, X1.B3; also elsewhere on the board
B4: RN2.7, X1.B4; also elsewhere on the board
B5: RN2.8, X1.B5; also elsewhere on the board
B6: RN2.9, X1.B6; also elsewhere on the board
B7: X1.B7; also elsewhere on the board
B8: X1.B8; also elsewhere on the board
B9: X1.B9; also elsewhere on the board
B10: X1.B10; also elsewhere on the board
B11: X1.B11; also elsewhere on the board
B12: X1.B12; also elsewhere on the board
B13: X1.B13; also elsewhere on the board
B14: X1.B14; also elsewhere on the board
B15: X1.B15; also elsewhere on the board
B16: X1.B16; also elsewhere on the board
B17: X1.B17; also elsewhere on the board
B18: X1.B18; also elsewhere on the board
B19: X1.B19; also elsewhere on the board
B20: X1.B20; also elsewhere on the board
B21: X1.B21; also elsewhere on the board
B22: X1.B22; also elsewhere on the board
B23: X1.B23; also elsewhere on the board
B24: X1.B24; also elsewhere on the board
B25: X1.B25; also elsewhere on the board
B26: X1.B26; also elsewhere on the board
B27: X1.B27; also elsewhere on the board
B28: X1.B28; also elsewhere on the board
B29: X1.B29; also elsewhere on the board
B30: X1.B30; also elsewhere on the board
C3: X1.C3; also elsewhere on the board
C4: X1.C4; also elsewhere on the board
C5: X1.C5; also elsewhere on the board
C6: X1.C6; also elsewhere on the board
C7: X1.C7; also elsewhere on the board
C8: X1.C8; also elsewhere on the board
C9: X1.C9; also elsewhere on the board
C10: X1.C10; also elsewhere on the board
C11: X1.C11; also elsewhere on the board
C12: X1.C12; also elsewhere on the board
C13: X1.C13; also elsewhere on the board
C14: X1.C14; also elsewhere on the board
C15: X1.C15; also elsewhere on the board
C16: X1.C16; also elsewhere on the board
C17: X1.C17; also elsewhere on the board
C18: X1.C18; also elsewhere on the board
C19: X1.C19; also elsewhere on the board
C20: X1.C20; also elsewhere on the board
C21: X1.C21; also elsewhere on the board
C22: X1.C22; also elsewhere on the board
C23: X1.C23; also elsewhere on the board
C24: X1.C24; also elsewhere on the board
C25: X1.C25; also elsewhere on the board
C26: X1.C26; also elsewhere on the board
C27: X1.C27; also elsewhere on the board
C28: X1.C28; also elsewhere on the board
C29: X1.C29; also elsewhere on the board
C30: X1.C30; also elsewhere on the board
GND: PWR.K (C), X1.A1, X1.A32, X1.B1, X1.B32, X1.C1, X1.C32; also elsewhere on the board
unnamed: PWR.A, R1.1
VCC: R1.2, RN1.1, RN2.1, RN3.1, RN4.1, X1.A2, X1.A31, X1.B2, X1.B31, X1.C2, X1.C31; also elsewhere on the board

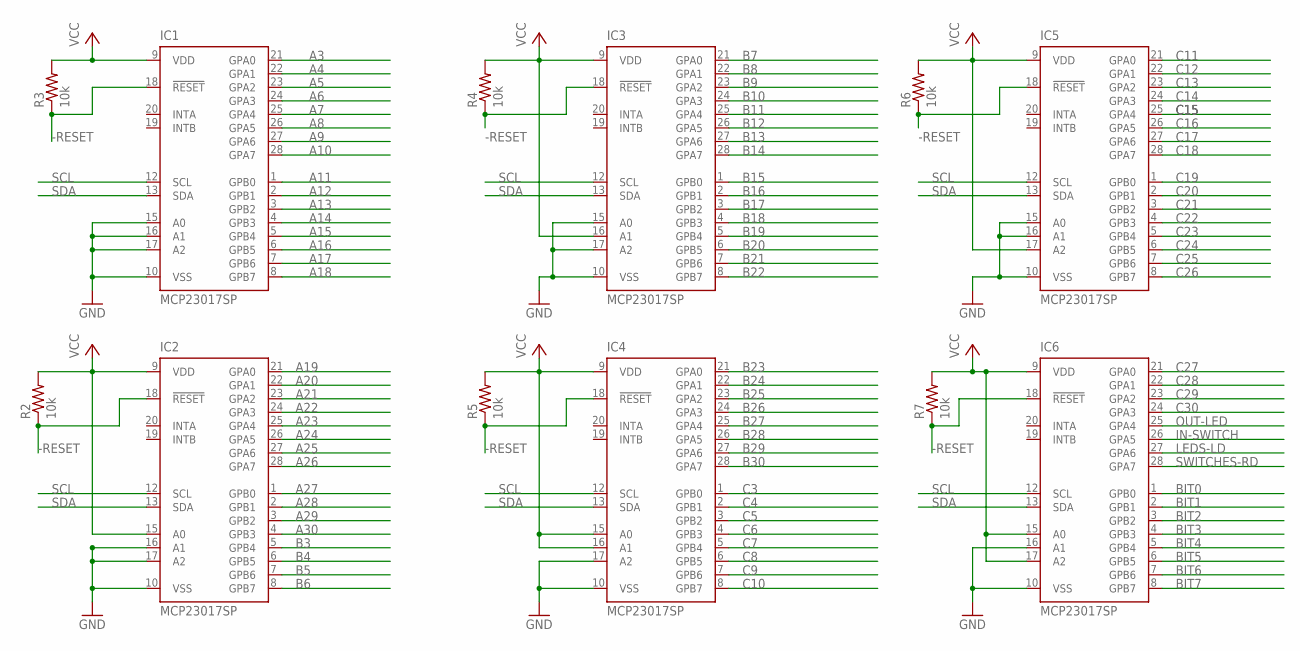
[picture p123: schematic tester.sch, sheet 2, bus cntl]

Parts:
IC1, IC2, IC3, IC4, IC5, IC6: MCP23017SP; DIL28-3
R2, R3, R4, R5, R6, R7: 10k; 0207/10

Connections:
-RESET: IC1.18 (!RESET), IC2.18 (!RESET), IC3.18 (!RESET), IC4.18 (!RESET), IC5.18 (!RESET), IC6.18 (!RESET), R2.1, R3.1, R4.1, R5.1, R6.1, R7.1; also elsewhere on the board
A3: IC1.21 (GPA0); also elsewhere on the board
A4: IC1.22 (GPA1); also elsewhere on the board
A5: IC1.23 (GPA2); also elsewhere on the board
A6: IC1.24 (GPA3); also elsewhere on the board
A7: IC1.25 (GPA4); also elsewhere on the board
A8: IC1.26 (GPA5); also elsewhere on the board
A9: IC1.27 (GPA6); also elsewhere on the board
A10: IC1.28 (GPA7); also elsewhere on the board
A11: IC1.1 (GPB0); also elsewhere on the board
A12: IC1.2 (GPB1); also elsewhere on the board
A13: IC1.3 (GPB2); also elsewhere on the board
A14: IC1.4 (GPB3); also elsewhere on the board
A15: IC1.5 (GPB4); also elsewhere on the board
A16: IC1.6 (GPB5); also elsewhere on the board
A17: IC1.7 (GPB6); also elsewhere on the board
A18: IC1.8 (GPB7); also elsewhere on the board
A19: IC2.21 (GPA0); also elsewhere on the board
A20: IC2.22 (GPA1); also elsewhere on the board
A21: IC2.23 (GPA2); also elsewhere on the board
A22: IC2.24 (GPA3); also elsewhere on the board
A23: IC2.25 (GPA4); also elsewhere on the board
A24: IC2.26 (GPA5); also elsewhere on the board
A25: IC2.27 (GPA6); also elsewhere on the board
A26: IC2.28 (GPA7); also elsewhere on the board
A27: IC2.1 (GPB0); also elsewhere on the board
A28: IC2.2 (GPB1); also elsewhere on the board
A29: IC2.3 (GPB2); also elsewhere on the board
A30: IC2.4 (GPB3); also elsewhere on the board
B3: IC2.5 (GPB4); also elsewhere on the board
B4: IC2.6 (GPB5); also elsewhere on the board
B5: IC2.7 (GPB6); also elsewhere on the board
B6: IC2.8 (GPB7); also elsewhere on the board
B7: IC3.21 (GPA0); also elsewhere on the board
B8: IC3.22 (GPA1); also elsewhere on the board
B9: IC3.23 (GPA2); also elsewhere on the board
B10: IC3.24 (GPA3); also elsewhere on the board
B11: IC3.25 (GPA4); also elsewhere on the board
B12: IC3.26 (GPA5); also elsewhere on the board
B13: IC3.27 (GPA6); also elsewhere on the board
B14: IC3.28 (GPA7); also elsewhere on the board
B15: IC3.1 (GPB0); also elsewhere on the board
B16: IC3.2 (GPB1); also elsewhere on the board
B17: IC3.3 (GPB2); also elsewhere on the board
B18: IC3.4 (GPB3); also elsewhere on the board
B19: IC3.5 (GPB4); also elsewhere on the board
B20: IC3.6 (GPB5); also elsewhere on the board
B21: IC3.7 (GPB6); also elsewhere on the board
B22: IC3.8 (GPB7); also elsewhere on the board
B23: IC4.21 (GPA0); also elsewhere on the board
B24: IC4.22 (GPA1); also elsewhere on the board
B25: IC4.23 (GPA2); also elsewhere on the board
B26: IC4.24 (GPA3); also elsewhere on the board
B27: IC4.25 (GPA4); also elsewhere on the board
B28: IC4.26 (GPA5); also elsewhere on the board
B29: IC4.27 (GPA6); also elsewhere on the board
B30: IC4.28 (GPA7); also elsewhere on the board
BIT0: IC6.1 (GPB0); also elsewhere on the board
BIT1: IC6.2 (GPB1); also elsewhere on the board
BIT2: IC6.3 (GPB2); also elsewhere on the board
BIT3: IC6.4 (GPB3); also elsewhere on the board
BIT4: IC6.5 (GPB4); also elsewhere on the board
BIT5: IC6.6 (GPB5); also elsewhere on the board
BIT6: IC6.7 (GPB6); also elsewhere on the board
BIT7: IC6.8 (GPB7); also elsewhere on the board
C3: IC4.1 (GPB0); also elsewhere on the board
C4: IC4.2 (GPB1); also elsewhere on the board
C5: IC4.3 (GPB2); also elsewhere on the board
C6: IC4.4 (GPB3); also elsewhere on the board
C7: IC4.5 (GPB4); also elsewhere on the board
C8: IC4.6 (GPB5); also elsewhere on the board
C9: IC4.7 (GPB6); also elsewhere on the board
C10: IC4.8 (GPB7); also elsewhere on the board
C11: IC5.21 (GPA0); also elsewhere on the board
C12: IC5.22 (GPA1); also elsewhere on the board
C13: IC5.23 (GPA2); also elsewhere on the board
C14: IC5.24 (GPA3); also elsewhere on the board
C15: IC5.25 (GPA4); also elsewhere on the board
C16: IC5.26 (GPA5); also elsewhere on the board
C17: IC5.27 (GPA6); also elsewhere on the board
C18: IC5.28 (GPA7); also elsewhere on the board
C19: IC5.1 (GPB0); also elsewhere on the board
C20: IC5.2 (GPB1); also elsewhere on the board
C21: IC5.3 (GPB2); also elsewhere on the board
C22: IC5.4 (GPB3); also elsewhere on the board
C23: IC5.5 (GPB4); also elsewhere on the board
C24: IC5.6 (GPB5); also elsewhere on the board
C25: IC5.7 (GPB6); also elsewhere on the board
C26: IC5.8 (GPB7); also elsewhere on the board
C27: IC6.21 (GPA0); also elsewhere on the board
C28: IC6.22 (GPA1); also elsewhere on the board
C29: IC6.23 (GPA2); also elsewhere on the board
C30: IC6.24 (GPA3); also elsewhere on the board
GND: IC1.10 (VSS), IC1.15 (A0), IC1.16 (A1), IC1.17 (A2), IC2.10 (VSS), IC2.16 (A1), IC2.17 (A2), IC3.10 (VSS), IC3.15 (A0), IC3.17 (A2), IC4.10 (VSS), IC4.17 (A2), IC5.10 (VSS), IC5.15 (A0), IC5.16 (A1), IC6.10 (VSS), IC6.16 (A1); also elsewhere on the board
IN-SWITCH: IC6.26 (GPA5); also elsewhere on the board
LEDS-LD: IC6.27 (GPA6); also elsewhere on the board
OUT-LED: IC6.25 (GPA4); also elsewhere on the board
SCL: IC1.12 (SCL), IC2.12 (SCL), IC3.12 (SCL), IC4.12 (SCL), IC5.12 (SCL), IC6.12 (SCL); also elsewhere on the board
SDA: IC1.13 (SDA), IC2.13 (SDA), IC3.13 (SDA), IC4.13 (SDA), IC5.13 (SDA), IC6.13 (SDA); also elsewhere on the board
SWITCHES-RD: IC6.28 (GPA7); also elsewhere on the board
VCC: IC1.9 (VDD), IC2.9 (VDD), IC2.15 (A0), IC3.9 (VDD), IC3.16 (A1), IC4.9 (VDD), IC4.15 (A0), IC4.16 (A1), IC5.9 (VDD), IC5.17 (A2), IC6.9 (VDD), IC6.15 (A0), IC6.17 (A2), R2.2, R3.2, R4.2, R5.2, R6.2, R7.2; also elsewhere on the board

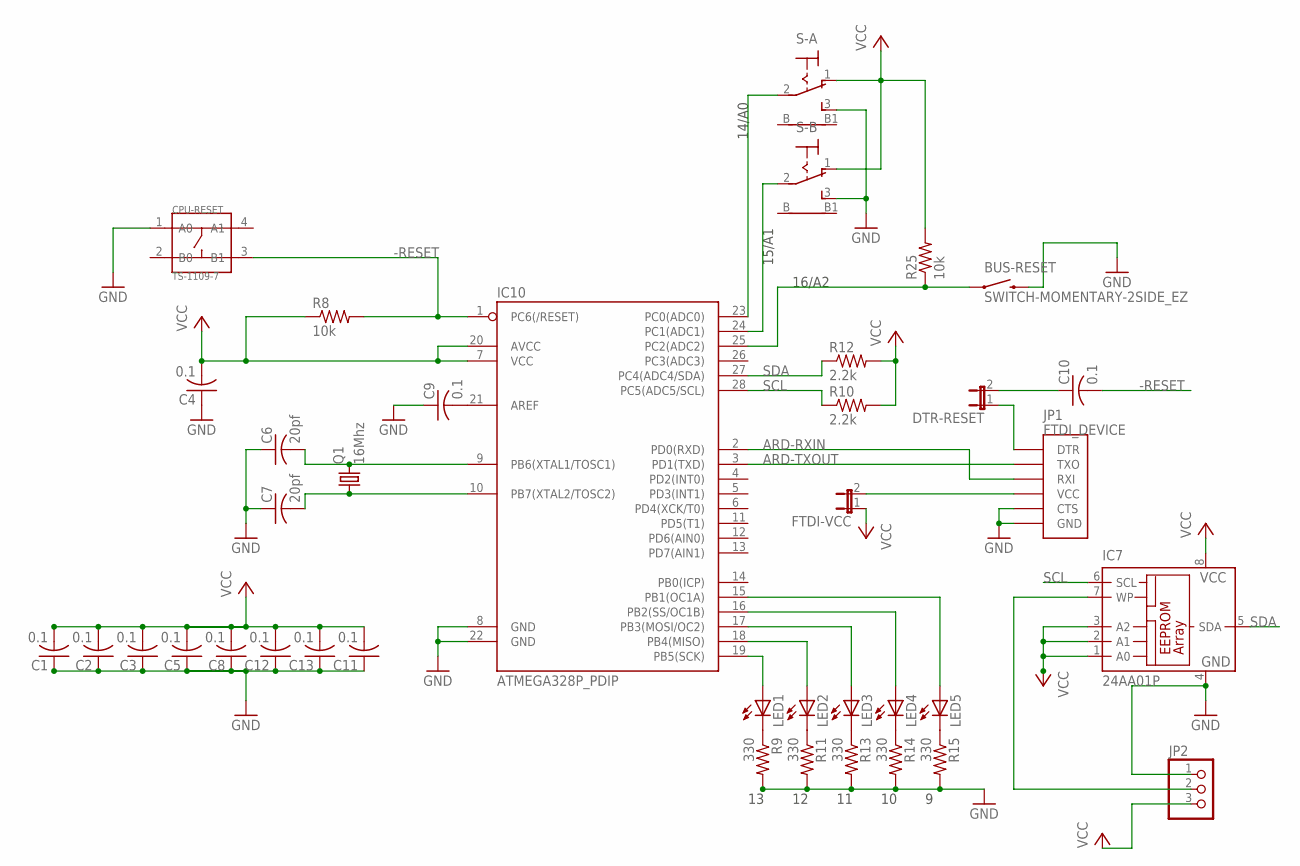
[picture p124: schematic tester.sch, sheet 3, CPU]

Parts:
BUS-RESET: SWITCH-MOMENTARY-2SIDE_EZ; TACTILE-PTH-SIDEEZ
C1, C2, C3, C4, C5, C8, C9, C10, C11, C12, C13: 0.1; C025-024X044
C6, C7: 20pf; C025-024X044
CPU-RESET: TS-1109-7; SW4-6.2X6.2X5.0MM
DTR-RESET: JP1E; JP1
FTDI-VCC: JP1E; JP1
IC7: 24AA01P; DIL8
IC10: ATMEGA328P_PDIP; DIL28-3
JP1: FTDI_DEVICE; FTDI_DEVICE_SIDE
JP2: PINHD-1X3; 1X03
LED1, LED2, LED3, LED4, LED5: LED5MM
Q1: 16Mhz; HC49/S
R8, R25: 10k; 0207/10
R9, R11, R13, R14, R15: 330; 0207/10
R10, R12: 2.2k; 0207/10
S-A: 9070-1W
S-B: 9070-1W

Connections:
-RESET: C10.2, CPU-RESET.3 (B1), IC10.1 (PC6(/RESET)), R8.2; also elsewhere on the board
ARD-RXIN: IC10.2 (PD0(RXD)), JP1.P$3 (RXI)
ARD-TXOUT: IC10.3 (PD1(TXD)), JP1.P$2 (TXO)
GND: BUS-RESET.2, C1.1, C2.1, C3.1, C4.1, C5.1, C6.1, C7.1, C8.1, C9.1, C11.1, C12.1, C13.1, CPU-RESET.1 (A0), IC7.4 (GND), IC10.8 (GND), IC10.22 (GND), JP1.P$5 (CTS), JP1.P$6 (GND), JP2.1, R9.2, R11.2, R13.2, R14.2, R15.2, S-A.3 (S), S-B.3 (S); also elsewhere on the board
unnamed: IC10.19 (PB5(SCK)), LED1.A
unnamed: IC7.7 (WP), JP2.2
unnamed: C6.2, IC10.9 (PB6(XTAL1/TOSC1)), Q1.2
unnamed: C7.2, IC10.10 (PB7(XTAL2/TOSC2)), Q1.1
unnamed: IC10.18 (PB4(MISO)), LED2.A
unnamed: IC10.17 (PB3(MOSI/OC2)), LED3.A
unnamed: IC10.16 (PB2(SS/OC1B)), LED4.A
unnamed: C10.1, DTR-RESET.2
unnamed: IC10.15 (PB1(OC1A)), LED5.A
unnamed: LED2.K (C), R11.1
unnamed: LED1.K (C), R9.1
unnamed: LED3.K (C), R13.1
unnamed: C9.2, IC10.21 (AREF)
unnamed: LED4.K (C), R14.1
unnamed: LED5.K (C), R15.1
unnamed: IC10.23 (PC0(ADC0)), S-A.2
unnamed: IC10.24 (PC1(ADC1)), S-B.2
unnamed: DTR-RESET.1, JP1.P$1 (DTR)
unnamed: FTDI-VCC.2, JP1.P$4 (VCC)
unnamed: BUS-RESET.1, IC10.25 (PC2(ADC2)), R25.1
SCL: IC7.6 (SCL), IC10.28 (PC5(ADC5/SCL)), R10.1; also elsewhere on the board
SDA: IC7.5 (SDA), IC10.27 (PC4(ADC4/SDA)), R12.1; also elsewhere on the board
VCC: C1.2, C2.2, C3.2, C4.2, C5.2, C8.2, C11.2, C12.2, C13.2, FTDI-VCC.1, IC7.1 (A0), IC7.2 (A1), IC7.3 (A2), IC7.8 (VCC), IC10.7 (VCC), IC10.20 (AVCC), JP2.3, R8.1, R10.2, R12.2, R25.2, S-A.1 (O), S-B.1 (O); also elsewhere on the board

Notes on the sheet:
14/A0
15/A1
16/A2

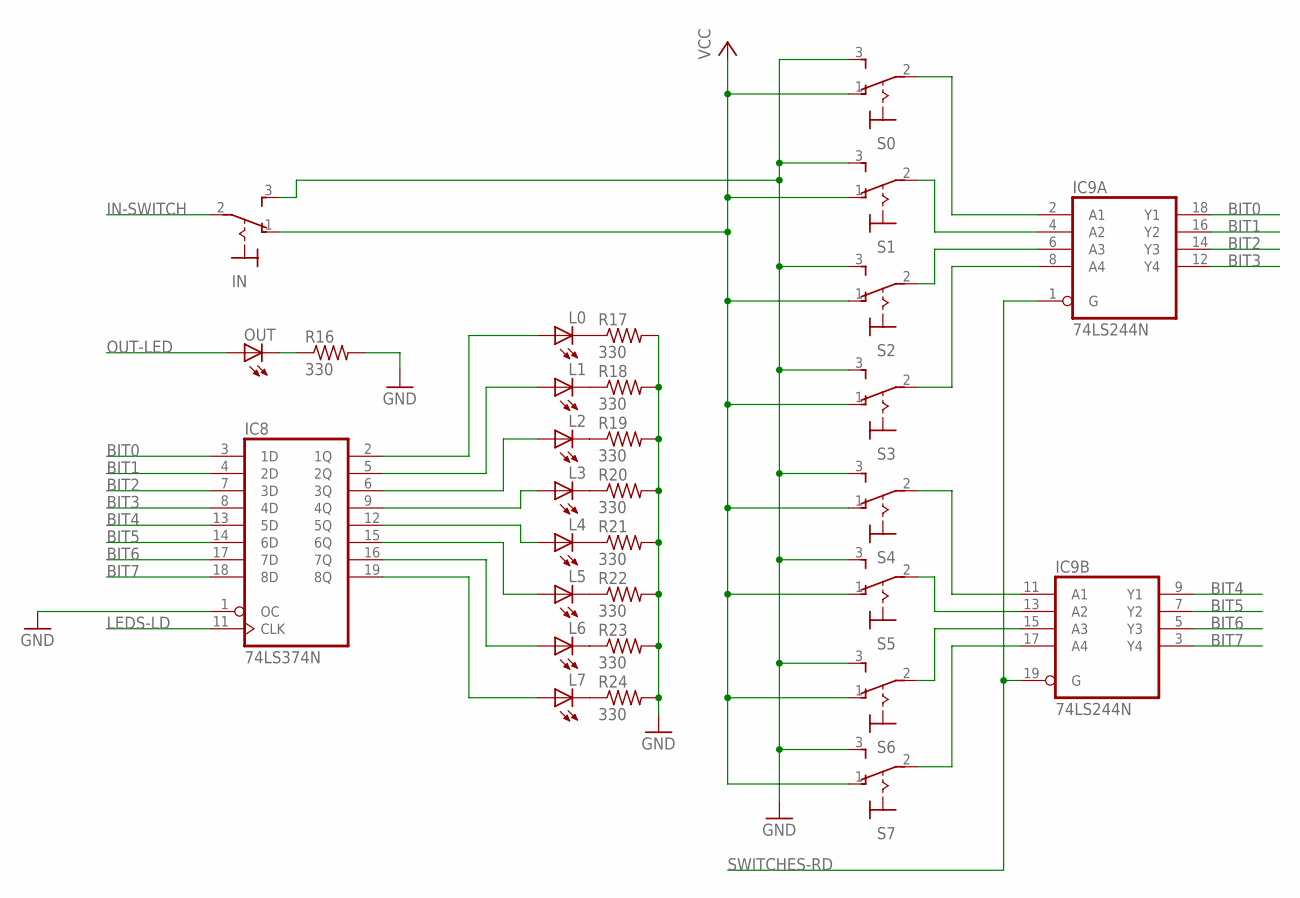
[picture p125: schematic tester.sch, sheet 4, I/O]

Parts:
IC8: 74LS374N; DIL20
IC9: 74LS244N; DIL20
IN: M9040P
L0, L1, L2, L3, L4, L5, L6, L7: LED5MM
OUT: LED5MM
R16, R17, R18, R19, R20, R21, R22, R23, R24: 330; 0207/10
S0, S1, S2, S3, S4, S5, S6, S7: M9040P

Connections:
BIT0: IC8.3 (1D), IC9.18 (Y1); also elsewhere on the board
BIT1: IC8.4 (2D), IC9.16 (Y2); also elsewhere on the board
BIT2: IC8.7 (3D), IC9.14 (Y3); also elsewhere on the board
BIT3: IC8.8 (4D), IC9.12 (Y4); also elsewhere on the board
BIT4: IC8.13 (5D), IC9.9 (Y1); also elsewhere on the board
BIT5: IC8.14 (6D), IC9.7 (Y2); also elsewhere on the board
BIT6: IC8.17 (7D), IC9.5 (Y3); also elsewhere on the board
BIT7: IC8.18 (8D), IC9.3 (Y4); also elsewhere on the board
GND: IC8.1 (OC), IC8.10 (GND), IC9.10 (GND), IN.3 (S), R16.2, R17.2, R18.2, R19.2, R20.2, R21.2, R22.2, R23.2, R24.2, S0.3 (S), S1.3 (S), S2.3 (S), S3.3 (S), S4.3 (S), S5.3 (S), S6.3 (S), S7.3 (S); also elsewhere on the board
IN-SWITCH: IN.2; also elsewhere on the board
LEDS-LD: IC8.11 (CLK); also elsewhere on the board
unnamed: L7.K (C), R24.1
unnamed: L6.K (C), R23.1
unnamed: L5.K (C), R22.1
unnamed: L4.K (C), R21.1
unnamed: L3.K (C), R20.1
unnamed: L2.K (C), R19.1
unnamed: L1.K (C), R18.1
unnamed: L0.K (C), R17.1
unnamed: OUT.K (C), R16.1
unnamed: IC8.5 (2Q), L1.A
unnamed: IC8.9 (4Q), L3.A
unnamed: IC8.12 (5Q), L4.A
unnamed: IC8.15 (6Q), L5.A
unnamed: IC8.6 (3Q), L2.A
unnamed: IC8.16 (7Q), L6.A
unnamed: IC8.19 (8Q), L7.A
unnamed: IC8.2 (1Q), L0.A
unnamed: IC9.2 (A1), S0.2
unnamed: IC9.8 (A4), S3.2
unnamed: IC9.6 (A3), S2.2
unnamed: IC9.4 (A2), S1.2
unnamed: IC9.11 (A1), S4.2
unnamed: IC9.17 (A4), S7.2
unnamed: IC9.13 (A2), S5.2
unnamed: IC9.15 (A3), S6.2
OUT-LED: OUT.A; also elsewhere on the board
SWITCHES-RD: IC9.1 (G), IC9.19 (G); also elsewhere on the board
VCC: IC8.20 (VCC), IC9.20 (VCC), IN.1 (O), S0.1 (O), S1.1 (O), S2.1 (O), S3.1 (O), S4.1 (O), S5.1 (O), S6.1 (O), S7.1 (O); also elsewhere on the board
