ksr/YACC1-2020/PCB/Production/Bus Tester orig/tester.brd

## EAGLE design PCB/Production/Bus Tester orig/tester.brd (continued)

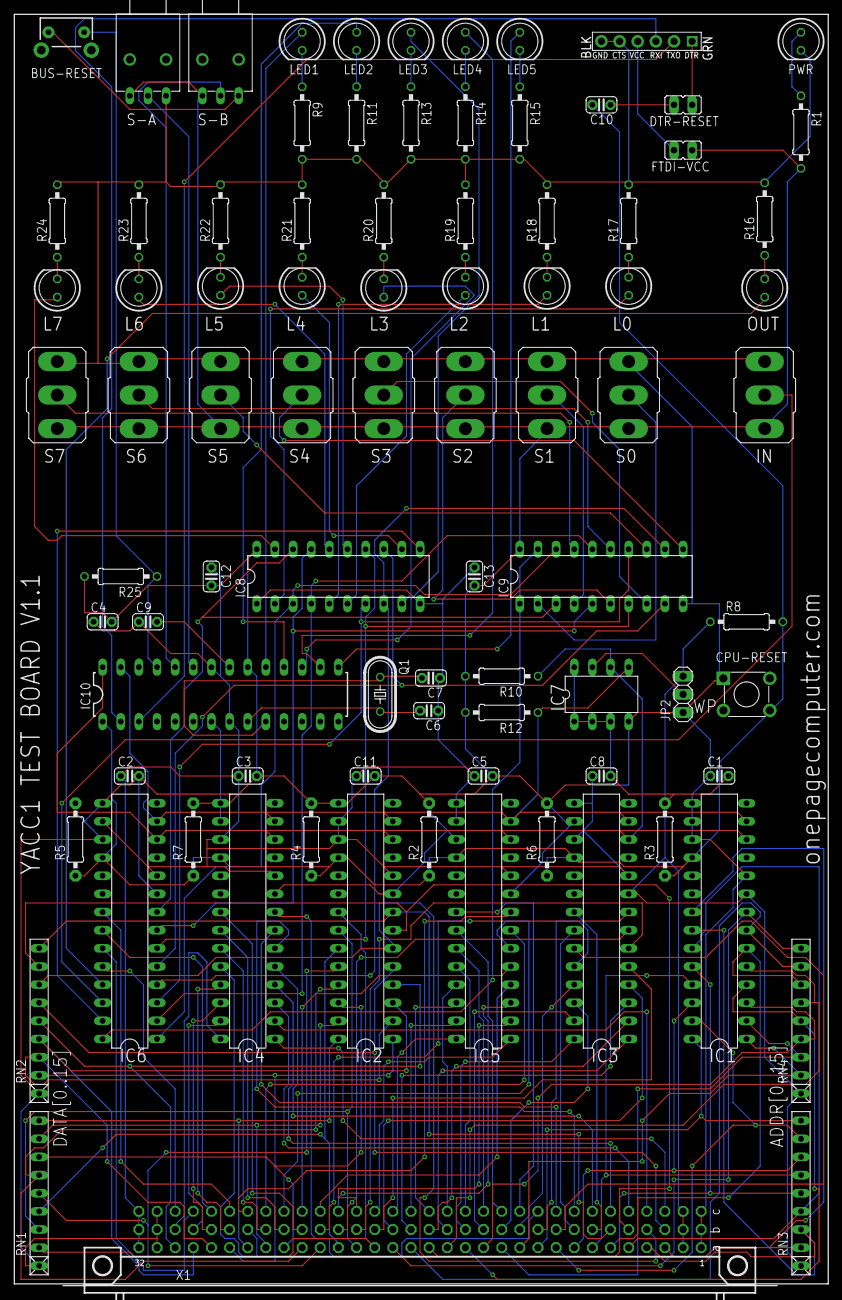
[picture p126: board tester.brd from above]

Board: 2 copper layers, 114.0 x 177.8 mm, 86 parts (0 on the bottom side), 149 nets.
