ksr/YACC1-2020/PCB/Production/Address and TMP-V1.0/Address and TMP V1.0.brd

## EAGLE design PCB/Working - Under Develolpment/Old and obsolete/Address and TMP-V1.0/Address and TMP V1.0.brd (2020-08-23, an earlier design)

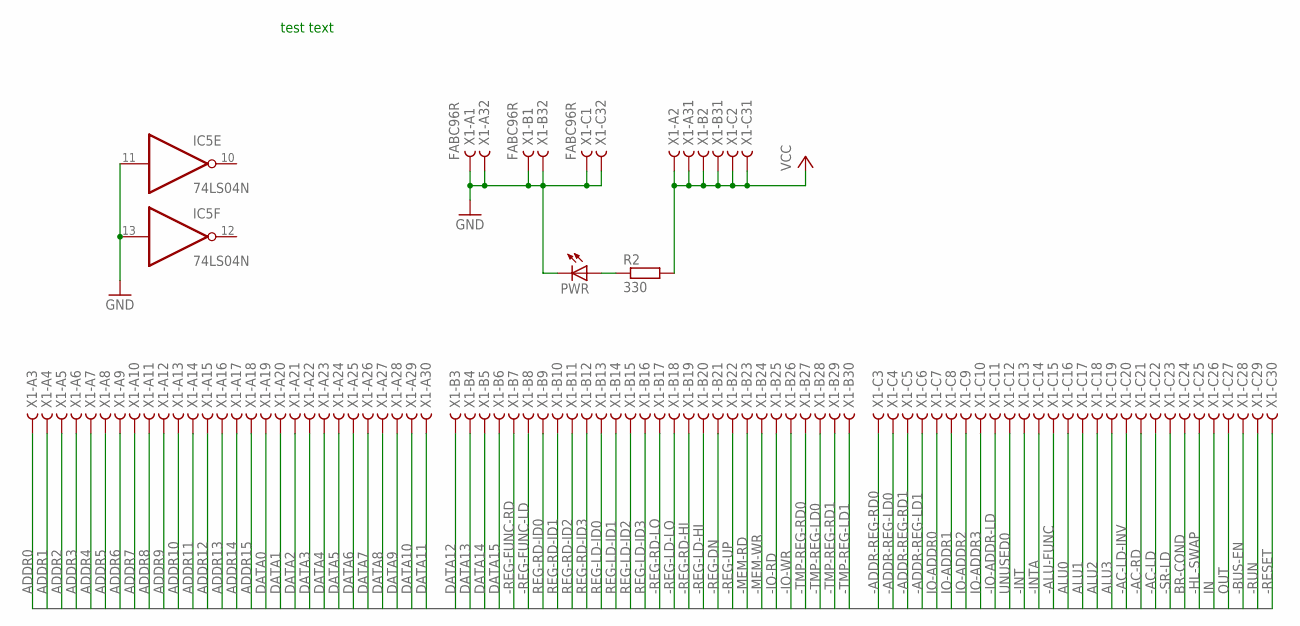
[picture p127: schematic Address and TMP V1.0.sch, sheet 1, BUS]

Parts:
IC5: 74LS04N; DIL14
PWR: LED5MM
R2: 330; 0207/10
X1: FABC96R

Connections:
-AC-LD: X1.C22
-AC-LD-INV: X1.C20
-AC-RD: X1.C21
-ADDR-REG-LD0: X1.C4; also elsewhere on the board
-ADDR-REG-LD1: X1.C6; also elsewhere on the board
-ADDR-REG-RD0: X1.C3; also elsewhere on the board
-ADDR-REG-RD1: X1.C5; also elsewhere on the board
-ALU-FUNC: X1.C15
-BUS-EN: X1.C28
-HL-SWAP: X1.C25
-INT: X1.C13
-INTA: X1.C14
-IO-ADDR-LD: X1.C11
-IO-RD: X1.B25
-IO-WR: X1.B26
-MEM-RD: X1.B23
-MEM-WR: X1.B24
-REG-DN: X1.B21
-REG-FUNC-LD: X1.B8
-REG-FUNC-RD: X1.B7
-REG-LD-HI: X1.B20
-REG-LD-LO: X1.B18
-REG-RD-HI: X1.B19
-REG-RD-LO: X1.B17
-REG-UP: X1.B22
-RESET: X1.C30
-RUN: X1.C29
-SR-LD: X1.C23
-TMP-REG-LD0: X1.B28; also elsewhere on the board
-TMP-REG-LD1: X1.B30; also elsewhere on the board
-TMP-REG-RD0: X1.B27; also elsewhere on the board
-TMP-REG-RD1: X1.B29; also elsewhere on the board
ADDR0: X1.A3; also elsewhere on the board
ADDR1: X1.A4; also elsewhere on the board
ADDR2: X1.A5; also elsewhere on the board
ADDR3: X1.A6; also elsewhere on the board
ADDR4: X1.A7; also elsewhere on the board
ADDR5: X1.A8; also elsewhere on the board
ADDR6: X1.A9; also elsewhere on the board
ADDR7: X1.A10; also elsewhere on the board
ADDR8: X1.A11; also elsewhere on the board
ADDR9: X1.A12; also elsewhere on the board
ADDR10: X1.A13; also elsewhere on the board
ADDR11: X1.A14; also elsewhere on the board
ADDR12: X1.A15; also elsewhere on the board
ADDR13: X1.A16; also elsewhere on the board
ADDR14: X1.A17; also elsewhere on the board
ADDR15: X1.A18; also elsewhere on the board
ALU0: X1.C16
ALU1: X1.C17
ALU2: X1.C18
ALU3: X1.C19
BR-COND: X1.C24
DATA0: X1.A19; also elsewhere on the board
DATA1: X1.A20; also elsewhere on the board
DATA2: X1.A21; also elsewhere on the board
DATA3: X1.A22; also elsewhere on the board
DATA4: X1.A23; also elsewhere on the board
DATA5: X1.A24; also elsewhere on the board
DATA6: X1.A25; also elsewhere on the board
DATA7: X1.A26; also elsewhere on the board
DATA8: X1.A27; also elsewhere on the board
DATA9: X1.A28; also elsewhere on the board
DATA10: X1.A29; also elsewhere on the board
DATA11: X1.A30; also elsewhere on the board
DATA12: X1.B3; also elsewhere on the board
DATA13: X1.B4; also elsewhere on the board
DATA14: X1.B5; also elsewhere on the board
DATA15: X1.B6; also elsewhere on the board
GND: IC5.7 (GND), IC5.11 (I), IC5.13 (I), PWR.K (C), X1.A1, X1.A32, X1.B1, X1.B32, X1.C1, X1.C32; also elsewhere on the board
IN: X1.C26
IO-ADDR0: X1.C7
IO-ADDR1: X1.C8
IO-ADDR2: X1.C9
IO-ADDR3: X1.C10
unnamed: PWR.A, R2.1
OUT: X1.C27
REG-LD-ID0: X1.B13
REG-LD-ID1: X1.B14
REG-LD-ID2: X1.B15
REG-LD-ID3: X1.B16
REG-RD-ID0: X1.B9
REG-RD-ID1: X1.B10
REG-RD-ID2: X1.B11
REG-RD-ID3: X1.B12
UNUSED0: X1.C12
VCC: IC5.14 (VCC), R2.2, X1.A2, X1.A31, X1.B2, X1.B31, X1.C2, X1.C31; also elsewhere on the board

Notes on the sheet:
test text

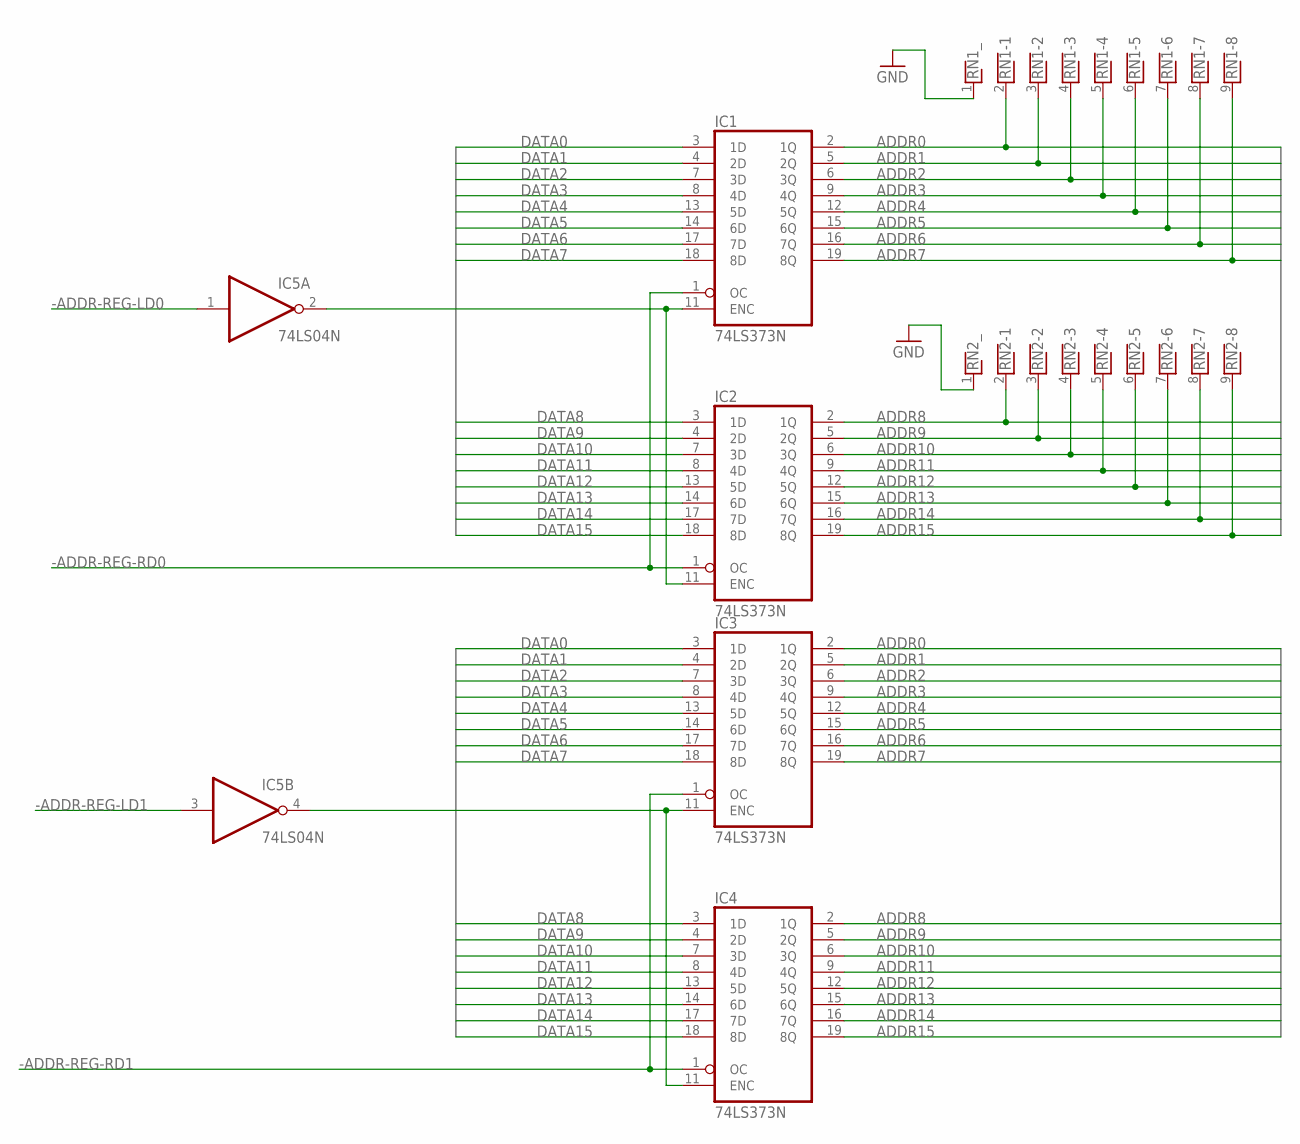
[picture p128: schematic Address and TMP V1.0.sch, sheet 2, address registers]

Parts:
IC1, IC2, IC3, IC4: 74LS373N; DIL20
IC5: 74LS04N; DIL14
RN1, RN2: RNX8; RN-9

Connections:
-ADDR-REG-LD0: IC5.1 (I); also elsewhere on the board
-ADDR-REG-LD1: IC5.3 (I); also elsewhere on the board
-ADDR-REG-RD0: IC1.1 (OC), IC2.1 (OC); also elsewhere on the board
-ADDR-REG-RD1: IC3.1 (OC), IC4.1 (OC); also elsewhere on the board
ADDR0: IC1.2 (1Q), IC3.2 (1Q), RN1.2; also elsewhere on the board
ADDR1: IC1.5 (2Q), IC3.5 (2Q), RN1.3; also elsewhere on the board
ADDR2: IC1.6 (3Q), IC3.6 (3Q), RN1.4; also elsewhere on the board
ADDR3: IC1.9 (4Q), IC3.9 (4Q), RN1.5; also elsewhere on the board
ADDR4: IC1.12 (5Q), IC3.12 (5Q), RN1.6; also elsewhere on the board
ADDR5: IC1.15 (6Q), IC3.15 (6Q), RN1.7; also elsewhere on the board
ADDR6: IC1.16 (7Q), IC3.16 (7Q), RN1.8; also elsewhere on the board
ADDR7: IC1.19 (8Q), IC3.19 (8Q), RN1.9; also elsewhere on the board
ADDR8: IC2.2 (1Q), IC4.2 (1Q), RN2.2; also elsewhere on the board
ADDR9: IC2.5 (2Q), IC4.5 (2Q), RN2.3; also elsewhere on the board
ADDR10: IC2.6 (3Q), IC4.6 (3Q), RN2.4; also elsewhere on the board
ADDR11: IC2.9 (4Q), IC4.9 (4Q), RN2.5; also elsewhere on the board
ADDR12: IC2.12 (5Q), IC4.12 (5Q), RN2.6; also elsewhere on the board
ADDR13: IC2.15 (6Q), IC4.15 (6Q), RN2.7; also elsewhere on the board
ADDR14: IC2.16 (7Q), IC4.16 (7Q), RN2.8; also elsewhere on the board
ADDR15: IC2.19 (8Q), IC4.19 (8Q), RN2.9; also elsewhere on the board
DATA0: IC1.3 (1D), IC3.3 (1D); also elsewhere on the board
DATA1: IC1.4 (2D), IC3.4 (2D); also elsewhere on the board
DATA2: IC1.7 (3D), IC3.7 (3D); also elsewhere on the board
DATA3: IC1.8 (4D), IC3.8 (4D); also elsewhere on the board
DATA4: IC1.13 (5D), IC3.13 (5D); also elsewhere on the board
DATA5: IC1.14 (6D), IC3.14 (6D); also elsewhere on the board
DATA6: IC1.17 (7D), IC3.17 (7D); also elsewhere on the board
DATA7: IC1.18 (8D), IC3.18 (8D); also elsewhere on the board
DATA8: IC2.3 (1D), IC4.3 (1D); also elsewhere on the board
DATA9: IC2.4 (2D), IC4.4 (2D); also elsewhere on the board
DATA10: IC2.7 (3D), IC4.7 (3D); also elsewhere on the board
DATA11: IC2.8 (4D), IC4.8 (4D); also elsewhere on the board
DATA12: IC2.13 (5D), IC4.13 (5D); also elsewhere on the board
DATA13: IC2.14 (6D), IC4.14 (6D); also elsewhere on the board
DATA14: IC2.17 (7D), IC4.17 (7D); also elsewhere on the board
DATA15: IC2.18 (8D), IC4.18 (8D); also elsewhere on the board
GND: IC1.10 (GND), IC2.10 (GND), IC3.10 (GND), IC4.10 (GND), IC5.7 (GND), RN1.1, RN2.1; also elsewhere on the board
unnamed: IC1.11 (ENC), IC2.11 (ENC), IC5.2 (O)
unnamed: IC3.11 (ENC), IC4.11 (ENC), IC5.4 (O)
VCC: IC1.20 (VCC), IC2.20 (VCC), IC3.20 (VCC), IC4.20 (VCC), IC5.14 (VCC); also elsewhere on the board

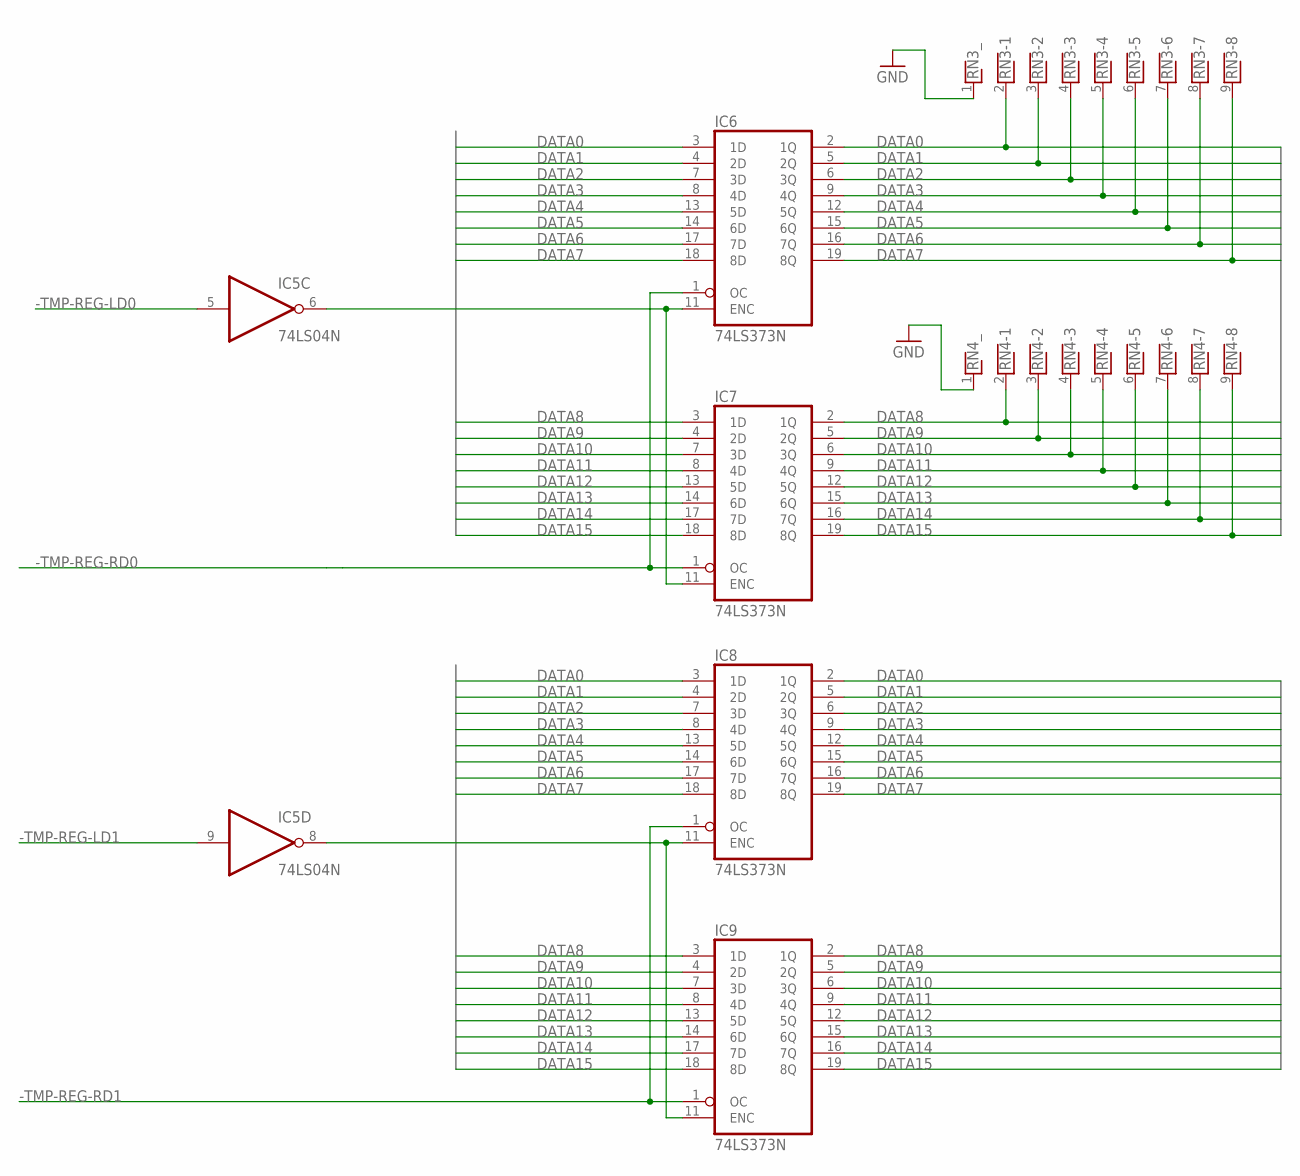
[picture p129: schematic Address and TMP V1.0.sch, sheet 3, TMP Registers]

Parts:
IC5: 74LS04N; DIL14
IC6, IC7, IC8, IC9: 74LS373N; DIL20
RN3, RN4: RNX8; RN-9

Connections:
-TMP-REG-LD0: IC5.5 (I); also elsewhere on the board
-TMP-REG-LD1: IC5.9 (I); also elsewhere on the board
-TMP-REG-RD0: IC6.1 (OC), IC7.1 (OC); also elsewhere on the board
-TMP-REG-RD1: IC8.1 (OC), IC9.1 (OC); also elsewhere on the board
DATA0: IC6.2 (1Q), IC6.3 (1D), IC8.2 (1Q), IC8.3 (1D), RN3.2; also elsewhere on the board
DATA1: IC6.4 (2D), IC6.5 (2Q), IC8.4 (2D), IC8.5 (2Q), RN3.3; also elsewhere on the board
DATA2: IC6.6 (3Q), IC6.7 (3D), IC8.6 (3Q), IC8.7 (3D), RN3.4; also elsewhere on the board
DATA3: IC6.8 (4D), IC6.9 (4Q), IC8.8 (4D), IC8.9 (4Q), RN3.5; also elsewhere on the board
DATA4: IC6.12 (5Q), IC6.13 (5D), IC8.12 (5Q), IC8.13 (5D), RN3.6; also elsewhere on the board
DATA5: IC6.14 (6D), IC6.15 (6Q), IC8.14 (6D), IC8.15 (6Q), RN3.7; also elsewhere on the board
DATA6: IC6.16 (7Q), IC6.17 (7D), IC8.16 (7Q), IC8.17 (7D), RN3.8; also elsewhere on the board
DATA7: IC6.18 (8D), IC6.19 (8Q), IC8.18 (8D), IC8.19 (8Q), RN3.9; also elsewhere on the board
DATA8: IC7.2 (1Q), IC7.3 (1D), IC9.2 (1Q), IC9.3 (1D), RN4.2; also elsewhere on the board
DATA9: IC7.4 (2D), IC7.5 (2Q), IC9.4 (2D), IC9.5 (2Q), RN4.3; also elsewhere on the board
DATA10: IC7.6 (3Q), IC7.7 (3D), IC9.6 (3Q), IC9.7 (3D), RN4.4; also elsewhere on the board
DATA11: IC7.8 (4D), IC7.9 (4Q), IC9.8 (4D), IC9.9 (4Q), RN4.5; also elsewhere on the board
DATA12: IC7.12 (5Q), IC7.13 (5D), IC9.12 (5Q), IC9.13 (5D), RN4.6; also elsewhere on the board
DATA13: IC7.14 (6D), IC7.15 (6Q), IC9.14 (6D), IC9.15 (6Q), RN4.7; also elsewhere on the board
DATA14: IC7.16 (7Q), IC7.17 (7D), IC9.16 (7Q), IC9.17 (7D), RN4.8; also elsewhere on the board
DATA15: IC7.18 (8D), IC7.19 (8Q), IC9.18 (8D), IC9.19 (8Q), RN4.9; also elsewhere on the board
GND: IC5.7 (GND), IC6.10 (GND), IC7.10 (GND), IC8.10 (GND), IC9.10 (GND), RN3.1, RN4.1; also elsewhere on the board
unnamed: IC5.6 (O), IC6.11 (ENC), IC7.11 (ENC)
unnamed: IC5.8 (O), IC8.11 (ENC), IC9.11 (ENC)
VCC: IC5.14 (VCC), IC6.20 (VCC), IC7.20 (VCC), IC8.20 (VCC), IC9.20 (VCC); also elsewhere on the board

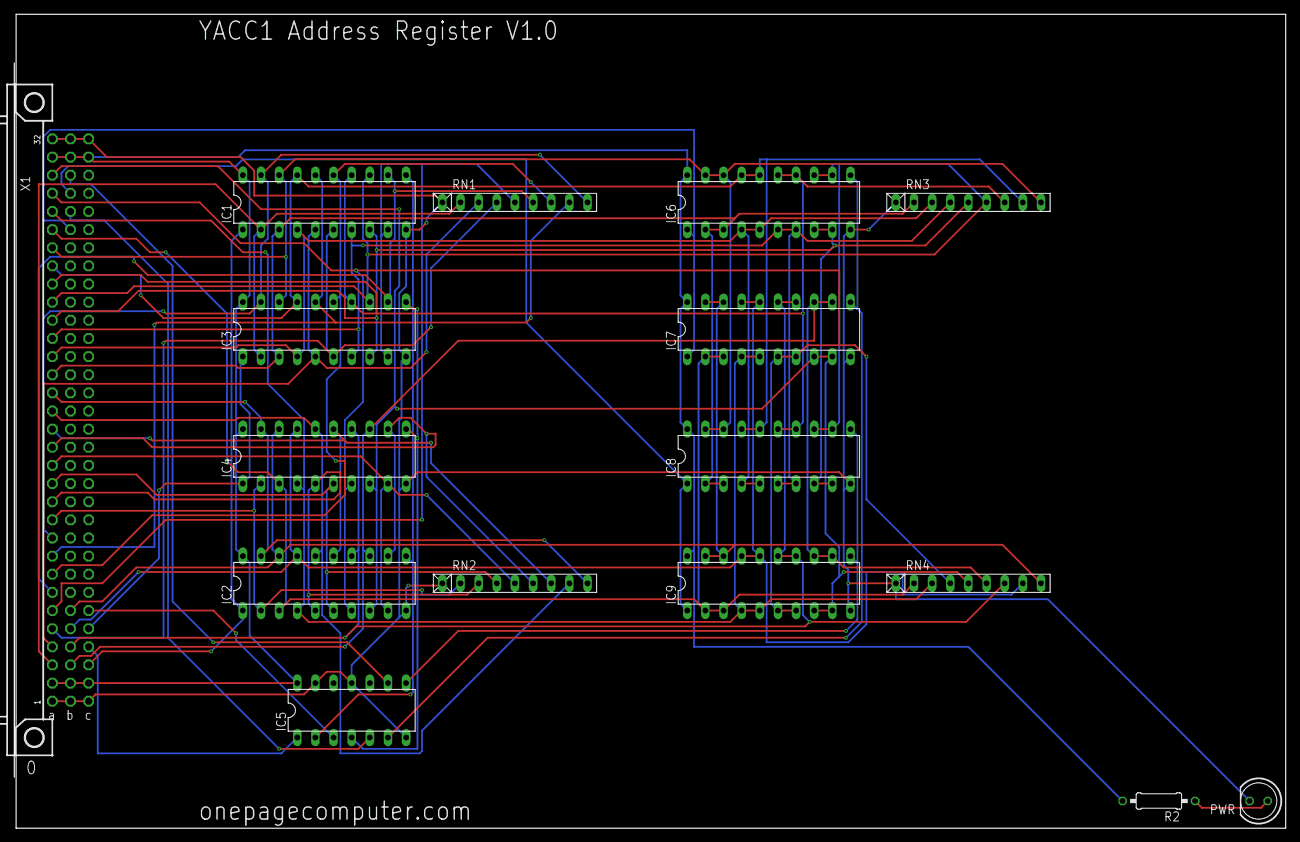
[picture p130: board Address and TMP V1.0.brd from above]

Board: 2 copper layers, 177.8 x 114.0 mm, 16 parts (0 on the bottom side), 47 nets.
