ksr/YACC1-2020/PCB/Working - Under Develolpment/Index Registers 1.2/Index Registers - 1.1.brd

## EAGLE design PCB/Working - Under Develolpment/Index Registers 1.2/Index Registers - 1.1.brd (2020-09-01)

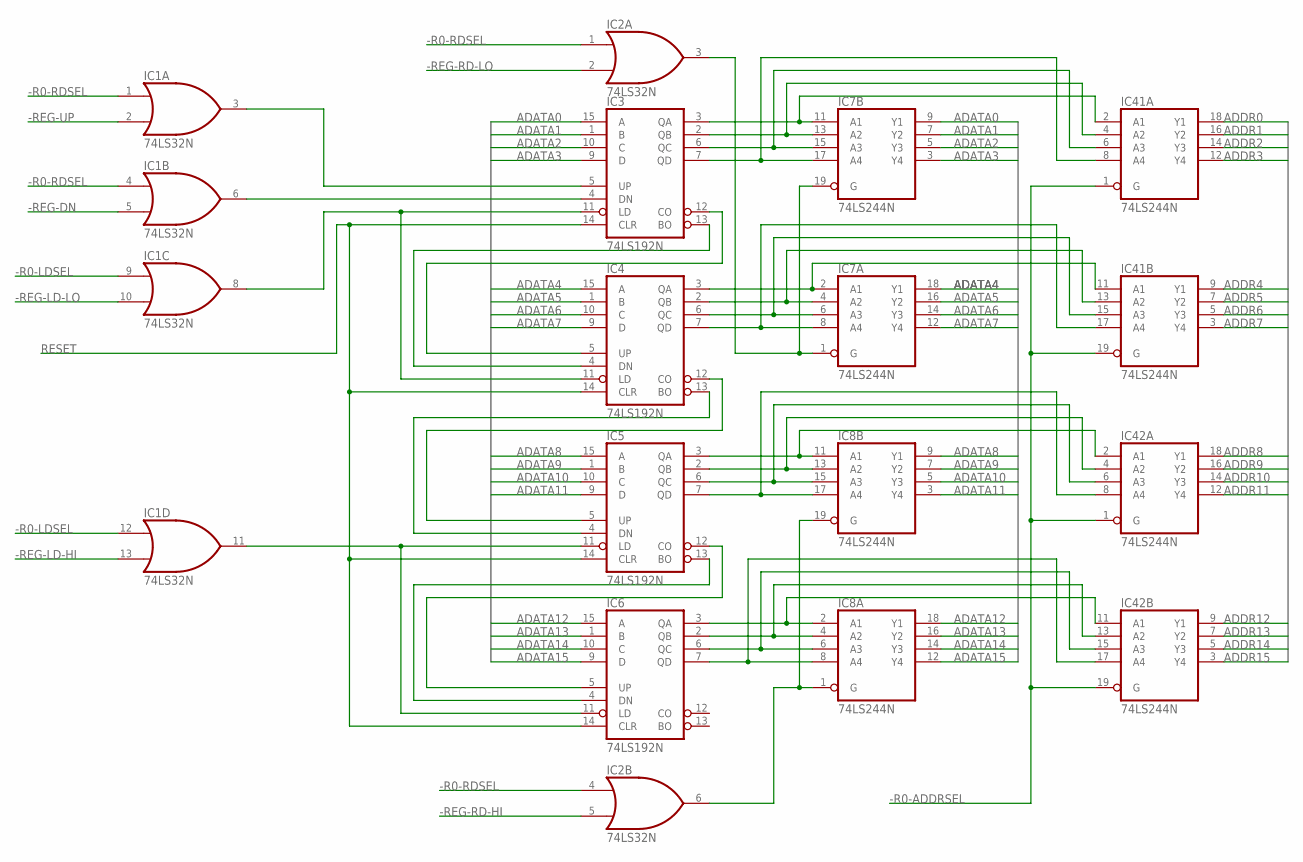
[picture p135: schematic Index Registers - 1.1.sch, sheet 1, R0]

Parts:
IC1, IC2: 74LS32N; DIL14
IC3, IC4, IC5, IC6: 74LS192N; DIL16
IC7, IC8, IC41, IC42: 74LS244N; DIL20

Connections:
-R0-ADDRSEL: IC41.1 (G), IC41.19 (G), IC42.1 (G), IC42.19 (G); also elsewhere on the board
-R0-LDSEL: IC1.9 (I0), IC1.12 (I0); also elsewhere on the board
-R0-RDSEL: IC1.1 (I0), IC1.4 (I0), IC2.1 (I0), IC2.4 (I0); also elsewhere on the board
-REG-DN: IC1.5 (I1); also elsewhere on the board
-REG-LD-HI: IC1.13 (I1); also elsewhere on the board
-REG-LD-LO: IC1.10 (I1); also elsewhere on the board
-REG-RD-HI: IC2.5 (I1); also elsewhere on the board
-REG-RD-LO: IC2.2 (I1); also elsewhere on the board
-REG-UP: IC1.2 (I1); also elsewhere on the board
ADATA0: IC3.15 (A), IC7.9 (Y1); also elsewhere on the board
ADATA1: IC3.1 (B), IC7.7 (Y2); also elsewhere on the board
ADATA2: IC3.10 (C), IC7.5 (Y3); also elsewhere on the board
ADATA3: IC3.9 (D), IC7.3 (Y4); also elsewhere on the board
ADATA4: IC4.15 (A), IC7.18 (Y1); also elsewhere on the board
ADATA5: IC4.1 (B), IC7.16 (Y2); also elsewhere on the board
ADATA6: IC4.10 (C), IC7.14 (Y3); also elsewhere on the board
ADATA7: IC4.9 (D), IC7.12 (Y4); also elsewhere on the board
ADATA8: IC5.15 (A), IC8.9 (Y1); also elsewhere on the board
ADATA9: IC5.1 (B), IC8.7 (Y2); also elsewhere on the board
ADATA10: IC5.10 (C), IC8.5 (Y3); also elsewhere on the board
ADATA11: IC5.9 (D), IC8.3 (Y4); also elsewhere on the board
ADATA12: IC6.15 (A), IC8.18 (Y1); also elsewhere on the board
ADATA13: IC6.1 (B), IC8.16 (Y2); also elsewhere on the board
ADATA14: IC6.10 (C), IC8.14 (Y3); also elsewhere on the board
ADATA15: IC6.9 (D), IC8.12 (Y4); also elsewhere on the board
ADDR0: IC41.18 (Y1); also elsewhere on the board
ADDR1: IC41.16 (Y2); also elsewhere on the board
ADDR2: IC41.14 (Y3); also elsewhere on the board
ADDR3: IC41.12 (Y4); also elsewhere on the board
ADDR4: IC41.9 (Y1); also elsewhere on the board
ADDR5: IC41.7 (Y2); also elsewhere on the board
ADDR6: IC41.5 (Y3); also elsewhere on the board
ADDR7: IC41.3 (Y4); also elsewhere on the board
ADDR8: IC42.18 (Y1); also elsewhere on the board
ADDR9: IC42.16 (Y2); also elsewhere on the board
ADDR10: IC42.14 (Y3); also elsewhere on the board
ADDR11: IC42.12 (Y4); also elsewhere on the board
ADDR12: IC42.9 (Y1); also elsewhere on the board
ADDR13: IC42.7 (Y2); also elsewhere on the board
ADDR14: IC42.5 (Y3); also elsewhere on the board
ADDR15: IC42.3 (Y4); also elsewhere on the board
GND: IC1.7 (GND), IC2.7 (GND), IC3.8 (GND), IC4.8 (GND), IC5.8 (GND), IC6.8 (GND), IC7.10 (GND), IC8.10 (GND), IC41.10 (GND), IC42.10 (GND); also elsewhere on the board
unnamed: IC3.13 (BO), IC4.4 (DN)
unnamed: IC3.12 (CO), IC4.5 (UP)
unnamed: IC4.13 (BO), IC5.4 (DN)
unnamed: IC4.12 (CO), IC5.5 (UP)
unnamed: IC5.13 (BO), IC6.4 (DN)
unnamed: IC5.12 (CO), IC6.5 (UP)
unnamed: IC1.8 (O), IC3.11 (LD), IC4.11 (LD)
unnamed: IC1.3 (O), IC3.5 (UP)
unnamed: IC1.6 (O), IC3.4 (DN)
unnamed: IC2.3 (O), IC7.1 (G), IC7.19 (G)
unnamed: IC2.6 (O), IC8.1 (G), IC8.19 (G)
unnamed: IC1.11 (O), IC5.11 (LD), IC6.11 (LD)
unnamed: IC3.3 (QA), IC7.11 (A1), IC41.2 (A1)
unnamed: IC3.2 (QB), IC7.13 (A2), IC41.4 (A2)
unnamed: IC3.6 (QC), IC7.15 (A3), IC41.6 (A3)
unnamed: IC3.7 (QD), IC7.17 (A4), IC41.8 (A4)
unnamed: IC4.3 (QA), IC7.2 (A1), IC41.11 (A1)
unnamed: IC4.2 (QB), IC7.4 (A2), IC41.13 (A2)
unnamed: IC4.6 (QC), IC7.6 (A3), IC41.15 (A3)
unnamed: IC4.7 (QD), IC7.8 (A4), IC41.17 (A4)
unnamed: IC5.3 (QA), IC8.11 (A1), IC42.2 (A1)
unnamed: IC5.2 (QB), IC8.13 (A2), IC42.4 (A2)
unnamed: IC5.6 (QC), IC8.15 (A3), IC42.6 (A3)
unnamed: IC5.7 (QD), IC8.17 (A4), IC42.8 (A4)
unnamed: IC6.3 (QA), IC8.2 (A1), IC42.11 (A1)
unnamed: IC6.2 (QB), IC8.4 (A2), IC42.13 (A2)
unnamed: IC6.6 (QC), IC8.6 (A3), IC42.15 (A3)
unnamed: IC6.7 (QD), IC8.8 (A4), IC42.17 (A4)
RESET: IC3.14 (CLR), IC4.14 (CLR), IC5.14 (CLR), IC6.14 (CLR); also elsewhere on the board
VCC: IC1.14 (VCC), IC2.14 (VCC), IC3.16 (VCC), IC4.16 (VCC), IC5.16 (VCC), IC6.16 (VCC), IC7.20 (VCC), IC8.20 (VCC), IC41.20 (VCC), IC42.20 (VCC); also elsewhere on the board
