ksr/YACC1-2020/PCB/Working - Under Develolpment/Index Registers 1.2/Index Registers - 1.1.brd

## EAGLE design PCB/Working - Under Develolpment/Index Registers 1.2/Index Registers - 1.1.brd (continued)

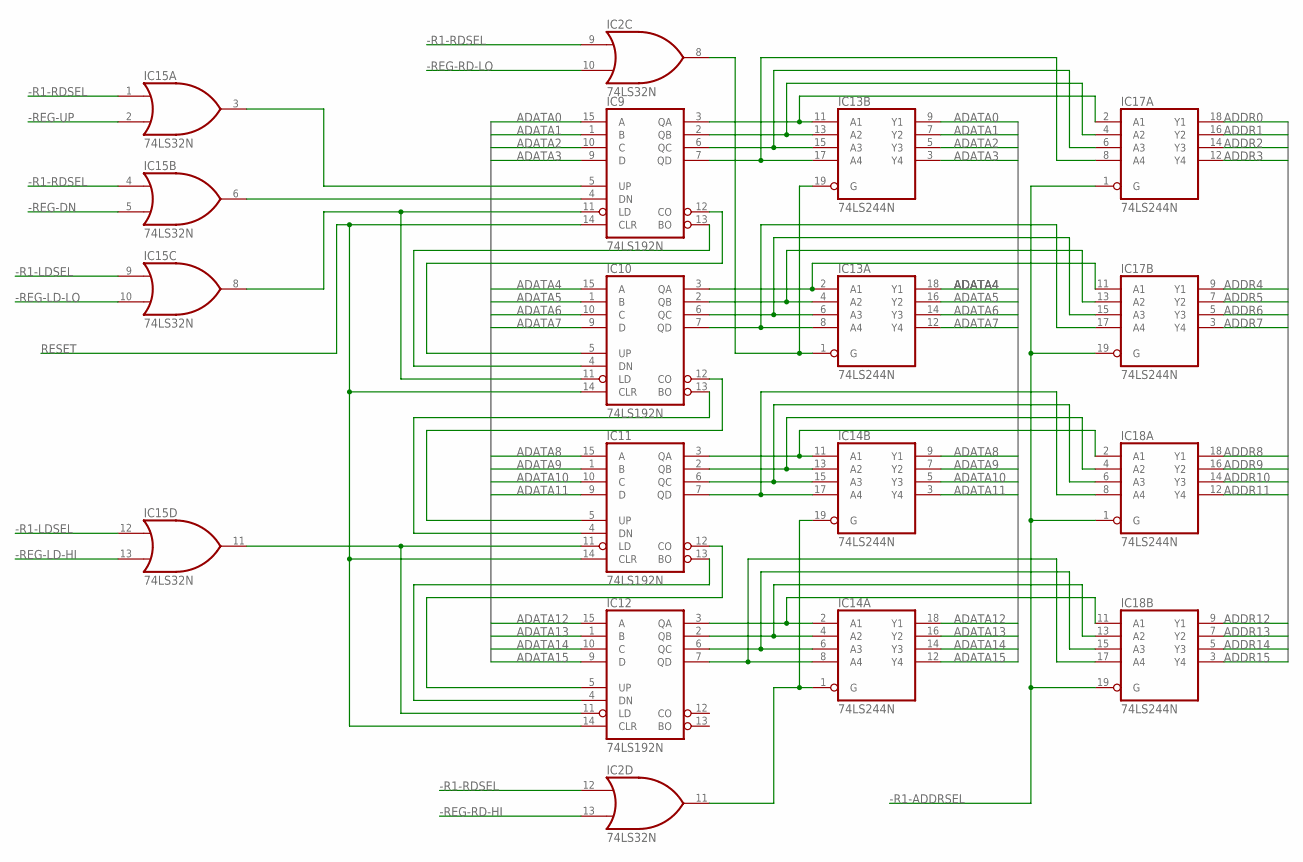
[picture p136: schematic Index Registers - 1.1.sch, sheet 2, R1]

Parts:
IC2, IC15: 74LS32N; DIL14
IC9, IC10, IC11, IC12: 74LS192N; DIL16
IC13, IC14, IC17, IC18: 74LS244N; DIL20

Connections:
-R1-ADDRSEL: IC17.1 (G), IC17.19 (G), IC18.1 (G), IC18.19 (G); also elsewhere on the board
-R1-LDSEL: IC15.9 (I0), IC15.12 (I0); also elsewhere on the board
-R1-RDSEL: IC2.9 (I0), IC2.12 (I0), IC15.1 (I0), IC15.4 (I0); also elsewhere on the board
-REG-DN: IC15.5 (I1); also elsewhere on the board
-REG-LD-HI: IC15.13 (I1); also elsewhere on the board
-REG-LD-LO: IC15.10 (I1); also elsewhere on the board
-REG-RD-HI: IC2.13 (I1); also elsewhere on the board
-REG-RD-LO: IC2.10 (I1); also elsewhere on the board
-REG-UP: IC15.2 (I1); also elsewhere on the board
ADATA0: IC9.15 (A), IC13.9 (Y1); also elsewhere on the board
ADATA1: IC9.1 (B), IC13.7 (Y2); also elsewhere on the board
ADATA2: IC9.10 (C), IC13.5 (Y3); also elsewhere on the board
ADATA3: IC9.9 (D), IC13.3 (Y4); also elsewhere on the board
ADATA4: IC10.15 (A), IC13.18 (Y1); also elsewhere on the board
ADATA5: IC10.1 (B), IC13.16 (Y2); also elsewhere on the board
ADATA6: IC10.10 (C), IC13.14 (Y3); also elsewhere on the board
ADATA7: IC10.9 (D), IC13.12 (Y4); also elsewhere on the board
ADATA8: IC11.15 (A), IC14.9 (Y1); also elsewhere on the board
ADATA9: IC11.1 (B), IC14.7 (Y2); also elsewhere on the board
ADATA10: IC11.10 (C), IC14.5 (Y3); also elsewhere on the board
ADATA11: IC11.9 (D), IC14.3 (Y4); also elsewhere on the board
ADATA12: IC12.15 (A), IC14.18 (Y1); also elsewhere on the board
ADATA13: IC12.1 (B), IC14.16 (Y2); also elsewhere on the board
ADATA14: IC12.10 (C), IC14.14 (Y3); also elsewhere on the board
ADATA15: IC12.9 (D), IC14.12 (Y4); also elsewhere on the board
ADDR0: IC17.18 (Y1); also elsewhere on the board
ADDR1: IC17.16 (Y2); also elsewhere on the board
ADDR2: IC17.14 (Y3); also elsewhere on the board
ADDR3: IC17.12 (Y4); also elsewhere on the board
ADDR4: IC17.9 (Y1); also elsewhere on the board
ADDR5: IC17.7 (Y2); also elsewhere on the board
ADDR6: IC17.5 (Y3); also elsewhere on the board
ADDR7: IC17.3 (Y4); also elsewhere on the board
ADDR8: IC18.18 (Y1); also elsewhere on the board
ADDR9: IC18.16 (Y2); also elsewhere on the board
ADDR10: IC18.14 (Y3); also elsewhere on the board
ADDR11: IC18.12 (Y4); also elsewhere on the board
ADDR12: IC18.9 (Y1); also elsewhere on the board
ADDR13: IC18.7 (Y2); also elsewhere on the board
ADDR14: IC18.5 (Y3); also elsewhere on the board
ADDR15: IC18.3 (Y4); also elsewhere on the board
GND: IC2.7 (GND), IC9.8 (GND), IC10.8 (GND), IC11.8 (GND), IC12.8 (GND), IC13.10 (GND), IC14.10 (GND), IC15.7 (GND), IC17.10 (GND), IC18.10 (GND); also elsewhere on the board
unnamed: IC9.13 (BO), IC10.4 (DN)
unnamed: IC9.12 (CO), IC10.5 (UP)
unnamed: IC10.13 (BO), IC11.4 (DN)
unnamed: IC10.12 (CO), IC11.5 (UP)
unnamed: IC11.13 (BO), IC12.4 (DN)
unnamed: IC11.12 (CO), IC12.5 (UP)
unnamed: IC9.11 (LD), IC10.11 (LD), IC15.8 (O)
unnamed: IC9.5 (UP), IC15.3 (O)
unnamed: IC9.4 (DN), IC15.6 (O)
unnamed: IC2.8 (O), IC13.1 (G), IC13.19 (G)
unnamed: IC2.11 (O), IC14.1 (G), IC14.19 (G)
unnamed: IC11.11 (LD), IC12.11 (LD), IC15.11 (O)
unnamed: IC9.3 (QA), IC13.11 (A1), IC17.2 (A1)
unnamed: IC9.2 (QB), IC13.13 (A2), IC17.4 (A2)
unnamed: IC9.6 (QC), IC13.15 (A3), IC17.6 (A3)
unnamed: IC9.7 (QD), IC13.17 (A4), IC17.8 (A4)
unnamed: IC10.3 (QA), IC13.2 (A1), IC17.11 (A1)
unnamed: IC10.2 (QB), IC13.4 (A2), IC17.13 (A2)
unnamed: IC10.6 (QC), IC13.6 (A3), IC17.15 (A3)
unnamed: IC10.7 (QD), IC13.8 (A4), IC17.17 (A4)
unnamed: IC11.3 (QA), IC14.11 (A1), IC18.2 (A1)
unnamed: IC11.2 (QB), IC14.13 (A2), IC18.4 (A2)
unnamed: IC11.6 (QC), IC14.15 (A3), IC18.6 (A3)
unnamed: IC11.7 (QD), IC14.17 (A4), IC18.8 (A4)
unnamed: IC12.3 (QA), IC14.2 (A1), IC18.11 (A1)
unnamed: IC12.2 (QB), IC14.4 (A2), IC18.13 (A2)
unnamed: IC12.6 (QC), IC14.6 (A3), IC18.15 (A3)
unnamed: IC12.7 (QD), IC14.8 (A4), IC18.17 (A4)
RESET: IC9.14 (CLR), IC10.14 (CLR), IC11.14 (CLR), IC12.14 (CLR); also elsewhere on the board
VCC: IC2.14 (VCC), IC9.16 (VCC), IC10.16 (VCC), IC11.16 (VCC), IC12.16 (VCC), IC13.20 (VCC), IC14.20 (VCC), IC15.14 (VCC), IC17.20 (VCC), IC18.20 (VCC); also elsewhere on the board

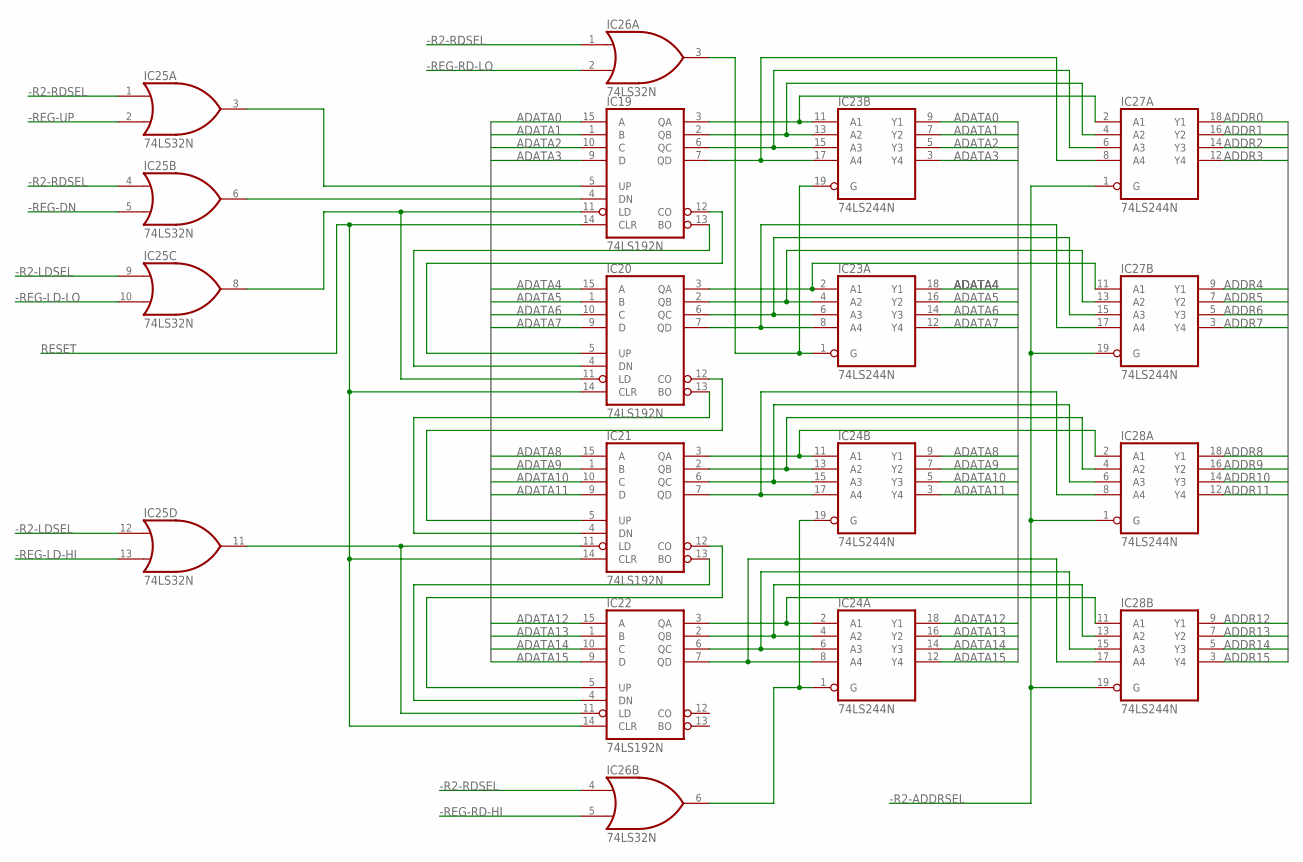
[picture p137: schematic Index Registers - 1.1.sch, sheet 3, R2]

Parts:
IC19, IC20, IC21, IC22: 74LS192N; DIL16
IC23, IC24, IC27, IC28: 74LS244N; DIL20
IC25, IC26: 74LS32N; DIL14

Connections:
-R2-ADDRSEL: IC27.1 (G), IC27.19 (G), IC28.1 (G), IC28.19 (G); also elsewhere on the board
-R2-LDSEL: IC25.9 (I0), IC25.12 (I0); also elsewhere on the board
-R2-RDSEL: IC25.1 (I0), IC25.4 (I0), IC26.1 (I0), IC26.4 (I0); also elsewhere on the board
-REG-DN: IC25.5 (I1); also elsewhere on the board
-REG-LD-HI: IC25.13 (I1); also elsewhere on the board
-REG-LD-LO: IC25.10 (I1); also elsewhere on the board
-REG-RD-HI: IC26.5 (I1); also elsewhere on the board
-REG-RD-LO: IC26.2 (I1); also elsewhere on the board
-REG-UP: IC25.2 (I1); also elsewhere on the board
ADATA0: IC19.15 (A), IC23.9 (Y1); also elsewhere on the board
ADATA1: IC19.1 (B), IC23.7 (Y2); also elsewhere on the board
ADATA2: IC19.10 (C), IC23.5 (Y3); also elsewhere on the board
ADATA3: IC19.9 (D), IC23.3 (Y4); also elsewhere on the board
ADATA4: IC20.15 (A), IC23.18 (Y1); also elsewhere on the board
ADATA5: IC20.1 (B), IC23.16 (Y2); also elsewhere on the board
ADATA6: IC20.10 (C), IC23.14 (Y3); also elsewhere on the board
ADATA7: IC20.9 (D), IC23.12 (Y4); also elsewhere on the board
ADATA8: IC21.15 (A), IC24.9 (Y1); also elsewhere on the board
ADATA9: IC21.1 (B), IC24.7 (Y2); also elsewhere on the board
ADATA10: IC21.10 (C), IC24.5 (Y3); also elsewhere on the board
ADATA11: IC21.9 (D), IC24.3 (Y4); also elsewhere on the board
ADATA12: IC22.15 (A), IC24.18 (Y1); also elsewhere on the board
ADATA13: IC22.1 (B), IC24.16 (Y2); also elsewhere on the board
ADATA14: IC22.10 (C), IC24.14 (Y3); also elsewhere on the board
ADATA15: IC22.9 (D), IC24.12 (Y4); also elsewhere on the board
ADDR0: IC27.18 (Y1); also elsewhere on the board
ADDR1: IC27.16 (Y2); also elsewhere on the board
ADDR2: IC27.14 (Y3); also elsewhere on the board
ADDR3: IC27.12 (Y4); also elsewhere on the board
ADDR4: IC27.9 (Y1); also elsewhere on the board
ADDR5: IC27.7 (Y2); also elsewhere on the board
ADDR6: IC27.5 (Y3); also elsewhere on the board
ADDR7: IC27.3 (Y4); also elsewhere on the board
ADDR8: IC28.18 (Y1); also elsewhere on the board
ADDR9: IC28.16 (Y2); also elsewhere on the board
ADDR10: IC28.14 (Y3); also elsewhere on the board
ADDR11: IC28.12 (Y4); also elsewhere on the board
ADDR12: IC28.9 (Y1); also elsewhere on the board
ADDR13: IC28.7 (Y2); also elsewhere on the board
ADDR14: IC28.5 (Y3); also elsewhere on the board
ADDR15: IC28.3 (Y4); also elsewhere on the board
GND: IC19.8 (GND), IC20.8 (GND), IC21.8 (GND), IC22.8 (GND), IC23.10 (GND), IC24.10 (GND), IC25.7 (GND), IC26.7 (GND), IC27.10 (GND), IC28.10 (GND); also elsewhere on the board
unnamed: IC19.13 (BO), IC20.4 (DN)
unnamed: IC19.12 (CO), IC20.5 (UP)
unnamed: IC20.13 (BO), IC21.4 (DN)
unnamed: IC20.12 (CO), IC21.5 (UP)
unnamed: IC21.13 (BO), IC22.4 (DN)
unnamed: IC21.12 (CO), IC22.5 (UP)
unnamed: IC19.11 (LD), IC20.11 (LD), IC25.8 (O)
unnamed: IC19.5 (UP), IC25.3 (O)
unnamed: IC19.4 (DN), IC25.6 (O)
unnamed: IC23.1 (G), IC23.19 (G), IC26.3 (O)
unnamed: IC24.1 (G), IC24.19 (G), IC26.6 (O)
unnamed: IC21.11 (LD), IC22.11 (LD), IC25.11 (O)
unnamed: IC19.3 (QA), IC23.11 (A1), IC27.2 (A1)
unnamed: IC19.2 (QB), IC23.13 (A2), IC27.4 (A2)
unnamed: IC19.6 (QC), IC23.15 (A3), IC27.6 (A3)
unnamed: IC19.7 (QD), IC23.17 (A4), IC27.8 (A4)
unnamed: IC20.3 (QA), IC23.2 (A1), IC27.11 (A1)
unnamed: IC20.2 (QB), IC23.4 (A2), IC27.13 (A2)
unnamed: IC20.6 (QC), IC23.6 (A3), IC27.15 (A3)
unnamed: IC20.7 (QD), IC23.8 (A4), IC27.17 (A4)
unnamed: IC21.3 (QA), IC24.11 (A1), IC28.2 (A1)
unnamed: IC21.2 (QB), IC24.13 (A2), IC28.4 (A2)
unnamed: IC21.6 (QC), IC24.15 (A3), IC28.6 (A3)
unnamed: IC21.7 (QD), IC24.17 (A4), IC28.8 (A4)
unnamed: IC22.3 (QA), IC24.2 (A1), IC28.11 (A1)
unnamed: IC22.2 (QB), IC24.4 (A2), IC28.13 (A2)
unnamed: IC22.6 (QC), IC24.6 (A3), IC28.15 (A3)
unnamed: IC22.7 (QD), IC24.8 (A4), IC28.17 (A4)
RESET: IC19.14 (CLR), IC20.14 (CLR), IC21.14 (CLR), IC22.14 (CLR); also elsewhere on the board
VCC: IC19.16 (VCC), IC20.16 (VCC), IC21.16 (VCC), IC22.16 (VCC), IC23.20 (VCC), IC24.20 (VCC), IC25.14 (VCC), IC26.14 (VCC), IC27.20 (VCC), IC28.20 (VCC); also elsewhere on the board

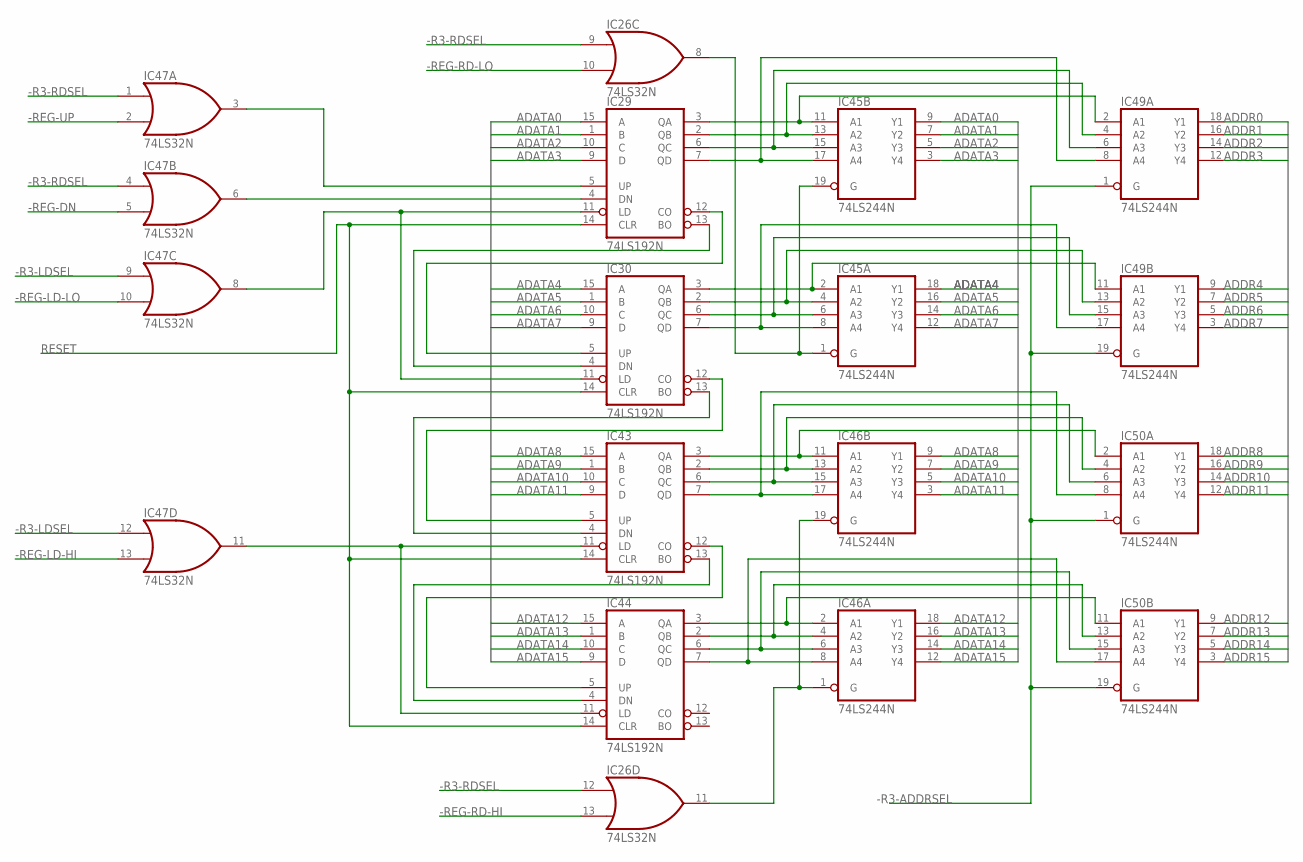
[picture p138: schematic Index Registers - 1.1.sch, sheet 4, R3]

Parts:
IC26, IC47: 74LS32N; DIL14
IC29, IC30, IC43, IC44: 74LS192N; DIL16
IC45, IC46, IC49, IC50: 74LS244N; DIL20

Connections:
-R3-ADDRSEL: IC49.1 (G), IC49.19 (G), IC50.1 (G), IC50.19 (G); also elsewhere on the board
-R3-LDSEL: IC47.9 (I0), IC47.12 (I0); also elsewhere on the board
-R3-RDSEL: IC26.9 (I0), IC26.12 (I0), IC47.1 (I0), IC47.4 (I0); also elsewhere on the board
-REG-DN: IC47.5 (I1); also elsewhere on the board
-REG-LD-HI: IC47.13 (I1); also elsewhere on the board
-REG-LD-LO: IC47.10 (I1); also elsewhere on the board
-REG-RD-HI: IC26.13 (I1); also elsewhere on the board
-REG-RD-LO: IC26.10 (I1); also elsewhere on the board
-REG-UP: IC47.2 (I1); also elsewhere on the board
ADATA0: IC29.15 (A), IC45.9 (Y1); also elsewhere on the board
ADATA1: IC29.1 (B), IC45.7 (Y2); also elsewhere on the board
ADATA2: IC29.10 (C), IC45.5 (Y3); also elsewhere on the board
ADATA3: IC29.9 (D), IC45.3 (Y4); also elsewhere on the board
ADATA4: IC30.15 (A), IC45.18 (Y1); also elsewhere on the board
ADATA5: IC30.1 (B), IC45.16 (Y2); also elsewhere on the board
ADATA6: IC30.10 (C), IC45.14 (Y3); also elsewhere on the board
ADATA7: IC30.9 (D), IC45.12 (Y4); also elsewhere on the board
ADATA8: IC43.15 (A), IC46.9 (Y1); also elsewhere on the board
ADATA9: IC43.1 (B), IC46.7 (Y2); also elsewhere on the board
ADATA10: IC43.10 (C), IC46.5 (Y3); also elsewhere on the board
ADATA11: IC43.9 (D), IC46.3 (Y4); also elsewhere on the board
ADATA12: IC44.15 (A), IC46.18 (Y1); also elsewhere on the board
ADATA13: IC44.1 (B), IC46.16 (Y2); also elsewhere on the board
ADATA14: IC44.10 (C), IC46.14 (Y3); also elsewhere on the board
ADATA15: IC44.9 (D), IC46.12 (Y4); also elsewhere on the board
ADDR0: IC49.18 (Y1); also elsewhere on the board
ADDR1: IC49.16 (Y2); also elsewhere on the board
ADDR2: IC49.14 (Y3); also elsewhere on the board
ADDR3: IC49.12 (Y4); also elsewhere on the board
ADDR4: IC49.9 (Y1); also elsewhere on the board
ADDR5: IC49.7 (Y2); also elsewhere on the board
ADDR6: IC49.5 (Y3); also elsewhere on the board
ADDR7: IC49.3 (Y4); also elsewhere on the board
ADDR8: IC50.18 (Y1); also elsewhere on the board
ADDR9: IC50.16 (Y2); also elsewhere on the board
ADDR10: IC50.14 (Y3); also elsewhere on the board
ADDR11: IC50.12 (Y4); also elsewhere on the board
ADDR12: IC50.9 (Y1); also elsewhere on the board
ADDR13: IC50.7 (Y2); also elsewhere on the board
ADDR14: IC50.5 (Y3); also elsewhere on the board
ADDR15: IC50.3 (Y4); also elsewhere on the board
GND: IC26.7 (GND), IC29.8 (GND), IC30.8 (GND), IC43.8 (GND), IC44.8 (GND), IC45.10 (GND), IC46.10 (GND), IC47.7 (GND), IC49.10 (GND), IC50.10 (GND); also elsewhere on the board
unnamed: IC29.13 (BO), IC30.4 (DN)
unnamed: IC29.12 (CO), IC30.5 (UP)
unnamed: IC30.13 (BO), IC43.4 (DN)
unnamed: IC30.12 (CO), IC43.5 (UP)
unnamed: IC43.13 (BO), IC44.4 (DN)
unnamed: IC43.12 (CO), IC44.5 (UP)
unnamed: IC29.11 (LD), IC30.11 (LD), IC47.8 (O)
unnamed: IC29.5 (UP), IC47.3 (O)
unnamed: IC29.4 (DN), IC47.6 (O)
unnamed: IC26.8 (O), IC45.1 (G), IC45.19 (G)
unnamed: IC26.11 (O), IC46.1 (G), IC46.19 (G)
unnamed: IC43.11 (LD), IC44.11 (LD), IC47.11 (O)
unnamed: IC29.3 (QA), IC45.11 (A1), IC49.2 (A1)
unnamed: IC29.2 (QB), IC45.13 (A2), IC49.4 (A2)
unnamed: IC29.6 (QC), IC45.15 (A3), IC49.6 (A3)
unnamed: IC29.7 (QD), IC45.17 (A4), IC49.8 (A4)
unnamed: IC30.3 (QA), IC45.2 (A1), IC49.11 (A1)
unnamed: IC30.2 (QB), IC45.4 (A2), IC49.13 (A2)
unnamed: IC30.6 (QC), IC45.6 (A3), IC49.15 (A3)
unnamed: IC30.7 (QD), IC45.8 (A4), IC49.17 (A4)
unnamed: IC43.3 (QA), IC46.11 (A1), IC50.2 (A1)
unnamed: IC43.2 (QB), IC46.13 (A2), IC50.4 (A2)
unnamed: IC43.6 (QC), IC46.15 (A3), IC50.6 (A3)
unnamed: IC43.7 (QD), IC46.17 (A4), IC50.8 (A4)
unnamed: IC44.3 (QA), IC46.2 (A1), IC50.11 (A1)
unnamed: IC44.2 (QB), IC46.4 (A2), IC50.13 (A2)
unnamed: IC44.6 (QC), IC46.6 (A3), IC50.15 (A3)
unnamed: IC44.7 (QD), IC46.8 (A4), IC50.17 (A4)
RESET: IC29.14 (CLR), IC30.14 (CLR), IC43.14 (CLR), IC44.14 (CLR); also elsewhere on the board
VCC: IC26.14 (VCC), IC29.16 (VCC), IC30.16 (VCC), IC43.16 (VCC), IC44.16 (VCC), IC45.20 (VCC), IC46.20 (VCC), IC47.14 (VCC), IC49.20 (VCC), IC50.20 (VCC); also elsewhere on the board

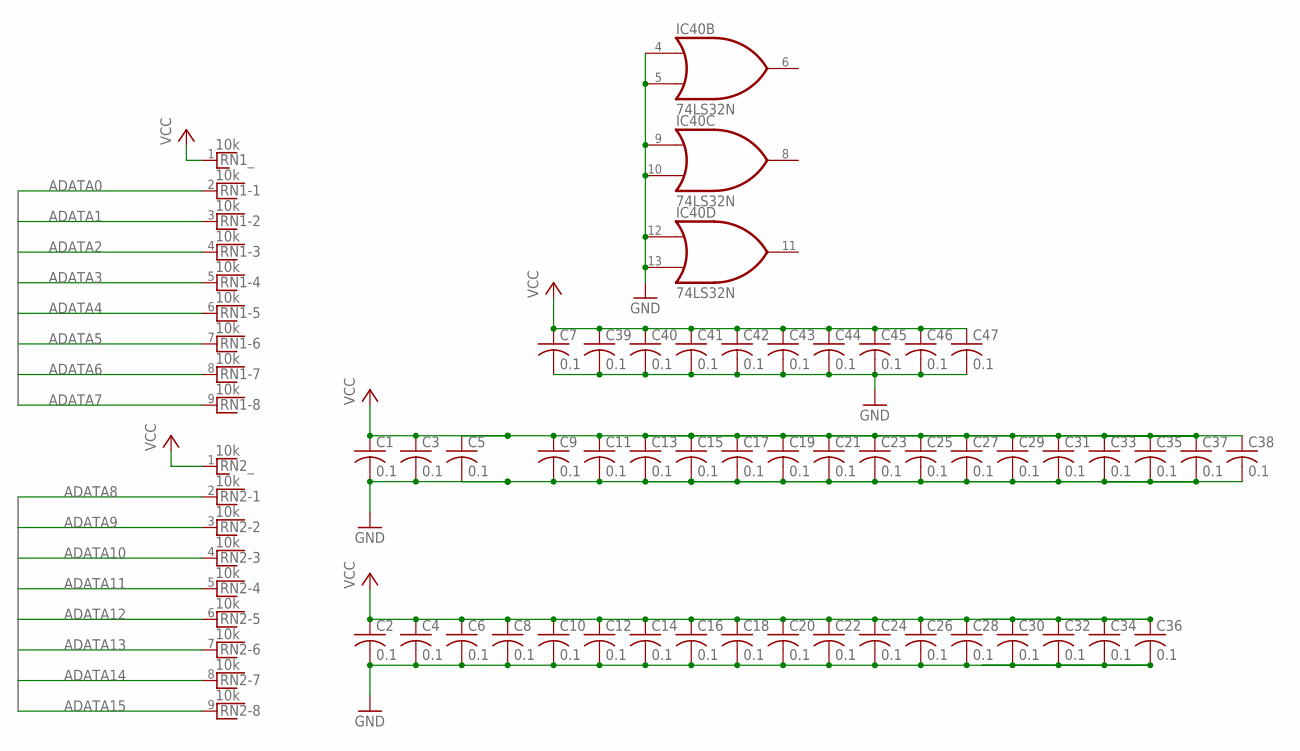
[picture p139: schematic Index Registers - 1.1.sch, sheet 5, PULLUPS & BYPASS & UNUSED]

Parts:
C1, C2, C3, C4, C5, C6, C7, C8, C9, C10, C11, C12, C13, C14, C15, C16, C17, C18, C19, C20, C21, C22, C23, C24, C25, C26, C27, C28, C29, C30, C31, C32, C33, C34, C35, C36, C37, C38, C39, C40, C41, C42, C43, C44, C45, C46, C47: 0.1; C025-040X050
IC40: 74LS32N; DIL14
RN1, RN2: 10k; RN-9

Connections:
ADATA0: RN1.2; also elsewhere on the board
ADATA1: RN1.3; also elsewhere on the board
ADATA2: RN1.4; also elsewhere on the board
ADATA3: RN1.5; also elsewhere on the board
ADATA4: RN1.6; also elsewhere on the board
ADATA5: RN1.7; also elsewhere on the board
ADATA6: RN1.8; also elsewhere on the board
ADATA7: RN1.9; also elsewhere on the board
ADATA8: RN2.2; also elsewhere on the board
ADATA9: RN2.3; also elsewhere on the board
ADATA10: RN2.4; also elsewhere on the board
ADATA11: RN2.5; also elsewhere on the board
ADATA12: RN2.6; also elsewhere on the board
ADATA13: RN2.7; also elsewhere on the board
ADATA14: RN2.8; also elsewhere on the board
ADATA15: RN2.9; also elsewhere on the board
GND: C1.2, C2.2, C3.2, C4.2, C5.2, C6.2, C7.2, C8.2, C9.2, C10.2, C11.2, C12.2, C13.2, C14.2, C15.2, C16.2, C17.2, C18.2, C19.2, C20.2, C21.2, C22.2, C23.2, C24.2, C25.2, C26.2, C27.2, C28.2, C29.2, C30.2, C31.2, C32.2, C33.2, C34.2, C35.2, C36.2, C37.2, C38.2, C39.2, C40.2, C41.2, C42.2, C43.2, C44.2, C45.2, C46.2, C47.2, IC40.4 (I0), IC40.5 (I1), IC40.7 (GND), IC40.9 (I0), IC40.10 (I1), IC40.12 (I0), IC40.13 (I1); also elsewhere on the board
VCC: C1.1, C2.1, C3.1, C4.1, C5.1, C6.1, C7.1, C8.1, C9.1, C10.1, C11.1, C12.1, C13.1, C14.1, C15.1, C16.1, C17.1, C18.1, C19.1, C20.1, C21.1, C22.1, C23.1, C24.1, C25.1, C26.1, C27.1, C28.1, C29.1, C30.1, C31.1, C32.1, C33.1, C34.1, C35.1, C36.1, C37.1, C38.1, C39.1, C40.1, C41.1, C42.1, C43.1, C44.1, C45.1, C46.1, C47.1, IC40.14 (VCC), RN1.1, RN2.1; also elsewhere on the board

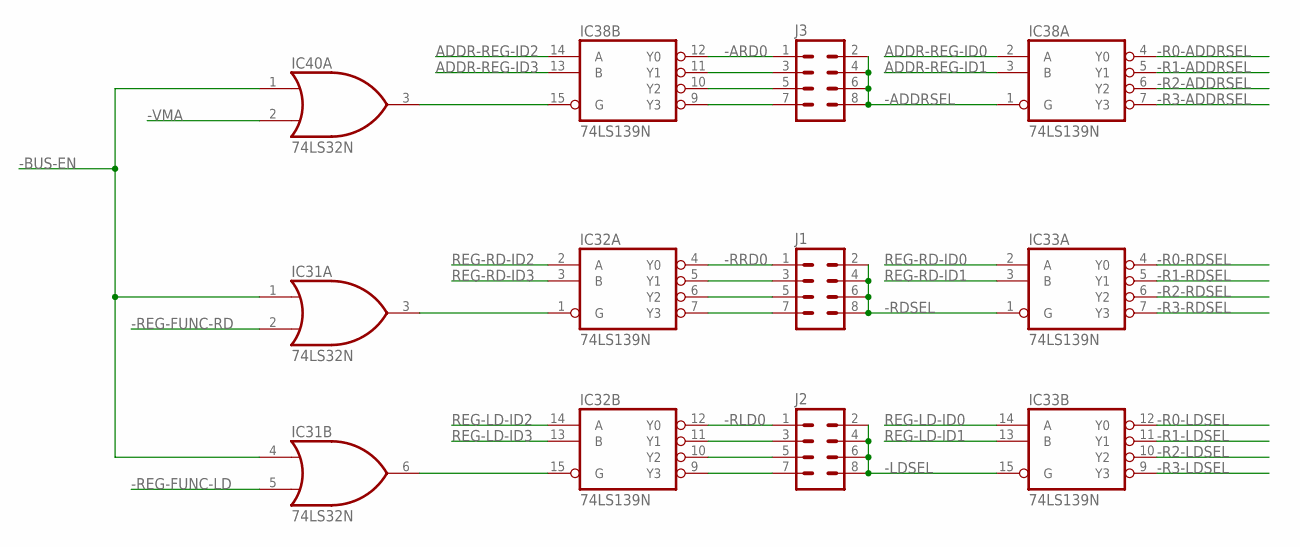
[picture p140: schematic Index Registers - 1.1.sch, sheet 6, Select Logic]

Parts:
IC31, IC40: 74LS32N; DIL14
IC32, IC33, IC38: 74LS139N; DIL16
J1, J2, J3: M04X2; 2X4

Connections:
-ADDRSEL: IC38.1 (G), J3.2, J3.4, J3.6, J3.8
-ARD0: IC38.12 (Y0), J3.1
-BUS-EN: IC31.1 (I0), IC31.4 (I0), IC40.1 (I0); also elsewhere on the board
-LDSEL: IC33.15 (G), J2.2, J2.4, J2.6, J2.8; also elsewhere on the board
-R0-ADDRSEL: IC38.4 (Y0); also elsewhere on the board
-R0-LDSEL: IC33.12 (Y0); also elsewhere on the board
-R0-RDSEL: IC33.4 (Y0); also elsewhere on the board
-R1-ADDRSEL: IC38.5 (Y1); also elsewhere on the board
-R1-LDSEL: IC33.11 (Y1); also elsewhere on the board
-R1-RDSEL: IC33.5 (Y1); also elsewhere on the board
-R2-ADDRSEL: IC38.6 (Y2); also elsewhere on the board
-R2-LDSEL: IC33.10 (Y2); also elsewhere on the board
-R2-RDSEL: IC33.6 (Y2); also elsewhere on the board
-R3-ADDRSEL: IC38.7 (Y3); also elsewhere on the board
-R3-LDSEL: IC33.9 (Y3); also elsewhere on the board
-R3-RDSEL: IC33.7 (Y3); also elsewhere on the board
-RDSEL: IC33.1 (G), J1.2, J1.4, J1.6, J1.8; also elsewhere on the board
-REG-FUNC-LD: IC31.5 (I1); also elsewhere on the board
-REG-FUNC-RD: IC31.2 (I1); also elsewhere on the board
-RLD0: IC32.12 (Y0), J2.1
-RRD0: IC32.4 (Y0), J1.1
-VMA: IC40.2 (I1); also elsewhere on the board
ADDR-REG-ID0: IC38.2 (A); also elsewhere on the board
ADDR-REG-ID1: IC38.3 (B); also elsewhere on the board
ADDR-REG-ID2: IC38.14 (A); also elsewhere on the board
ADDR-REG-ID3: IC38.13 (B); also elsewhere on the board
GND: IC31.7 (GND), IC32.8 (GND), IC33.8 (GND), IC38.8 (GND), IC40.7 (GND); also elsewhere on the board
unnamed: IC31.3 (O), IC32.1 (G)
unnamed: IC31.6 (O), IC32.15 (G)
unnamed: IC32.5 (Y1), J1.3
unnamed: IC38.15 (G), IC40.3 (O)
unnamed: IC32.6 (Y2), J1.5
unnamed: IC32.7 (Y3), J1.7
unnamed: IC32.11 (Y1), J2.3
unnamed: IC32.10 (Y2), J2.5
unnamed: IC32.9 (Y3), J2.7
unnamed: IC38.11 (Y1), J3.3
unnamed: IC38.10 (Y2), J3.5
unnamed: IC38.9 (Y3), J3.7
REG-LD-ID0: IC33.14 (A); also elsewhere on the board
REG-LD-ID1: IC33.13 (B); also elsewhere on the board
REG-LD-ID2: IC32.14 (A); also elsewhere on the board
REG-LD-ID3: IC32.13 (B); also elsewhere on the board
REG-RD-ID0: IC33.2 (A); also elsewhere on the board
REG-RD-ID1: IC33.3 (B); also elsewhere on the board
REG-RD-ID2: IC32.2 (A); also elsewhere on the board
REG-RD-ID3: IC32.3 (B); also elsewhere on the board
VCC: IC31.14 (VCC), IC32.16 (VCC), IC33.16 (VCC), IC38.16 (VCC), IC40.14 (VCC); also elsewhere on the board

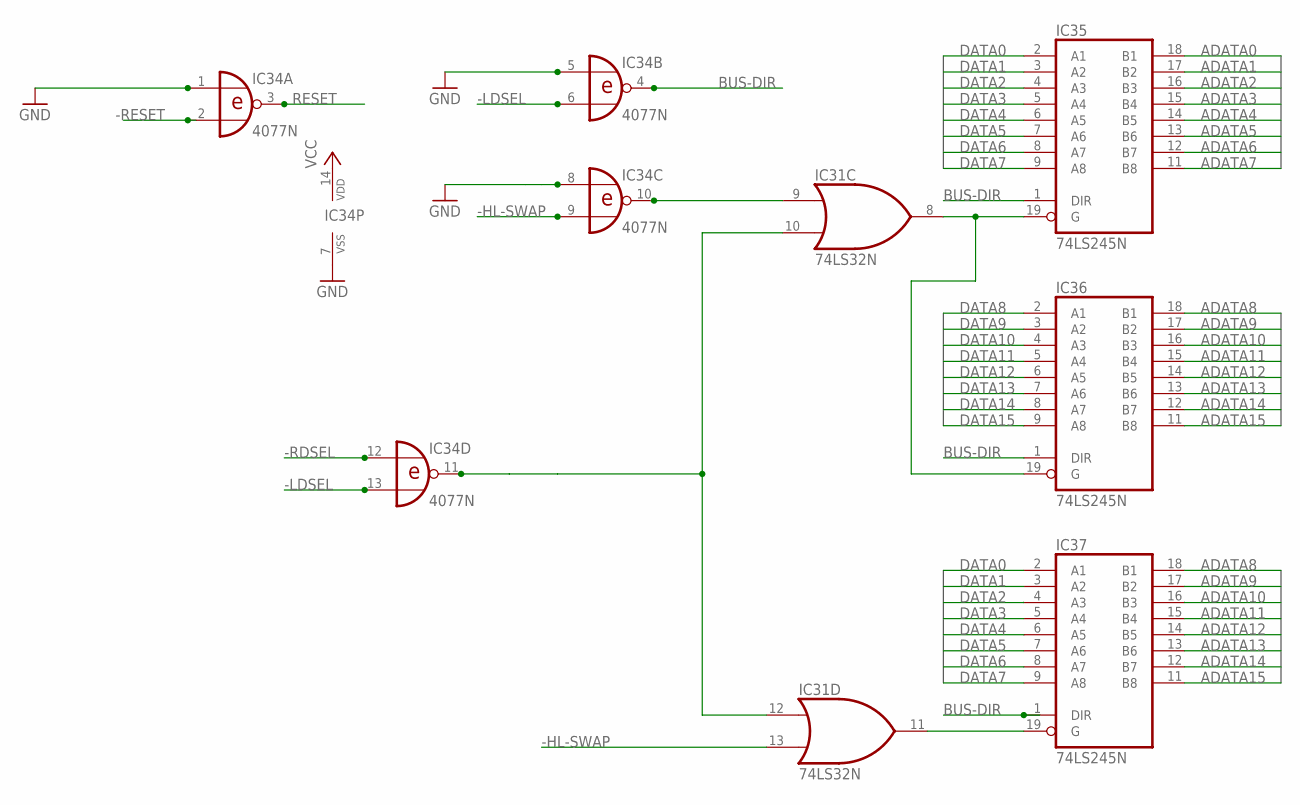
[picture p141: schematic Index Registers - 1.1.sch, sheet 7, bus buffering]

Parts:
IC31: 74LS32N; DIL14
IC34: 4077N; DIL14
IC35, IC36, IC37: 74LS245N; DIL20

Connections:
-HL-SWAP: IC31.13 (I1), IC34.9 (I1); also elsewhere on the board
-LDSEL: IC34.6 (I1), IC34.13 (I1); also elsewhere on the board
-RDSEL: IC34.12 (I0); also elsewhere on the board
-RESET: IC34.2 (I1); also elsewhere on the board
ADATA0: IC35.18 (B1); also elsewhere on the board
ADATA1: IC35.17 (B2); also elsewhere on the board
ADATA2: IC35.16 (B3); also elsewhere on the board
ADATA3: IC35.15 (B4); also elsewhere on the board
ADATA4: IC35.14 (B5); also elsewhere on the board
ADATA5: IC35.13 (B6); also elsewhere on the board
ADATA6: IC35.12 (B7); also elsewhere on the board
ADATA7: IC35.11 (B8); also elsewhere on the board
ADATA8: IC36.18 (B1), IC37.18 (B1); also elsewhere on the board
ADATA9: IC36.17 (B2), IC37.17 (B2); also elsewhere on the board
ADATA10: IC36.16 (B3), IC37.16 (B3); also elsewhere on the board
ADATA11: IC36.15 (B4), IC37.15 (B4); also elsewhere on the board
ADATA12: IC36.14 (B5), IC37.14 (B5); also elsewhere on the board
ADATA13: IC36.13 (B6), IC37.13 (B6); also elsewhere on the board
ADATA14: IC36.12 (B7), IC37.12 (B7); also elsewhere on the board
ADATA15: IC36.11 (B8), IC37.11 (B8); also elsewhere on the board
BUS-DIR: IC34.4 (O), IC35.1 (DIR), IC36.1 (DIR), IC37.1 (DIR)
DATA0: IC35.2 (A1), IC37.2 (A1); also elsewhere on the board
DATA1: IC35.3 (A2), IC37.3 (A2); also elsewhere on the board
DATA2: IC35.4 (A3), IC37.4 (A3); also elsewhere on the board
DATA3: IC35.5 (A4), IC37.5 (A4); also elsewhere on the board
DATA4: IC35.6 (A5), IC37.6 (A5); also elsewhere on the board
DATA5: IC35.7 (A6), IC37.7 (A6); also elsewhere on the board
DATA6: IC35.8 (A7), IC37.8 (A7); also elsewhere on the board
DATA7: IC35.9 (A8), IC37.9 (A8); also elsewhere on the board
DATA8: IC36.2 (A1); also elsewhere on the board
DATA9: IC36.3 (A2); also elsewhere on the board
DATA10: IC36.4 (A3); also elsewhere on the board
DATA11: IC36.5 (A4); also elsewhere on the board
DATA12: IC36.6 (A5); also elsewhere on the board
DATA13: IC36.7 (A6); also elsewhere on the board
DATA14: IC36.8 (A7); also elsewhere on the board
DATA15: IC36.9 (A8); also elsewhere on the board
GND: IC31.7 (GND), IC34.1 (I0), IC34.5 (I0), IC34.7 (VSS), IC34.8 (I0), IC35.10 (GND), IC36.10 (GND), IC37.10 (GND); also elsewhere on the board
unnamed: IC31.8 (O), IC35.19 (G), IC36.19 (G)
unnamed: IC31.11 (O), IC37.19 (G)
unnamed: IC31.9 (I0), IC34.10 (O)
unnamed: IC31.10 (I1), IC31.12 (I0), IC34.11 (O)
RESET: IC34.3 (O); also elsewhere on the board
VCC: IC31.14 (VCC), IC34.14 (VDD), IC35.20 (VCC), IC36.20 (VCC), IC37.20 (VCC); also elsewhere on the board

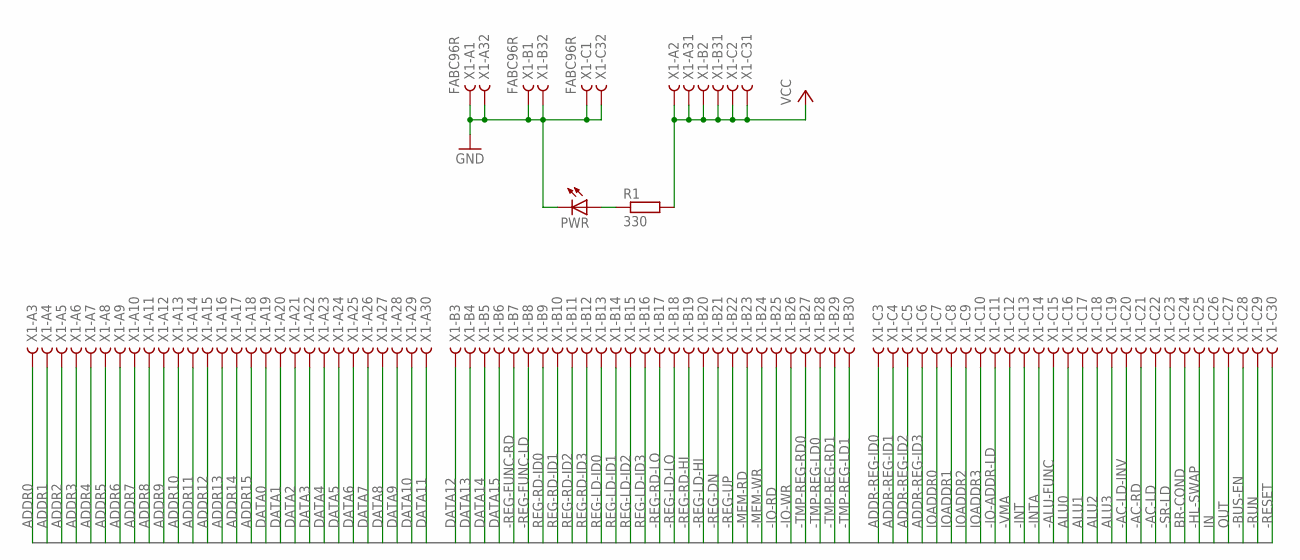
[picture p142: schematic Index Registers - 1.1.sch, sheet 8, BUS]

Parts:
PWR: LED5MM
R1: 330; 0207/10
X1: FABC96R

Connections:
-AC-LD: X1.C22
-AC-LD-INV: X1.C20
-AC-RD: X1.C21
-ALU-FUNC: X1.C15
-BUS-EN: X1.C28; also elsewhere on the board
-HL-SWAP: X1.C25; also elsewhere on the board
-INT: X1.C13
-INTA: X1.C14
-IO-ADDR-LD: X1.C11
-IO-RD: X1.B25
-IO-WR: X1.B26
-MEM-RD: X1.B23
-MEM-WR: X1.B24
-REG-DN: X1.B21; also elsewhere on the board
-REG-FUNC-LD: X1.B8; also elsewhere on the board
-REG-FUNC-RD: X1.B7; also elsewhere on the board
-REG-LD-HI: X1.B20; also elsewhere on the board
-REG-LD-LO: X1.B18; also elsewhere on the board
-REG-RD-HI: X1.B19; also elsewhere on the board
-REG-RD-LO: X1.B17; also elsewhere on the board
-REG-UP: X1.B22; also elsewhere on the board
-RESET: X1.C30; also elsewhere on the board
-RUN: X1.C29
-SR-LD: X1.C23
-TMP-REG-LD0: X1.B28
-TMP-REG-LD1: X1.B30
-TMP-REG-RD0: X1.B27
-TMP-REG-RD1: X1.B29
-VMA: X1.C12; also elsewhere on the board
ADDR0: X1.A3; also elsewhere on the board
ADDR1: X1.A4; also elsewhere on the board
ADDR2: X1.A5; also elsewhere on the board
ADDR3: X1.A6; also elsewhere on the board
ADDR4: X1.A7; also elsewhere on the board
ADDR5: X1.A8; also elsewhere on the board
ADDR6: X1.A9; also elsewhere on the board
ADDR7: X1.A10; also elsewhere on the board
ADDR8: X1.A11; also elsewhere on the board
ADDR9: X1.A12; also elsewhere on the board
ADDR10: X1.A13; also elsewhere on the board
ADDR11: X1.A14; also elsewhere on the board
ADDR12: X1.A15; also elsewhere on the board
ADDR13: X1.A16; also elsewhere on the board
ADDR14: X1.A17; also elsewhere on the board
ADDR15: X1.A18; also elsewhere on the board
ADDR-REG-ID0: X1.C3; also elsewhere on the board
ADDR-REG-ID1: X1.C4; also elsewhere on the board
ADDR-REG-ID2: X1.C5; also elsewhere on the board
ADDR-REG-ID3: X1.C6; also elsewhere on the board
ALU0: X1.C16
ALU1: X1.C17
ALU2: X1.C18
ALU3: X1.C19
BR-COND: X1.C24
DATA0: X1.A19; also elsewhere on the board
DATA1: X1.A20; also elsewhere on the board
DATA2: X1.A21; also elsewhere on the board
DATA3: X1.A22; also elsewhere on the board
DATA4: X1.A23; also elsewhere on the board
DATA5: X1.A24; also elsewhere on the board
DATA6: X1.A25; also elsewhere on the board
DATA7: X1.A26; also elsewhere on the board
DATA8: X1.A27; also elsewhere on the board
DATA9: X1.A28; also elsewhere on the board
DATA10: X1.A29; also elsewhere on the board
DATA11: X1.A30; also elsewhere on the board
DATA12: X1.B3; also elsewhere on the board
DATA13: X1.B4; also elsewhere on the board
DATA14: X1.B5; also elsewhere on the board
DATA15: X1.B6; also elsewhere on the board
GND: PWR.K (C), X1.A1, X1.A32, X1.B1, X1.B32, X1.C1, X1.C32; also elsewhere on the board
IN: X1.C26
IOADDR0: X1.C7
IOADDR1: X1.C8
IOADDR2: X1.C9
IOADDR3: X1.C10
unnamed: PWR.A, R1.1
OUT: X1.C27
REG-LD-ID0: X1.B13; also elsewhere on the board
REG-LD-ID1: X1.B14; also elsewhere on the board
REG-LD-ID2: X1.B15; also elsewhere on the board
REG-LD-ID3: X1.B16; also elsewhere on the board
REG-RD-ID0: X1.B9; also elsewhere on the board
REG-RD-ID1: X1.B10; also elsewhere on the board
REG-RD-ID2: X1.B11; also elsewhere on the board
REG-RD-ID3: X1.B12; also elsewhere on the board
VCC: R1.2, X1.A2, X1.A31, X1.B2, X1.B31, X1.C2, X1.C31; also elsewhere on the board

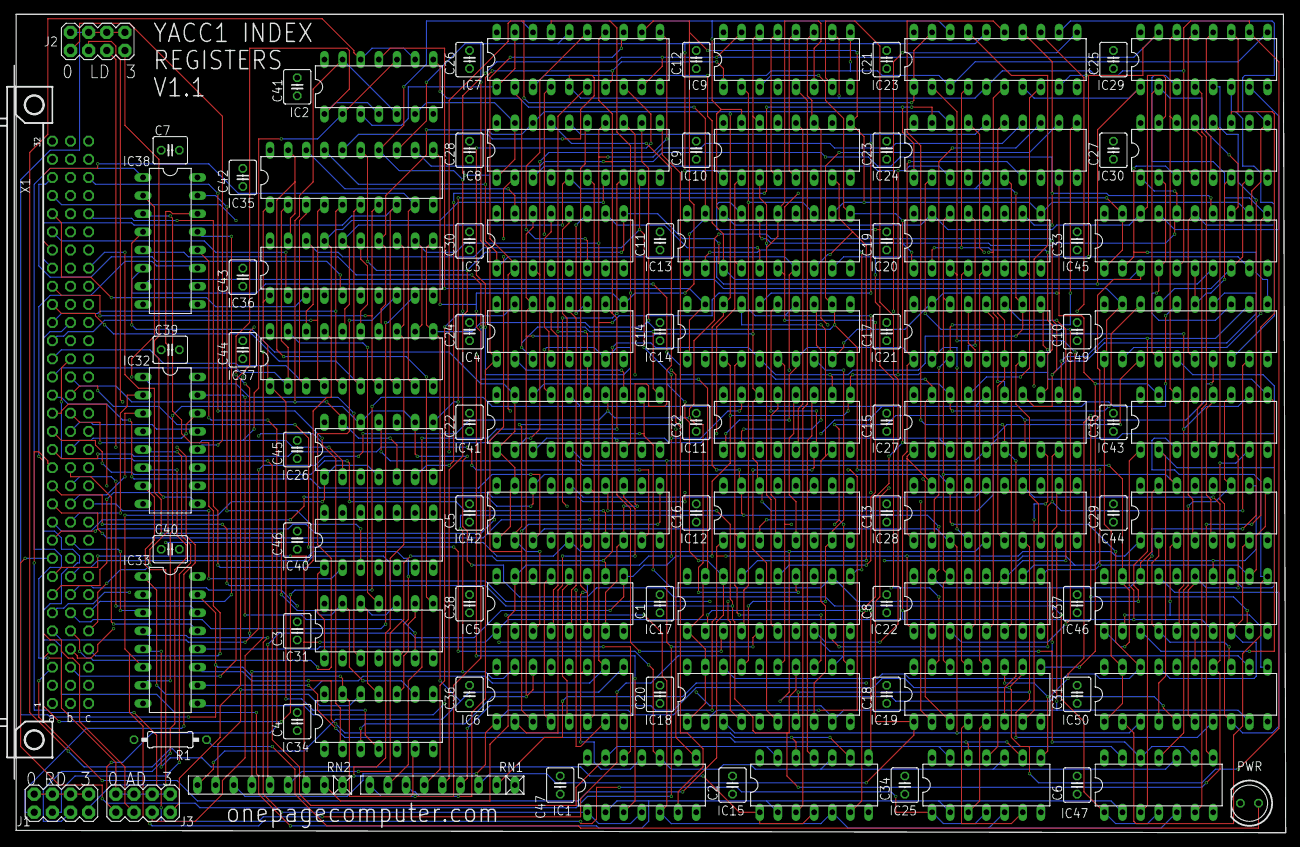
[picture p143: board Index Registers - 1.1.brd from above]

Board: 4 copper layers, 177.8 x 114.6 mm, 102 parts (0 on the bottom side), 223 nets.
