ksr/YACC1-2020/Software/Bus Test Card/Command sender/tests/Memory Card Tests/dump mem test low hi and eprom.txt

// SAMPLE COMMENT
// BASIC TEST
-RESET:1#
-RESET:0#
-VMA:1#
ADDRBUS-WR-MODE:1#
WR-ADDRBUS:FFFF#
WR-ADDRBUS:0000#
DATABUS-RD-MODE:1#
//dump low ram
DUMP:0000-000F#
//dump hi ram
DUMP:8000-800F
//dump eprom
DUMP:F000-F00F
