ksr/YACC1-2020/Software/Bus Test Card/Command sender/tests/Memory Card Tests/dump-eprom.txt

// SAMPLE COMMENT
// BASIC TEST
//Dump EPROM at 0xF000
-RESET:1#
-RESET:0#
-VMA:1#
DATABUS-RD-MODE:1#
DUMP:F000-F04F
DUMP:0000-004F
