ksr/YACC1-2020/Software/Assembler/yacc1test.asm

;
; Hardware info
UARTA0:       EQU 000h
UARTA1:       EQU 008h
UARTA2:       EQU 010h
UARTA3:       EQU 018h
UARTA4:       EQU 020h
UARTA5:       EQU 028h
UARTA6:       EQU 030h
UARTA7:       EQU 038h

SWITCHLED:    EQU 001H
LCDENABLE:    EQU 002H
LCDREGISTER:  EQU 004H
UARTCS:       EQU 040H
TIL311:       EQU 080H

CNTL-PORT:    EQU "P0"
DATAPORT:     EQU "P1"

;
; Basic interpreter tokens
;
TOKENIZER_ERROR: EQU 00
TOKENIZER_EOF: EQU 01
TOKENIZER_NUMBER: EQU 02
TOKENIZER_STRING: EQU 03
TOKENIZER_VARIABLE: EQU 04
TOKENIZER_LET: EQU 05
TOKENIZER_PRINT: EQU 06
TOKENIZER_IF: EQU 07
TOKENIZER_THEN: EQU 08
TOKENIZER_ELSE: EQU 09
TOKENIZER_FOR: EQU 10
TOKENIZER_TO: EQU 11
TOKENIZER_NEXT: EQU 12
TOKENIZER_GOTO: EQU 13
TOKENIZER_GOSUB: EQU 14
TOKENIZER_RETURN: EQU 15
TOKENIZER_CALL: EQU 16
TOKENIZER_REM: EQU 17
TOKENIZER_PEEK: EQU 18
TOKENIZER_POKE: EQU 19
TOKENIZER_END: EQU 20
TOKENIZER_COMMA: EQU 21
TOKENIZER_SEMICOLON: EQU 22
TOKENIZER_PLUS: EQU 23
TOKENIZER_MINUS: EQU 24
TOKENIZER_AND: EQU 25
TOKENIZER_OR: EQU 26
TOKENIZER_ASTR: EQU 27
TOKENIZER_SLASH: EQU 28
TOKENIZER_MOD: EQU 29
TOKENIZER_HASH: EQU 30
TOKENIZER_LEFTP: EQU 31
TOKENIZER_RIGHTP: EQU 32
TOKENIZER_LT: EQU 33
TOKENIZER_GT: EQU 34
TOKENIZER_EQ: EQU 35
TOKENIZER_CR: EQU 36
TOKENIZER_LINENUM: EQU 37

;
; MONITOR MODES
;
NOMODE:       EQU 0
EXAMINEMODE:  EQU 1
DUMPMODE:     EQU 2
BLOCKMODE:    EQU 3
FILLMODE:     EQU 4

;
; Setup Stack, use R1
;
STACK: EQU 0FFFh

;
; remap eprom from 0x0000 to 0xf000 by initial access to 0xf003 via BRanch
;
         ORG 0f000h
         BR eprom
         ORG 0f003h
eprom:
;
; Setup Stack
;
         MVIW R1,STACK

;
; BASIC interpreter user variables area
; currently 26 1-byte variables
; for now must be 0xAA00 (256 byte) aligned
;
BASIC_VARS: EQU 0100h

;
; Basic interpreter internal variables
;
emu_mode: EQU 01f0H
;
bas_ended: EQU 0200h

;
; for next statement stack ptr and stack data
;
; for next stack data
; format
;   2 bytes for variable id (only first byte used for now)
;   2 bytes to value (upper value) (format HL) (only first byte used for now)
;   2 bytes ptr to line after for instruction (format HL)
; later add step amount
;
bas_forstackptr: EQU 0202h
bas_forstack: EQU 0204h

;
; gosub stack ptr and data
;
; gosub STACK
; format
;   2 bytes return location ptr
;
bas_gosubptr: EQU 0240h
bas_gosubstack: EQU 0242h

;
; Basic interpreter text line buffer
;
parse_input_line: EQU 300h
parse_token_buffer: EQU 400h

;
; basic interpreter, add IO and peek/poke
;

;
; SERIAL OUT SETUP
;
         OUTI  P0,(UARTA3!UARTCS)
         OUTI  P1,080H

         OUTI  P0,(UARTA0!UARTCS)
         OUTI  P1,12

         OUTI  P0,(UARTA1!UARTCS)
         OUTI  P1,00

         OUTI  P0,(UARTA3!UARTCS)
         OUTI  P1,03H

; Set intial monitor mode

         MVIB R6,NOMODE
;
; Main
;
          JSR lblink
          MVIW R2,hello
          JSR stringout
;
; additional proof of life
;
; show first 16 bytes of ROM & REGISTERS
;
         MVIW R3,0f000h
         JSR showaddr
         JSR show16
         JSR showregs
         MVIW R2,CRLF
         JSR stringout
;
; show test code addr to use with go command
;
         MVIW R3,tttt
         JSR showaddr
         MVIW R2,CRLF
         JSR stringout
;
; if INPUT high start the monitor
;
         BRINH cmdloop
;
; else run test/code below at completetion blink OUT LED forever
;
tttt:
        MVIW R2,TESTMSG
        JSR stringout

        jsr add16tests

        mviw r4,0FFFAh
        mviw r5,0002h
        jsr mul16

        LDAI 5
        MVIW R2,nblink
        JSRUR R2

        halt

mul16:
;
; Multiple numbers in R4 and R5
;
; R4 = product accumulator
; R6 = Bit counter
;
        MVIW R7,0
        MVIW R6,10h
        jsr showregs

mulloop:
        jsr showregs

        mvrla r5
        andi  01h
        brz mulskip
        jsr muladd16
mulskip:
;
; clear carry flag HACK
;
        addi 0
;
        mvrla r4
        cshl
        mvarl r4
        mvrha r4
        cshl
        mvarh r4

        addi 0
        mvrha r5
        cshr
        mvarh r5
        mvrla r5
        cshr
        mvarl r5

        decr r6
        mvrla r6
        brnz mulloop
        ret

muladd16:

        MVRLA R7
        MVAT
        mvrla r4
        ADDT
        mvarl r7

        mvrha r7
        MVAT
        mvrha r4
        addtc
        mvarh r7
        ret

alltests:
;         jsr shltest
;         JSR shrtest
;         jsr rshltest
;         jsr rshrtest
;         jsr cshltest
;         JSR cshrtest
;         JSR pshltest
;         JSR additest
;         JSR addictest
;         JSR subtest
;         JSR cmptest
;         JSR shrtest
;         JSR shltest
;         JSR rshrtest
;         JSR rshltest
;         JSR cshltest
;         JSR cshrtest
;         JSR accumtest
;         JSR pushpoptest
;         JSR ortest
;         JSR orttest
;         JSR additest
;         JSR movrrtest
;         JSR add16tests

testsdone:
          JSR lblink
          BR testsdone

;
; Individual Tests
;

;
; 16 bit add carry tests
;
add16tests:
;
; add r4 and r5
;

      mviw r4,0FFFAh
      mviw r5,0FFFCh
      jsr showregs
      jsr do_add16
      jsr showregs

      mviw r4,05689h
      mviw r5,0abcdh
      jsr showregs
      jsr do_add16
      jsr showregs

      mviw r4,0FFFAh
      mviw r5,0FFFEh
      jsr showregs
      jsr do_add16
      jsr showregs
      ret


do_add16:
      MVRLA R4
      MVAT
      mvrla r5
      ADDT
      mvarl r4
      mvrha r4
      MVAT
      mvrha r5
      addtc
      mvarh r4
      ret
;
; pushr popr test
;
         MVIW R3,0ff0h
         movrr r1,r5
         JSR showaddr
         JSR show16
         JSR showregs
         MVIW R2,CRLF
         JSR stringout

         mviw r6,01234h
         movrr r1,r5
         MVIW R3,0ff0h
         JSR showaddr
         JSR show16
         JSR showregs
         MVIW R2,CRLF
         JSR stringout

         pushr r6
         movrr r1,r5
         MVIW R3,0ff0h
         JSR showaddr
         JSR show16
         JSR showregs
         MVIW R2,CRLF
         JSR stringout

         mviw r6,0h
         movrr r1,r5
         MVIW R3,0ff0h
         JSR showaddr
         JSR show16
         JSR showregs
         MVIW R2,CRLF
         JSR stringout

         popr r6
         movrr r1,r5
         MVIW R3,0ff0h
         JSR showaddr
         JSR show16
         JSR showregs
         MVIW R2,CRLF
         JSR stringout
         ret

;
; Register to Register move test
;
movrrtest:
        MVIW   R2,MOVRRHELP
        JSR    stringout

        MVIW R3,1234h
        MVIW R8,5678h

        jsr showreg38

        MOVRR R3,R8

        jsr showreg38

        MVIW R3,4321h

        jsr showreg38

        MVIW R2,1234h
        MVIW R9,5678h

        jsr showreg29

        MOVRR R2,R9

        jsr showreg29


        MVIW R2,4321h

        jsr showreg29

        ret

;
; sho registers (hard coded)
;
showreg23:
        LDAI 0h
        JSR ledout
        MVRHA r2
        JSR TIL311out
        JSR switchtoggle
        LDAI 1h
        JSR ledout
        MVRLA r2
        JSR TIL311out
        JSR switchtoggle
        LDAI 2h
        JSR ledout
        MVRHA r3
        JSR TIL311out
        JSR switchtoggle
        LDAI 3h
        JSR ledout
        MVRLA r3
        JSR TIL311out
        JSR switchtoggle
        ret

showreg34:
        LDAI 0h
        JSR ledout
        MVRHA r3
        JSR TIL311out
        JSR switchtoggle
        LDAI 1h
        JSR ledout
        MVRLA r3
        JSR TIL311out
        JSR switchtoggle
        LDAI 2h
        JSR ledout
        MVRHA r4
        JSR TIL311out
        JSR switchtoggle
        LDAI 3h
        JSR ledout
        MVRLA r4
        JSR TIL311out
        JSR switchtoggle
        ret

showreg38:
        LDAI 0h
        JSR ledout
        MVRHA r3
        JSR TIL311out
        JSR switchtoggle
        LDAI 1h
        JSR ledout
        MVRLA r3
        JSR TIL311out
        JSR switchtoggle
        LDAI 2h
        JSR ledout
        MVRHA r8
        JSR TIL311out
        JSR switchtoggle
        LDAI 3h
        JSR ledout
        MVRLA r8
        JSR TIL311out
        JSR switchtoggle
        ret
showreg29:
        LDAI 0h
        JSR ledout
        MVRHA r2
        JSR TIL311out
        JSR switchtoggle
        LDAI 1h
        JSR ledout
        MVRLA r2
        JSR TIL311out
        JSR switchtoggle
        LDAI 2h
        JSR ledout
        MVRHA r9
        JSR TIL311out
        JSR switchtoggle
        LDAI 3h
        JSR ledout
        MVRLA r9
        JSR TIL311out
        JSR switchtoggle
        ret
;
; OR - OR accumulator immediate
;
ORHELP: DB "OR tests - or input switches with 0x55 (5x)",0ah,0dh,0
ortest:
         MVIW   R2,ORHELP
         JSR    stringout
         MVIB   R2,5
orloop:
         JSR switchtoggle
         OUTI P0,(SWITCHLED)
         INP P1
         ORI  055H
         OUTA  P1

         DECR R2
         MVRLA R2
         BRNZ orloop
         RET

;
; ADDI - ADD accumulator with immediate
;
additest:
       MVIW   R2,ADDIHELP
       JSR    stringout
       MVIB   R2,5
addiloop:
       JSR switchtoggle
       OUTI P0,(SWITCHLED)
       INP P1
       ADDI 02h
       OUTA  P1

       DECR R2
       MVRLA R2
       BRNZ addiloop
       RET

;
; ADDIC - ADD accumulator with immediate with carry
;
addictest:
      MVIW   R2,ADDICHELP
      JSR    stringout
      MVIB   R2,5
addicloop:
      JSR switchtoggle
      OUTI P0,(SWITCHLED)
      INP P1
      ADDIC 02h
      OUTA  P1

      DECR R2
      MVRLA R2
      BRNZ addicloop
      RET

;
; ORT - OR accumulator with tmp register
;
orttest:
        MVIW   R2,ORTHELP
        JSR    stringout
        MVIB   R2,5
ortloop:
        JSR switchtoggle
        OUTI P0,(SWITCHLED)
        INP P1
        MVAT
        JSR switchtoggle
        OUTI P0,(SWITCHLED)
        INP P1
        ORT
        OUTA  P1

        DECR R2
        MVRLA R2
        BRNZ ortloop
        RET
;
; push pop tests - push 3 values onto stack, pop 3values from stack
;
pushpoptest:
         MVIW   R2,PUSHPOPHELP
         JSR    stringout

         MVIB   R2,3
ppenterloop:
         JSR switchtoggle
         OUTI P0,(SWITCHLED)
         INP P1
         push

         DECR R2
         MVRLA R2
         BRNZ ppenterloop

         MVIB   R2,3
ppdisloop:
        JSR switchtoggle
        OUTI P0,(SWITCHLED)
        POP
        OUTA  P1
        DECR R2
        MVRLA R2
        BRNZ ppdisloop

        RET
;
; accumulator register Tests - move values between accumulator and register HI 8 bits
;                              move values between accumulator and register LO 8 bits
;
accumtest:
         MVIW   R2,accumhelp
         JSR    stringout
         MVIB   R2,10
accloop:
         JSR switchtoggle
         OUTI P0,(SWITCHLED)
         INP P1
         MVARH R3
         INCR R3
         MVRHA R3
         OUTA P1
         JSR switchtoggle
         OUTI P0,(SWITCHLED)
         INP P1
         MVARL R3
         INCR R3
         MVRLA R3
         OUTA P1

         DECR R2
         MVRLA R2
         BRNZ accloop
         RET
;
; shift tests
;
; Shift left
;
SHIFT_LEFTHELP: DB "Shift Left - shift input switches (5x)",0ah,0dh,0
shltest:
         MVIW   R2,SHIFT_LEFTHELP
         JSR    stringout
         MVIB   R2,5
shlloop:
         JSR switchtoggle
         OUTI P0,(SWITCHLED)
         INP P1
         SHL
         OUTA  P1

         DECR R2
         MVRLA R2
         BRNZ shlloop
         RET
;
; shift Right
;
SHIFT_RIGHTHELP: DB "Shift Right - shift input switches (5x)",0ah,0dh,0
shrtest:
          MVIW   R2,SHIFT_RIGHTHELP
          JSR    stringout
          MVIB   R2,5
shrloop:
          JSR switchtoggle
          OUTI P0,(SWITCHLED)
          INP P1
          SHR
          OUTA  P1

          DECR R2
          MVRLA R2
          BRNZ shrloop
          RET
;
; ring shift left
;
rshltest:
         MVIW   R2,RSHIFT_LEFTHELP
         JSR    stringout
         MVIB   R2,10
rshlloop:
         JSR switchtoggle
         OUTI P0,(SWITCHLED)
         INP P1
         RSHL
         OUTA  P1

         DECR R2
         MVRLA R2
         BRNZ rshlloop
         RET
;
; ring shift right
;
rshrtest:
          MVIW   R2,RSHIFT_RIGHTHELP
          JSR    stringout
          MVIB   R2,10
rshrloop:
          JSR switchtoggle
          OUTI P0,(SWITCHLED)
          INP P1
          RSHR
          OUTA  P1

          DECR R2
          MVRLA R2
          BRNZ rshrloop
          RET
;
; shift left and propagate sign bit
;
pshltest:
          MVIW   R2,PSHIFT_LEFTHELP
          JSR    stringout
          MVIB   R2,10
pshlloop:
          JSR switchtoggle
          OUTI P0,(SWITCHLED)
          INP P1
          PSHR
          OUTA  P1

          DECR R2
          MVRLA R2
          BRNZ pshlloop
          RET
;
; ring shift left through carry bit
;
cshltest:
          MVIW   R2,CSHIFT_LEFTHELP
          JSR    stringout
          MVIB   R2,10
cshlloop:
          JSR switchtoggle
          OUTI P0,(SWITCHLED)
          INP P1
          CSHR
          OUTA  P1

          DECR R2
          MVRLA R2
          BRNZ cshlloop
          RET
;
; ring shift right through carry bit
;
cshrtest:
          MVIW   R2,CSHIFT_RIGHTHELP
          JSR    stringout
          MVIB   R2,10
cshrloop:
          JSR switchtoggle
          OUTI P0,(SWITCHLED)
          INP P1
          CSHR
          OUTA  P1

          DECR R2
          MVRLA R2
          BRNZ cshrloop
          RET
;
; subtraction tests
;
subtest:
          MVIW   R2,SUBHELP
          JSR    stringout
          MVIB   R2,10
subloop:
          JSR switchtoggle
          OUTI P0,(SWITCHLED)
          INP P1
          SUBI  1
          OUTA  P1

          DECR R2
          MVRLA R2
          BRNZ subloop
          RET
;
; Compare Tests/compare input switches to 0x55 10 times
;
cmptest:
          MVIW   R2,COMPAREHELP
          JSR    stringout
          MVIB   R2,10
          LDTI   055H
cmploop:
          JSR switchtoggle
          OUTI P0,(SWITCHLED)
          INP P1
          BRGT OUTGT
          BREQ OUTEQ
          BRLT OUTLT
;Should not happen
          LDAI '?'
          BR cmpres
OUTGT:
          LDAI 'G'
          BR cmpres
OUTEQ:
          LDAI 'E'
          BR cmpres
OUTLT:
          LDAI 'L'
          BR cmpres

cmpres:
          JSR uartout
          DECR R2
          MVRLA R2
          BRNZ cmploop
          RET

;
; Monitor
;

; Single char
;
;
; Commands
;
; H      - Display help menu
;
; T      - Test menu
;
; B AAAA - Show 256 bytes at address AAAA (16 byte aligned)
;          followed by CR display next 256 bytes
;
; D AAAA - Show 16 bytes at address AAAA (16 byte aligned)
;          followed by CR display next 16 bytes
;
; E AAAA - show contents of location AAAA (Output AAAA:XX)
;          if followed by ASCII-HEX modify location with new value (and redisplay)
;          if followed by CR display next location
;
; F AAAA - fill block with 0
;          if followed by CR fill next location
;
; G AAAA - Jump to (and execute) starting at AAAA
;          code could end in BR to 0xf000h to restart monitor or RET if called via JSR
;
; R      - SHOW REGISTERS
;
; Z      - Basic Interpreter
;
; Output Prompt
:

cmdloop:
      MVIW R2,PROMPT
      JSR stringout

      JSR uartin
      JSR toupper
;
; added for emulator eat cr next 3 lines
;
;     push
;     JSR uartin
;     pop
      LDTI 'H'
      BRNEQ testexamine
      MVIW R2,CRLF
      JSR stringout
      MVIW R2,helpmenu
      JSR stringout
      BR cmdloop

testexamine:
      LDTI 'Z'
      BREQ cmd_basic
      LDTI 'B'
      BREQ dumpblock
      LDTI 'D'
      BREQ dump
      LDTI 'E'
      BREQ examine
      LDTI 'F'
      BREQ fillblock
      LDTI 'G'
      BREQ go
      LDTI 'L'
      BREQ cmd_basiclist
      LDTI 'R'
      BREQ dumpreg
      LDTI 'T'
      BREQ tests
      LDTI 0Dh
      BREQ continue
;
; add for emulator
;
      LDTI 0ah
      BREQ continue

      MVIW R2,CRLF

      JSR stringout

      MVIW R2,ERROR
      JSR stringout

      MVIW R2,helpmenu
      JSR stringout
      BR cmdloop
;
continue:
       MVRLA R6

       LDTI BLOCKMODE
       BREQ dumpblockcont

       LDTI DUMPMODE
       BREQ dumpcont

       LDTI EXAMINEMODE
       BREQ examinecont

       LDTI FILLMODE
       BREQ fillcont
       BR cmdloop
;
;      ERROR
;
       MVIW R2,CONTINUEERROR
       JSR stringout
       BR cmdloop

stop:   BR stop

cmd_basic:
       jsr do_basic
       BR cmdloop

cmd_basiclist:
        mviw r7,basic_test
        JSR tok_list
        BR cmdloop

dumpblock:
       MVIB R6,BLOCKMODE
       MVIW R2,DUMPBLOCKMSG
       JSR stringout
       jsr getaddress
       MVIW R2,CRLF
       JSR stringout

dumpblockcont:
       jsr show256
       BR cmdloop

dump:
       MVIB R6,DUMPMODE
       MVIW R2,DUMPMSG
       JSR stringout
       jsr getaddress
       MVIW R2,CRLF
       JSR stringout

dumpcont:
       jsr showaddr
       jsr show16
       BR cmdloop

examine:
       MVIB R6,EXAMINEMODE
       MVIW R2,EXAMINEMSG
       JSR stringout
       jsr getaddress
       MVIW R2,CRLF
       JSR stringout

examinecont:
      JSR showaddr
      JSR showbyte
      LDAI ' '
      JSR uartout

      JSR uartin
      LDTI 01bh
      BREQ examdone
      LDTI 0dh
      BREQ examnext
      JSR getnibblec
      SHL
      SHL
      SHL
      SHL
      push
      jsr getnibble
      MVAT
      Pop
      ORT
      STAVR R3

examnext:
      INCR R3
      LDAI 0ah
      JSR uartout
      LDAI 0dh
      JSR uartout
      BR examinecont
examdone:
      MVIW R2,CRLF
      JSR stringout
      BR cmdloop

fillblock:
       MVIB R6,FILLMODE
       MVIW R2,FILLMSG
       JSR stringout
       jsr getaddress
       MVIW R2,CRLF
       JSR stringout

fillcont:
      jsr showaddr
      MVIW R2,CRLF
      JSR stringout

morefill:
      LDAI 0
      STAVR R3
      INCR R3
      MVRLA R3
      ANDI  0FFH
      BRNZ morefill
      LDAI 0ah
      JSR uartout
      LDAI 0dh
      JSR uartout
      BR cmdloop


go:
      MVIW R2,GOMSG
      JSR stringout
      jsr getaddress
      BRVR R3

dumpreg:
      JSR showregs
      MVIB R6,NOMODE
      BR cmdloop

tests:
      MVIB R6,NOMODE
      MVIW R2,CRLF
      JSR stringout
      MVIW R3,testmenu
      MVIW R4,0000h

testsloop:

      INCR R3
      INCR R3
      LDAVR R3
      MVARH R2
      INCR  R3
      LDAVR R3
      MVARL R2
      INCR R3
      LDAVR R2
      LDTI '-'
      BREQ testsloopdone
      MVRLA R4
      JSR showbytea
      LDAI  '-'
      JSR uartout
      JSR stringout
      MVIW R2,CRLF
      JSR stringout
      INCR R4
      BR testsloop

testsloopdone:
; get test number
; multiple by 4 and add to test list base
; JSR via register holding info
;
      MVIW R2,gettestpromopt
      JSR stringout

      JSR getnibble
      SHL
      SHL
      SHL
      SHL
      push
      jsr getnibble
      MVAT
      Pop
      ORT
; calculate test address
      shl
      shl
      JSR TIL311out
      MVAT
      MVIW R3,testmenu
      MVRLA R3
      ADDT
      MVARL R3
      JSR TIL311out
      BRC menucarry
      BR dotest

menucarry:
      incr r3

dotest:
      LDAVR R3
      MVARH R4
      INCR  R3
      LDAVR R3
      MVARL R4
      JSRUR R4
      BR cmdloop

getaddress:
;
; Read 4 char address and return in R3
;
            Push
            JSR getnibble
            SHL
            SHL
            SHL
            SHL
            ANDI 0f0h
            Push
            JSR getnibble
            ANDI 0FH
            MVAT
            Pop
            ORT
            MVARH R3

            JSR getnibble
            SHL
            shl
            shl
            shl
            ANDI 0f0h
            push
            JSR getnibble
            ANDI 0FH
            MVAT
            pop
            ORT
            MVARL R3
            POP
            RET
;
; getnibble return in accumulator
;
getnibble:
          JSR uartin
getnibblec:
          LDTI '9'
          BRGT INAF
          SUBI '0'
          RET
INAF:     JSR toupper
          SUBI 'A'
          ADDI 10
          RET
;
; convert to uppercase
;
toupper:  LDTI 'Z'
          BRGT lower
          RET
lower:
          SUBI 020h
          RET
;
; display R3 followed by a ":" and " " for showaddr and nothing for shownum
;
showaddr:   Push
            MVRHA R3
            SHR
            SHR
            SHR
            SHR
            JSR shownibble
            MVRHA R3
            ANDI 0FH
            JSR shownibble
            MVRLA R3
            SHR
            SHR
            SHR
            SHR
            JSR shownibble
            MVRLA R3
            ANDI 0FH
            JSR shownibble
            LDAI ':'
            JSR uartout
            LDAI ' '
            JSR uartout
            POP
            RET

shownum:   Push
            MVRHA R3
            SHR
            SHR
            SHR
            SHR
            JSR shownibble
            MVRHA R3
            ANDI 0FH
            JSR shownibble
            MVRLA R3
            SHR
            SHR
            SHR
            SHR
            JSR shownibble
            MVRLA R3
            ANDI 0FH
            JSR shownibble
            POP
            RET
;
; display R7 followed by a ":" and " "
;
showr7:     Push
            MVRHA R7
            SHR
            SHR
            SHR
            SHR
            JSR shownibble
            MVRHA R7
            ANDI 0FH
            JSR shownibble
            MVRLA R7
            SHR
            SHR
            SHR
            SHR
            JSR shownibble
            MVRLA R7
            ANDI 0FH
            JSR shownibble
            POP
            RET
;
;
;
showregs:
            MVIW R2,CRLF
            JSR stringout
            MOVRR r0,r3
            jsr showaddr
            MOVRR r1,r3
            jsr showaddr
            MOVRR r2,r3
            jsr showaddr
            MOVRR r3,r3
            jsr showaddr
            MOVRR r4,r3
            jsr showaddr
            MOVRR r5,r3
            jsr showaddr
            MOVRR r6,r3
            jsr showaddr
            MOVRR r7,r3
            jsr showaddr

            MVIW R2,CRLF
            JSR stringout
            RET
;
; display upto 16 bytes point to by R3, stops on a 16 byte boundry, increments R3
;
show16:     JSR showbyte
            INCR R3
            LDAI ' '
            JSR uartout
            MVRLA R3
            ANDI 0FH
            BRNZ show16
            LDAI 0ah
            JSR uartout
            LDAI 0dh
            JSR uartout
            RET
;
; display upto 256 bytes point to by R3, stops on a 256 byte boundry, increments R3
show256:
          jsr showaddr
          jsr show16
;          MVIW R2,CRLF
;          JSR stringout
          MVRLA R3
          ANDI  0FFH
          BRNZ show256
          LDAI 0ah
          JSR uartout
          LDAI 0dh
          JSR uartout
          RET
;
; Output ASCII representation of a BYTE pointed to by R3
; or use showbytea in accumulator
; both destructive for accumulator - no longer true with push/pop?
:
showbyte:   PUSH
            LDAVR R3

            SHR
            SHR
            SHR
            SHR
            JSR shownibble
            LDAVR R3
            ANDI 0FH
            JSR shownibble
            POP
            RET
;
showbytea:  PUSH
            PUSH

            SHR
            SHR
            SHR
            SHR
            JSR shownibble
            POP
            ANDI 0FH
            JSR shownibble
            POP
            RET
;
; Display nibble in accumulator (destructive)
;
shownibble:  PUSH
             LDTI 9
             BRGT AF
             ADDI '0'
             JSR uartout
             Pop
             RET

AF:          SUBI 10
             ADDI 'A'
             JSR uartout
             Pop
             RET
;
; reading switches into accumulator
;
switchin:
        OUTI  P0,(SWITCHLED)
        INP   P1
        RET
;
;
; output accumulator to LEDS or Hex displays (non distructive)
;
ledout:
        OUTI  P0,(SWITCHLED)
        OUTA  P1
        RET
TIL311out:
        OUTI  P0,(TIL311)
        OUTA  P1
        RET
;
; Output null terminated string pointed to by R2 to UART then send CR and LF
; Advances R2 to end of string
;
stringout:
        Push
sloop:
        LDAVR R2
        BRZ sloopdone
        JSR uartout
        INCR R2
        BR sloop
;
; send CR and LF
;
sloopdone:
        POP
        RET
;
; output accumulator to UART
;
charout:
uartout:
;
; add for emulator
;
      outa p2
      ret
;
        PUSH
        push
; doubt 2nd push pop is needed, to be tested
uartoutw:
        OUTI  P0,(UARTCS!UARTA5)
        INP   p1
        ANDI  040h
;
; i think this a brnz test -- that didn't work
        BRZ   uartoutw
        POP
        OUTI  P0,UARTCS
        OUTA  P1
;
; may not be needed
       Pop
       RET

;
; OLD
;
;        MVIW R7,01FFh
;uartdelay:
;        DECR R7
;        MVRHA R7
;        BRNZ uartdelay
;        POP
;        RET
;
; input UART to accumulator
;
uartin:
;
; add for emulator
;
     inp p2
    ret
;
        OUTI  P0,(UARTCS!UARTA5)
        INP   p1
        ANDI  01h
        BRZ   uartin
        OUTI  P0,(UARTCS)
        INP   P1
        JSR uartout
        RET
;
; long delay (approx 5 seconds)
;
LONGDELAY:
        PUSH
        MVIW R7,0FFFFh
longdelayloop:
        DECR R7
        MVRHA R7
        BRNZ longdelayloop
        POP
        RET
;
; short delay (approx 1 second)
;
SHORTDELAY:
        PUSH
        MVIW R7,033FFh
shortdelayloop:
        DECR R7
        MVRHA R7
        BRNZ shortdelayloop
        POP
        RET

NODELAY:
      PUSH
      MVIW R7,00FFh
nodelayloop:
      DECR R7
      MVRHA R7
      BRNZ nodelayloop
      POP
      RET
;
; toggle input switch (with debounce)
;
switchtoggle:
        Push
offw:   BRINL offw
        MVIW R7,01FFh
delaya:
        DECR R7
        MVRHA R7
        BRNZ delaya
        ON

onw:    BRINH onw
        MVIW R7,01FFh
delayb:
        DECR R7
        MVRHA R7
        BRNZ delayb
        OFF
        Pop
        RET
;
; quick blink LED
;
blink:
;
; added for emulator
;
;        ret
        Push
        ON
        MVIW R7,03FFh
onloop:
        DECR R7
        MVRHA R7
        BRNZ onloop

        OFF
        MVIW R7,003FFh
offloop:
        DECR R7
        MVRHA R7
        BRNZ offloop
        Pop
        RET
;
; long blink LED
;
lblink:
;
; emulator change
;
;       ret
        Push
        ON
        MVIW R7,018FFh
lonloop:
        DECR R7
        MVRHA R7
        BRNZ lonloop

        OFF
        MVIW R7,018FFh
loffloop:
        DECR R7
        MVRHA R7
        BRNZ loffloop
        Pop
        RET
;
; blink n times in accumulator
;
;
; emulator change
;
;    ret
nblink:
        push
nblinkloop:
        JSR TIL311out
        BRZ nblinkdone
        JSR blink
        subi 1
        BR nblinkloop
nblinkdone:
        POP
        RET


;
; MONITOR STRINGS
;
hello:  DB 0ah,0dh,"YACC 2020: hello world  ",0ah,0dh,0
PROMPT: DB ">>",0
CRLF: DB 0ah,0dh,0
ERROR: DB "UNRECOGINIZED COMMAND",0ah,0dh,0
CONTINUEERROR: DB "CONTINUE CMD ERROR",0ah,0dh,0
DUMPMSG: DB 0ah,0dh,"DUMP ADDR:",0
DUMPBLOCKMSG: DB 0ah,0dh,"DUMP BLOCK ADDR:",0
FILLMSG: DB 0ah,0dh,"FILL BLOCK ADDR:",0
GOMSG: DB 0ah,0dh,"GO ADDRESS:",0
EXAMINEMSG: DB 0ah,0Dh,"EXAMINE ADDRESS:",0
CONTMSG: DB "CONTINUE MODE",0
gettestpromopt: DB "Enter Test number:",0
;
helpmenu:
DB "H      - Display help menu",0ah,0dh
DB "B AAAA - Show 256 bytes of memory at address AAAA (16 byte aligned)",0ah,0dh
DB "         followed by CR display next 256 bytes",0ah,0dh
DB "D AAAA - Show 16 bytes of memory at address AAAA (16 byte aligned)",0ah,0dh
DB "         followed by CR display next 16 bytes",0ah,0dh
DB "E AAAA - show contents of location AAAA (Output AAAA:XX)",0ah,0dh
DB "         if followed by ASCII-HEX modify location with new value (and redisplay)",0ah,0DH
DB "         if followed by CR display next location",0ah,0dh
DB "F AAAA   Fill contents 256 bytes of memory at address AAAA with 0(16 byte aligned) with 0",0ah,0dh
DB "         if followed by CR fill next 256 bytes",0ah,0dh
DB "G AAAA - Jump to (and execute) starting at AAAA",0ah,0dh
DB "         code could end in BR to 0xf000h to restart monitor or RET if called via JSR",0ah,0dh
DB "R      - Show registers",0ah,0dh
DB "T      - Test menu",0ah,0DH
DB "Z      - Run Basic interpreter",0ah,0DH
DB 0
;
; TEST HELP MESSAGES
;
COMPAREHELP: DB "Compare Tests",0ah,0dh,0
RSHIFT_LEFTHELP: DB "Ring Shift Left",0ah,0dh,0
RSHIFT_RIGHTHELP: DB "Ring Shift Right",0ah,0dh,0
PSHIFT_LEFTHELP: DB "PROP Shift Left",0ah,0dh,0
CSHIFT_LEFTHELP: DB "CARRY Shift Left",0ah,0dh,0
CSHIFT_RIGHTHELP: DB "CARRY Shift Right",0ah,0dh,0
SUBHELP: DB "SUBTRACT",0ah,0dh,0
accumhelp: DB "accumulator test",0ah,0dh,0
PUSHPOPHELP: DB "Push Pop enter 3 numbers",0ah,0dh,0
ORTHELP: DB "OR Tmp register tests",0ah,0dh,0
ADDIHELP: DB "Add immediate 02h to input number",0ah,0dh,0
ADDICHELP: DB "Add immediate with carry 02h to input number",0ah,0dh,0
MOVRRHELP: DB "MOVERR TEST",0ah,0dh,0
TESTMSG: DB "Run test code",0ah,0dh,0

;
; TEST MENU
;
testmenu:
      DW ortest,ormenu
      DW orttest,ortmenu
      DW pushpoptest,pushpopmenu
      DW accumtest,accummenu
      DW shltest,shlmenu
      DW shrtest,shrmenu
      DW rshltest,rshlmenu
      DW rshrtest,rshrmenu
      DW cshltest,cshlmenu
      DW cshrtest,cshrmenu
      DW pshltest,pshlmenu
      DW subtest,submenu
      DW cmptest,cmpmenu
      DW additest,addimenu
      DW addictest,addicmenu
      DW movrrtest,movrrmenu
      DW endmenu,endmenu

;
; TEST MENU STRINGS
;
testmenustrings:
ormenu: DB "OR",0
ortmenu: DB "ORT",0
pushpopmenu: DB "PUSH/POP",0
accummenu: DB "Accumulator <-> Register",0
shlmenu: DB "SHL",0
shrmenu: DB "SHR",0
rshlmenu: DB "RSHL",0
rshrmenu: DB "RSHR",0
cshlmenu: DB "CSHL",0
cshrmenu: DB "CSHR",0
pshlmenu: DB "PSHL",0
submenu: DB "SUB",0
cmpmenu: DB "Compare Branch",0
addimenu: DB "ADDI",0
addicmenu: DB "ADDI",0
movrrmenu: DB "MOVRR",0
endmenu: DB "-",0

;
; OLD
;
;
;LCD
;
;xlcdtest:
;        OUTI P0,(LCDENABLE)

;        MVIW R3,1fFFh
;xdelay0:
;        DECR R3
;        MVRHA R3
;        BRNZ xdelay0

;        OUTI P1,3CH

;        MVIW R3,1fFFh
;xdelay1:
;        DECR R3
;        MVRHA R3
;        BRNZ xdelay1

;        OUTI P1,01H

;        MVIW R3,1fFFh
;xdelay2:
;        DECR R3
;        MVRHA R3
;        BRNZ xdelay2

;        OUTI P1,0FH

;        MVIW R3,1fFFh
;xdelay3:
;        DECR R3
;        MVRHA R3
;        BRNZ xdelay3

;        OUTI P0,(LCDENABLE!LCDREGISTER)

;        MVIW R3,1fFFh
;xdelay4:
;        DECR R3
;        MVRHA R3
;        BRNZ xdelay4

;        OUTI P1,'A'

;xdelay5:
;        DECR R3
;        MVRHA R3
;        BRNZ xdelay5

;        OUTI P1,'B'

;xaddtest:
;      OUTI  P0,(SWITCHLED)
;      INP   P1
;      ADDI  001H
;      OUTA  P1

;xandtest:
;      OUTI  P0,(SWITCHLED)
;      INP   P1
;      ANDI  055H
;      OUTA  P1

;xxortest:
;     OUTI  P0,(SWITCHLED)
;     INP   P1
;     XORI  055H
;     OUTA  P1
      JSRUR R2
;
; Basic Interpreter
;
      ORG 0e000h
;
; basic interpreter messages
;
bas_msg1: db "unexpected token",0,0ah,0dh
bas_msg2: db "line not found",0,0ah,0dh
bas_msg3: db "Basic ins not found ",0ah,0dh
exe_stmt_msg: db "EXE STMT ",0
;
; Basic interpreter - execution engine
; Register Usage
; R0 - Program Counter
; R1 - Stack Pointer
; R2 - Used to send strings for output - assume destructive
; R3 - Basic Interpreter Token Buffer ptr
; R4 - working register
; R5 - working register
; R6 - Working register
; R7 - return value
;
exe:

;
; void ubasic_init()
;
; Setup basic interpreter execution engine
;
; destorys R4 and accumulator
; ?? Should these pointers be zero based or actual address in memory
;
exe_init:
    MVIW R5,bas_gosubstack
;    movrr r6,r9
    MVIW R4,bas_forstack
;    movrr r6,r8
    MVIW R6,bas_ended
    LDAI 0
    STAVR R6
;
; initialize tokenbufferptr to start of tokenBuffer (actual memory address)
;
    JSR tok_init
    RET

;
; void accept(int)
;
; compare accumulator with current token then advance to next token in buffer
; assume accumulator destroyed
;
exe_accept:
    push
;
; get current token into accumulator
;
    jsr tok_token
    MVAT
    POP
    BREQ exe_accept_done
    mviw r2,bas_msg1
    JSR bas_error
exe_accept_done:
    jsr tok_next
    RET

;
; int varfactor()
;
; get variable id pointed to by tok_variable_num in token stream
; (this is not a value but a variable id)
; value returned by exe_get_variable in r7
;
; return value in R7
;
exe_varfactor:
; get variable number id (one byte for now a-z) into accumulator
;
    jsr tok_variable_num
;
; variable id in accumulator, return in r7
;
    jsr exe_get_variable
    LDAI TOKENIZER_VARIABLE
    JSR exe_accept
    RET

;
; int factor()
; return value in R7
;
exe_factor:
;
; get current token into accumulator
;
    jsr tok_token
;
    LDTI TOKENIZER_NUMBER
    BRNEQ exe_factor1
    JSR tok_num
    MVTA
    JSR exe_accept
    RET

exe_factor1:
    LDTI TOKENIZER_LEFTP
    BRNEQ exe_factor2
    JSR exe_accept
    JSR exe_expr
    LDAI TOKENIZER_RIGHTP
    JSR exe_accept
    RET

exe_factor2:
    jsr exe_varfactor
    ret

;
; int term()
; R5 = F1
; R6 = F2
; R7 = return value
;
exe_term:
    pushr r5
    pushr r6

    jsr exe_factor
    MOVRR r7,r5

exe_term_loop:
    jsr tok_token
    ldti TOKENIZER_ASTR
    BREQ exe_term_astr
    LDTI TOKENIZER_SLASH
    breq exe_term_slash
    ldti TOKENIZER_MOD
    breq exe_term_mod
    br exe_term_done

exe_term_astr:
    jsr tok_next
    jsr exe_factor
    movrr r7,r6
;
; do mulitply f1 = f1 * f2
;
    BR exe_term_loop

exe_term_slash:
    jsr tok_next
    jsr exe_factor
    movrr r7,r6
;
; do divide f1 = f1 / f2
;
    BR exe_term_loop

exe_term_mod:
    jsr tok_next
    jsr exe_factor
    movrr r7,r6
;
; f1 = f1 % f2
;
    BR exe_term_loop

exe_term_done:
    MOVRR r5,r7
    popr r6
    popr r5
    ret
;
; static VARIABLE_TYPE expr()
;
; R5 = t1
; R6 = t2
; R7 = return value
;
exe_expr:
    pushr r5
    pushr r6

    jsr exe_term
    MOVRR r7,r5

exe_expr_loop:
    jsr tok_token
    ldtI TOKENIZER_PLUS
    BREQ exe_expr_plus
    ldtI TOKENIZER_MINUS
    breq exe_expr_minus
    ldtI TOKENIZER_AND
    breq exe_expr_and
    ldti TOKENIZER_OR
    breq exe_expr_or

    br exe_expr_done

exe_expr_plus:
    jsr tok_next
    jsr exe_term
    movrr r7,r6
;
; t1 = t1 + t2
;
    BR exe_expr_loop

exe_expr_minus:
    jsr tok_next
    jsr exe_term
    movrr r7,r6
;
; t1 = t1 - t2
;
    BR exe_expr_loop

exe_expr_and:
    jsr tok_next
    jsr exe_term
    movrr r7,r6
;
; t1 = t1 & t2
;
    BR exe_expr_loop

exe_expr_or:
    jsr tok_next
    jsr exe_term
    movrr r7,r6
;
; t1 = t1 | t2
;
    BR exe_expr_loop

exe_expr_done:
    MOVRR r5,r7
    popr r6
    popr r5
    ret
;
; int relation ()
;
; R5 = r1
; R6 = r2
; R7 = return value
;

exe_relation:
    pushr r5
    pushr r6

    jsr exe_expr
    MOVRR r7,r5

exe_relation_loop:
    jsr tok_token
    LDTI TOKENIZER_LT
    BREQ exe_relation_lt
    ldti TOKENIZER_GT
    breq exe_relation_gt
    ldti TOKENIZER_EQ
    breq exe_relation_eq

    br exe_relation_done

exe_relation_lt:
    jsr tok_next
    jsr exe_expr
    movrr r7,r6
;
; r1 = r1 < r2
;
    BR exe_relation_loop

exe_relation_gt:
    jsr tok_next
    jsr exe_expr
    movrr r7,r6
;
; r1 = r1 > r2
;

    BR exe_relation_loop

exe_relation_eq:
    jsr tok_next
    jsr exe_expr
    movrr r7,r6
;
; r1 = r1 == r2
;
    BR exe_relation_loop

exe_relation_done:
    MOVRR r5,r7
    popr r6
    popr r5
    ret

;
; char * index_find (int linenum)
;
; call with line in R7
; return with val in R7 - tokenbuffer ptr
;
exe_index_find:
    JSR tok_find
    RET
;
; void jump_linenum(linenum)
;
; Linenum in R7
;
exe_jump_line:
    JSR exe_index_find
    MVRHA R7
    BRNZ exe_jump_line1
    MVRLA R7
    BRNZ exe_jump_line1
;
; returned 0 line not found
;
    LDAI TOKENIZER_CR
    JSR exe_accept
    MVIW r6,bas_ended
    LDAI 1
    STAVR R6
    ret
exe_jump_line1:
    jsr tok_goto
    ret
;
; void goto_statement()
;
exe_goto_stmt:
    LDAI TOKENIZER_GOTO
    JSR exe_accept
    JSR exe_expr
    JSR exe_jump_line
    RET
;
; void print_statment()
;
exe_print_stmt:
    LDAI TOKENIZER_PRINT
    jsr exe_accept

exe_print_stmt_loop:
    jsr tok_token
    LDTI TOKENIZER_STRING
    BRNEQ exe_print_stmt1
;
; this should return string to print in r2
; tok_string may not be needed tokenbufferptr is at string ?
;
    jsr tok_string
    movrr r7,r2
    jsr stringout
    jsr tok_next
    br exe_print_stmt_test

exe_print_stmt1:

    ldti TOKENIZER_COMMA
    BRNEQ exe_print_stmt2
    LDAI ' '
    JSR charout
    jsr tok_next
    br exe_print_stmt_test

exe_print_stmt2:
    ldti TOKENIZER_SEMICOLON
    BRNEQ exe_print_stmt3
    jsr tok_next
    br exe_print_stmt_test

exe_print_stmt3:
    ldti TOKENIZER_VARIABLE
    BREQ exe_print_stmt4
    ldti TOKENIZER_NUMBER
    breq exe_print_stmt4
    ldti  TOKENIZER_LEFTP
    breq exe_print_stmt4

    br exe_print_stmt_done

exe_print_stmt4:
    jsr exe_expr
    JSR showr7
;   br exe_print_stmt_test // falls through

exe_print_stmt_test:
    jsr tok_token
    LDTI TOKENIZER_CR
    breq exe_print_stmt_done
    LDTI TOKENIZER_EOF
    breq exe_print_stmt_done
    br exe_print_stmt_loop

exe_print_stmt_done:
    mviw R2,CRLF
    jsr stringout
    jsr tok_next
    ret

;
; void if_statement()
;
exe_if_stmt:
    halt
    LDAI TOKENIZER_IF
    JSR exe_accept

    JSR exe_relation
    LDAI TOKENIZER_THEN
    JSR exe_accept
    LDTI 1
    BRNEQ exe_if_stmt1
    JSR exe_stmt
exe_if_stmt1:
    jsr TOKENIZER_NEXT
;    ////////

;
; void let_statement()
;
exe_let_stmt:
  jsr tok_variable_num
  mvarl r7
  movrr r7,r6
  ldai TOKENIZER_VARIABLE
  jsr exe_accept
  ldai TOKENIZER_EQ
  jsr exe_accept
  jsr exe_expr
  mvrla r6
  JSR exe_set_variable
  ldai TOKENIZER_CR
  jsr exe_accept
  ret

;
; void gosub_statement()
;
exe_gosub_stmt:
    ldai TOKENIZER_GOSUB
    jsr exe_accept
    jsr tok_num
    ldai TOKENIZER_NUMBER
    jsr exe_accept
    ldai TOKENIZER_CR
    jsr exe_accept
;
; setup to use for storage area via R4
;
;   movrr R9,R4
;
; save current token buffer ptr to gosub stack
;
   mvrla r3
   stavr r5
   incr r5
   mvrha r3
   stavr r5
   incr  r5
;
; write new gosub stack ptr location back
;
;   MOVRR R4,R9

   JSR exe_jump_line
   RET

;
; void return_statment()
;
exe_return_stmt:
    ldai TOKENIZER_RETURN
    jsr exe_accept
;
; setup to use for storage area via R4
;
;   movrr R9,R4

   decr r5
   decr r5

   ldavr r5
   mvarl r3
   incr r5
   ldavr r5
   mvarh r3

   decr r5
;   movrr r4,r9

   ret

;
; void next_statement()
;
exe_next_stmt:
;
; setup to use for storage area via R4
;
;    movrr r8,r4
; backup to the TO Value
    decr r4
    decr r4
    decr r4
    decr r4
;
; eat next
;
    ldai TOKENIZER_NEXT
    jsr exe_accept
;
; get variable id (in accumulator) and hold in r6 lo
;
    jsr tok_variable_num
    mvarl r6
;
; eat TOKENIZER_VARIABLE id
;
    ldai TOKENIZER_VARIABLE
    jsr exe_accept
;
; get variable value, inc by 1 and store
;
    mvrla r6
    jsr exe_get_variable
    incr r7
    mvrla r6
    jsr exe_set_variable
;
; get TO value into R6
    ldavr r4
    mvarl r6
    incr r4
    ldavr r4
    mvarh r6
    incr r4
;
; for now only compare low byte hack
;
    mvrla r6
    mvat
    mvrla r7
    brgt exe_next_done
;
    ldavr r4
    mvarl r3
    incr r4
    ldavr r4
    mvarh r3
    incr r4
    ret

exe_next_done:
  decr r4
  decr r4
  decr r4
  decr r4
  decr r4
  decr r4
;  movrr r4,r8
  ldai TOKENIZER_CR
  jsr exe_accept
  ret

;
; void for_statement()
;
exe_for_stmt:
;
; setup to use for storage area via R4
;
;    movrr r8,r4
;
; eat FOR
;
  ldai TOKENIZER_FOR
  jsr exe_accept
;
; get variable id (in accumulator) and hold in r6 lo
;
  jsr tok_variable_num
  mvarl r6
;
; store variable id in for storage hack only lo byte, hi byte 0
;
  stavr r4
  incr r4
  ldai 0
  stavr r4
  incr r4
;
; eat variable id and = then get starting value
;
  ldai TOKENIZER_VARIABLE
  jsr exe_accept
  ldai TOKENIZER_EQ
  jsr exe_accept
  jsr exe_expr
;
; set variable to starting value
;
  mvrla r6
  JSR exe_set_variable
;
; eat TO and get to value
;
  ldai TOKENIZER_TO
  jsr exe_accept
  jsr exe_expr
;
; store to value in for storage area
;
  mvrla r7
  stavr r4
  incr r4
  mvrha r7
  stavr r4
  incr r4
;
; EAT EOL
;
  ldai TOKENIZER_CR
  jsr exe_accept
;
; store instruction after for in for storage area
;
    mvrla r3
    stavr r4
    incr r4
    mvrha r3
    stavr r4
    incr r4
;
;   save for stackptr
;
;    movrr r4,r8
;
    ret
;
; void peek_statment()
;
exe_peek_stmt:
  halt

;
; void poke_statement()
;
exe_poke_stmt:
  halt

;
; void end_statement()
;
exe_end_stmt:
  mviw r6,bas_ended
  LDAI 1
  STAVR r6
  ret
;
; void statment()
;
exe_stmt:
;    MVIW R2,exe_stmt_msg
;    JSR stringout
;    JSR showaddr
    jsr tok_token
;    PUSH
;    JSR showbytea
;    MVIW R2,CRLF
;    JSR STRINGOUT
;    POP


    LDTI TOKENIZER_PRINT
    BRNEQ exe_stmt1
    JSR exe_print_stmt
    ret

exe_stmt1:
    LDTI TOKENIZER_IF
    BRNEQ exe_stmt2
    JSR exe_if_stmt
    ret

exe_stmt2:
    LDTI TOKENIZER_VARIABLE
    BRNEQ exe_stmt3
    JSR exe_let_stmt
    ret

exe_stmt3:
    LDTI TOKENIZER_GOSUB
    BRNEQ exe_stmt4
    JSR exe_gosub_stmt
    ret

exe_stmt4:
    LDTI TOKENIZER_RETURN
    BRNEQ exe_stmt5
    JSR exe_return_stmt
    ret

exe_stmt5:
    LDTI TOKENIZER_FOR
    BRNEQ exe_stmt6
    JSR exe_for_stmt
    ret

exe_stmt6:
    LDTI TOKENIZER_PEEK
    BRNEQ exe_stmt7
    JSR exe_peek_stmt
    ret

exe_stmt7:
    LDTI TOKENIZER_POKE
    BRNEQ exe_stmt8
    JSR exe_poke_stmt
    ret

exe_stmt8:
    LDTI TOKENIZER_NEXT
    BRNEQ exe_stmt9
    JSR exe_next_stmt
    ret

exe_stmt9:
    LDTI TOKENIZER_END
    BRNEQ exe_stmt10
    JSR exe_end_stmt
    ret

exe_stmt10:
    LDTI TOKENIZER_LET
    BRNEQ exe_stmt11
    LDAI TOKENIZER_LET
    JSR exe_accept
    JSR exe_let_stmt
    ret

exe_stmt11:
    LDTI TOKENIZER_GOTO
    BRNEQ exe_stmt12
    JSR exe_goto_stmt
    ret

exe_stmt12:
    MVIW R2,bas_msg3
    jsr stringout
    jsr showaddr
    jsr showbyte
    jsr bas_error

;
; void line_statement (void)
;
exe_line_stmt:
;line_statement(void) {
;    DEBUG_PRINTF("----------- Line number %d ---------\n", tokenizer_num());
;#ifdef unused
;    index_add(tokenizer_num(), tokenizer_pos());
;#endif
;    accept(TOKENIZER_LINENUM);
;    statement();
;    return;
    LDAI TOKENIZER_LINENUM
    jsr exe_accept
    jsr exe_stmt
    ret

;
; void ubasic_run()
;
do_basic:
;    mviw r7,000ah
;    jsr tok_find
;    jsr showr7
;    mviw r2,CRLF
;    jsr stringout

;    mviw r7,0014h
;    jsr tok_find
;    jsr showr7
;    mviw r2,CRLF
;    jsr stringout

    JSR exe_init

;    mviw r7,0080h
;    jsr tok_find
;    jsr showr7
;    mviw r2,CRLF
;    jsr stringout
exe_run:
    jsr exe_finished
    LDTI 1
    BRNEQ exe_run_cont
    ret

exe_run_cont:
    jsr exe_line_stmt
    BR exe_run

;
; int ubasic_finished()
;
exe_finished:
    MVIW R2,bas_ended
    LDAVR R2
    LDTI 1
    BREQ exe_finished_yes
    JSR tok_finished
    LDTI 1
    BREQ exe_finished_yes
    LDAI 0
    RET
exe_finished_yes:
    LDAI 1
    ret

;
; void ubasic_set_variable(int varnum, VARIABLE_TYPE value)
;
; R7 value (only using low byte)
; ACCUMULATOR Variable ref number
;
; Destroys R2 and accumulator, could be fixed with a push/pop
;
exe_set_variable:
    MVIW R2,BASIC_VARS
    MVARL R2
;
    MVRLA R7
    STAVR R2
    RET
;
; VARIABLE_TYPE ubasic_get_variable(int varnum)
;
; ACCUMULATOR HOLDS VARIABLE REF NUMBER, VALUE RETURN IN R7
;
; HACK for now BASIC_VARS needs to be 256 byte 0xAA00 aligned
; and only 0-25 (var names a-z) supported
; for now values are 1 byte, upper byte of R7 forced to 0
;
; Destroys R2 and accumulator, could be fixed with a push/pop
;
exe_get_variable:
    MVIW R2,BASIC_VARS
    MVARL R2
;
    LDAVR R2
    MVARL R7
    LDAI 0
    MVARH R7
    RET


bas_error:
  RET

;
; Tokenizer execute support code
;
tok_token:
  LDAVR R3
  RET

tok_init:
  MVIW r3,basic_test
  RET

tok_next:
  ldavr r3
  ldti TOKENIZER_NUMBER
  BRNEQ tok_next1
  incr r3
  incr r3
  incr r3
  RET

tok_next1:
  ldti TOKENIZER_VARIABLE
  BRNEQ tok_next2
  incr r3
  incr r3
  incr r3
  RET

tok_next2:
  ldti TOKENIZER_LINENUM
  BRNEQ tok_next3
  incr r3
  incr r3
  incr r3
  incr r3
  incr r3
  RET

tok_next3:
  ldti TOKENIZER_STRING
  BRNEQ tok_next4
  incr r3

tok_next3_loop:
  LDAVR R3
  BRZ tok_next3_done
  incr r3
  BR tok_next3_loop

tok_next3_done:
  incr r3
  RET

tok_next4:
  incr r3
  ret

;
; numbers stored low byte followed by high byte in memory

tok_num:
    incr r3
    ldavr r3
    mvarl r7
    incr r3
    ldavr r3
    mvarh r7
    decr r3
    decr r3
    ret

;
; hack only using low byte of id for now
; return in accumulator
;
tok_variable_num:
    incr r3
    ldavr r3
    decr r3
    ret

tok_string:
    movrr r3,r7
    incr r7
    ret

tok_finished:
    ldavr r3
    ldti 1
    brneq tok_finished1
    ldai 1
    ret
tok_finished1:
    ldai 0
    ret

;
; find linenum in r7
;
tok_find:
;    jsr showr7
    pushr r5
    MVIW r5,basic_test

tok_find_loop:
    ldavr r5
    ldti 01
    brneq tok_find_loop1
    mviw r7,0
    mvrla r7
    popr r5

    ret
tok_find_loop1:
    incr r5
    mvrla r7
    MVAT
    ldavr r5
    brneq tok_find1
    incr r5
    mvrha r7
    MVAT
    ldavr r5
    brneq tok_find2
    decr r5
    decr r5
    movrr r5,r7
    ldai 1
    popr r5
    ret

tok_find1:
    incr r5
tok_find2:
    incr r5
    ldavr r5
    mviw r6,0
    mvarl r6
    decr r6
    decr r6
    decr r6
tok_find_moveptr:
    incr r5
    decr r6
    mvrla r6
    brnz tok_find_moveptr
    br tok_find_loop

tok_goto:
    movrr r7,r3
    ret

;
; list out token buffer
; buffer address in r7
;
tokl_let: DB "LET ",0
tokl_print: DB "PRINT ",0
tokl_if: DB "IF ",0
tokl_then: DB "THEN ",0
tokl_else: DB "ELSE ",0
tokl_for: DB "FOR ",0
tokl_to: DB "TO ",0
tokl_next: DB "NEXT ",0
tokl_goto: DB "GOTO ",0
tokl_gosub: DB "GOSUB ",0
tokl_return: DB "RETURN ",0
tokl_rem: DB "REM ",0
tokl_peek: DB "PEEK ",0
tokl_poke: DB "POKE ",0
tokl_end: DB "END ",0
tokl_call: DB "CALL ",0
tokl_error: DB "LIST ERROR",0


tok_list:
    pushr r3
    movrr r7,r3


tok_list_loop:
    ldavr r3

    LDTI TOKENIZER_ERROR
    BRNEQ tok_list1
    MVIW R2,tokl_error
    JSR stringout
    JSR showaddr
    BR tok_list_done
    BR tok_list_loop

tok_list1:
    LDTI TOKENIZER_EOF
    BRNEQ tok_list2
    BR tok_list_done
    BR tok_list_loop

tok_list2:
    LDTI TOKENIZER_NUMBER
    BRNEQ tok_list3
    incr r3
    ldavr r3
    mvarl r7
    incr r3
    ldavr r3
    mvarh r7
    INCR R3
    jsr showr7
    ldai ' '
    jsr uartout
    BR tok_list_loop

tok_list3:
    LDTI TOKENIZER_STRING
    BRNEQ tok_list4
    incr r3
    movrr r3,r2
    jsr stringout
    ldai ' '
    jsr uartout
tok_list_string:
    ldavr r3
    brz tok_list_stringend
    incr r3
    br tok_list_string
tok_list_stringend:
    incr r3
    BR tok_list_loop

tok_list4:
    LDTI TOKENIZER_VARIABLE
    BRNEQ tok_list5
    incr r3
    ldavr r3
    ldti 'A'
    ADDT
    incr r3
    incr r3
    jsr uartout

;    ldavr r3
;    mvarl r7
;    incr r3
;    ldavr r3
;    mvarh r7
;    INCR R3
;    jsr showr7

    ldai ' '
    jsr uartout
    BR tok_list_loop

tok_list5:
    LDTI TOKENIZER_LET
    BRNEQ tok_list6
    MVIW R2,tokl_let
    JSR stringout
    INCR R3
    BR tok_list_loop

tok_list6:
    LDTI TOKENIZER_PRINT
    BRNEQ tok_list7
    MVIW R2,tokl_print
    jsr STRINGOUT
    INCR R3
    BR tok_list_loop

tok_list7:
    LDTI TOKENIZER_IF
    BRNEQ tok_list8
    MVIW R2,tokl_if
    JSR stringout
    INCR R3
    BR tok_list_loop

tok_list8:
    LDTI TOKENIZER_THEN
    BRNEQ tok_list9
    MVIW R2,tokl_then
    JSR stringout
    INCR R3
    BR tok_list_loop

tok_list9:
    LDTI TOKENIZER_ELSE
    BRNEQ tok_list10
    MVIW R2,tokl_else
    JSR stringout
    INCR R3
    BR tok_list_loop

tok_list10:
    LDTI TOKENIZER_FOR
    BRNEQ tok_list11
    MVIW R2,tokl_for
    JSR stringout
    INCR R3
    BR tok_list_loop

tok_list11:
    LDTI TOKENIZER_TO
    BRNEQ tok_list12
    MVIW R2,tokl_to
    JSR stringout
    INCR R3
    BR tok_list_loop

tok_list12:
    LDTI TOKENIZER_NEXT
    BRNEQ tok_list13
    MVIW R2,tokl_next
    JSR stringout
    INCR R3
    BR tok_list_loop

tok_list13:
    LDTI TOKENIZER_GOTO
    BRNEQ tok_list14
    MVIW R2,tokl_goto
    JSR stringout
    INCR R3
    BR tok_list_loop

tok_list14:
    LDTI TOKENIZER_GOSUB
    BRNEQ tok_list15
    MVIW R2,tokl_gosub
    JSR stringout
    INCR R3
    BR tok_list_loop

tok_list15:
    LDTI TOKENIZER_RETURN
    BRNEQ tok_list16
    MVIW R2,tokl_return
    JSR stringout
    INCR R3
    BR tok_list_loop

tok_list16:
    LDTI TOKENIZER_CALL
    BRNEQ tok_list17
    MVIW R2,tokl_call
    JSR stringout
    INCR R3
    BR tok_list_loop

tok_list17:
    LDTI TOKENIZER_REM
    BRNEQ tok_list18
    MVIW R2,tokl_rem
    JSR stringout
    INCR R3
    BR tok_list_loop

tok_list18:
    LDTI TOKENIZER_PEEK
    BRNEQ tok_list19
    MVIW R2,tokl_peek
    JSR stringout
    INCR R3
    BR tok_list_loop

tok_list19:
    LDTI TOKENIZER_POKE
    BRNEQ tok_list20
    MVIW R2,tokl_poke
    JSR stringout
    INCR R3
    BR tok_list_loop

tok_list20:
    LDTI TOKENIZER_END
    BRNEQ tok_list21
    MVIW R2,tokl_end
    JSR stringout
    INCR R3
    BR tok_list_loop

tok_list21:
    LDTI TOKENIZER_COMMA
    BRNEQ tok_list22
    ldai ','
    jsr uartout
    ldai ' '
    jsr uartout
    INCR R3
    BR tok_list_loop

tok_list22:
    LDTI TOKENIZER_SEMICOLON
    BRNEQ tok_list23
    ldai ';'
    jsr uartout
    ldai ' '
    jsr uartout
    INCR R3
    BR tok_list_loop

tok_list23:
    LDTI TOKENIZER_PLUS
    BRNEQ tok_list24
    ldai '+'
    jsr uartout
    ldai ' '
    jsr uartout
    INCR R3
    BR tok_list_loop

tok_list24:
    LDTI TOKENIZER_MINUS
    BRNEQ tok_list25
    ldai '-'
    jsr uartout
    ldai ' '
    jsr uartout
    INCR R3
    BR tok_list_loop

tok_list25:
    LDTI TOKENIZER_AND
    BRNEQ tok_list26
    ldai '&'
    jsr uartout
    ldai ' '
    jsr uartout
    INCR R3
    BR tok_list_loop

tok_list26:
    LDTI TOKENIZER_OR
    BRNEQ tok_list27
    ldai '|'
    jsr uartout
    ldai ' '
    jsr uartout
    INCR R3
    BR tok_list_loop

tok_list27:
    LDTI TOKENIZER_ASTR
    BRNEQ tok_list28
    ldai '*'
    jsr uartout
    ldai ' '
    jsr uartout
    INCR R3
    BR tok_list_loop

tok_list28:
    LDTI TOKENIZER_SLASH
    BRNEQ tok_list29
    ldai '/'
    jsr uartout
    ldai ' '
    jsr uartout
    INCR R3
    BR tok_list_loop

tok_list29:
    LDTI TOKENIZER_MOD
    BRNEQ tok_list30
    ldai '%'
    jsr uartout
    ldai ' '
    jsr uartout
    INCR R3
    BR tok_list_loop

tok_list30:
    LDTI TOKENIZER_HASH
    BRNEQ tok_list31
    ldai '#'
    jsr uartout
    ldai ' '
    jsr uartout
    INCR R3
    BR tok_list_loop

tok_list31:
    LDTI TOKENIZER_LEFTP
    BRNEQ tok_list32
    ldai '()'
    jsr uartout
    ldai ' '
    jsr uartout
    INCR R3
    BR tok_list_loop

tok_list32:
    LDTI TOKENIZER_RIGHTP
    BRNEQ tok_list33
    ldai ')'
    jsr uartout
    ldai ' '
    jsr uartout
    INCR R3
    BR tok_list_loop

tok_list33:
    LDTI TOKENIZER_LT
    BRNEQ tok_list34
    ldai '<'
    jsr uartout
    ldai ' '
    jsr uartout
    INCR R3
    BR tok_list_loop

tok_list34:
    LDTI TOKENIZER_GT
    BRNEQ tok_list35
    ldai '>'
    jsr uartout
    ldai ' '
    jsr uartout
    INCR R3
    BR tok_list_loop

tok_list35:
    LDTI TOKENIZER_EQ
    BRNEQ tok_list36
    ldai '='
    jsr uartout
    ldai ' '
    jsr uartout
    INCR R3
    BR tok_list_loop

tok_list36:
    LDTI TOKENIZER_CR
    BRNEQ tok_list37
    mviw r2,CRLF
    jsr stringout
    INCR R3
    BR tok_list_loop

tok_list37:
    LDTI TOKENIZER_LINENUM
    BRNEQ tok_list38
    incr r3
    ldavr r3
    mvarl r7
    incr r3
    ldavr r3
    mvarh r7
    INCR R3
    incr r3
    incr r3
    jsr showr7
    ldai ' '
    jsr uartout
    BR tok_list_loop

tok_list38:
    MVIW R2,tokl_error
    JSR stringout
    JSR showaddr
    BR tok_list_done
;
; any cleanup
;
tok_list_done:
    popr r3
    ret

;
;
; Basic InterpreterParser
; R3   =  UTILITY PTR
; R4.L =  INPUT TEXT LINE PTR
; R4.H =  INPUT TEXT LINE NEXTPTR
; R5.L =  TOKEN BUFFER PTR
; R5.H =  CURRENT TOKEN
;
parse_keywords:
      DB "let",0,TOKENIZER_LET
      DB "print",0,TOKENIZER_PRINT
      DB "if",0,TOKENIZER_IF
      DB "then",0,TOKENIZER_THEN
      DB "else",0,TOKENIZER_ELSE
      DB "for",0,TOKENIZER_FOR
      DB "to",0,TOKENIZER_TO
      DB "next",0,TOKENIZER_NEXT
      DB "goto",0,TOKENIZER_GOTO
      DB "gosub",0,TOKENIZER_GOSUB
      DB "return",0,TOKENIZER_RETURN
      DB "call",0,TOKENIZER_CALL
      DB "rem",0,TOKENIZER_REM
      DB "peek",0,TOKENIZER_PEEK
      DB "poke",0,TOKENIZER_POKE
      DB "end",0,TOKENIZER_END
      DB 0,0,TOKENIZER_ERROR

;
; int singlechar (void)
;
; return TOKEN result in accumulator
;
; ready for testing
;
parse_singlechar:
;
    MVIW r3,parse_input_line
    mvrla r4
    mvarl r3
;
    ldti 0ah
    brneq parsechar1
    ldai TOKENIZER_CR
    ret
parsechar1:
    ldti ','
    brneq parsechar2
    ldai TOKENIZER_COMMA
    ret
parsechar2:
    ldti ';'
    brneq parsechar3
    ldai TOKENIZER_SEMICOLON
    ret
parsechar3:
    ldti '+'
    brneq parsechar4
    ldai TOKENIZER_PLUS
    ret
parsechar4:
    ldti '-'
    brneq parsechar5
    ldai TOKENIZER_MINUS
    ret
parsechar5:
    ldti '&'
    brneq parsechar6
    ldai TOKENIZER_AND
    ret
parsechar6:
    ldti '|'
    brneq parsechar7
    ldai TOKENIZER_OR
    ret
parsechar7:
    ldti '*'
    brneq parsechar8
    ldai TOKENIZER_ASTR
    ret
parsechar8:
    ldti '%'
    brneq parsechar9
    ldai TOKENIZER_MOD
    ret
parsechar9:
    ldti '()'
    brneq parsechar10
    ldai TOKENIZER_LEFTP
    ret
parsechar10:
    ldti '#'
    brneq parsechar11
    ldai TOKENIZER_HASH
    ret
parsechar11:
    ldti ')'
    brneq parsechar12
    ldai TOKENIZER_RIGHTP
    ret
parsechar12:
    ldti '<'
    brneq parsechar13
    ldai TOKENIZER_LT
    ret
parsechar13:
    ldti '>'
    brneq parsechar14
    ldai TOKENIZER_GT
    ret
parsechar14:
    ldti '='
    brneq parsechar15
    ldai TOKENIZER_EQ
    ret
parsechar15:
    ldai 0
    ret

;
; int get_next_token(void)
;
; under development fix ptr nextptr

parse_get_next_tok:
    pushr r6
    MVIW r3,parse_input_line
    mvrla r4
    mvarl r3
;
    ldavr R3
    brnz parse_gnt1
    ldai TOKENIZER_EOF
    popr r6
    ret

parse_gnt1:
;
; is digit
;
; chcek for number
    ldavr R3
    jsr parse_isdigit
    brz parse_gnt2
parse_gnt1loop:
    incr R3
    jsr parse_isdigit
    brnz parse_gnt1loop
    mvrla R3
    mvarh R4
    ldai TOKENIZER_NUMBER
    popr r6
    ret
;
parse_gnt2:
;
; singlechar
;
   ldavr R3
   jsr parse_singlechar
   BRZ parse_gnt3
   push
   incr r3
   mvrla R3
   mvarh R4
   pop
   popr r6
   ret
;
parse_gnt3:
;
; quote
;
  ldavr R3
  ldti '"'
  brneq parse_gnt4
parse_gnt3loop:
  incr r3
  ldavr R3
  ldti '"'
  brneq parse_gnt3loop
  incr r3
  mvrla R3
  mvarh R4
  ldai TOKENIZER_STRING
  popr r6
  ret
;
parse_gnt4:
;
; keyword search
;
  pushr r5
  mviw r5,parse_keywords
top:
  ldavr r5
  brz nokeyowrdsfound
  movrr r3,r6
pcmploop:
  ldavr r5
  brz found
  MVAT
  ldavr r6
  brneq skiptoend
  incr r5
  incr r6
  br pcmploop

skiptoend:
;  skip to end of string and skip over token
skiploop:
    ldavr r5
    incr r5
    brnz skiploop
    incr r5
    br top

found:
    mvrla r6
    mvarh r4
    incr r5
    ldavr r5
    popr r5
    popr r6
    ret

nokeyowrdsfound:
    popr r6
    popr r5
;
;  check for variables
;
    ldavr r3
    ldti 'A'
    BRLT parse_gnt_error
    ldti 'Z'
    BRGT parse_gnt_error
    INCR r3
    mvrla R3
    mvarl R4
    LDAI tokenizer_variable
    POPR R6
    RET
parse_gnt_error:
    ldai tokenizer_error
    POPR R6
    ret

;
; void TOKENIZER_GOTO (char * program)
;
; under development
;
parse_goto:
    movrr r7,r3
    jsr parse_get_next_tok
    mvarl r6
    ret

;
; void tokenizer_init(int ptr)
;
; changed to set ptr to 0, assumes input line buffer is 256 byte aligned
; so set ptrs to 0
; ptr into line buffer R4.L
; ptr int token buffer R5.L
; token counter R5.H
;
; under development
;
parse_init:
    ldai 0
    mvarl R4
    mvarh R5
    mvarl R5
    jsr parse_get_next_tok
    ret

;
; int tokenizer_token(void)
:
parse_token:
    mvrla r6
    ret

;
; void tokenizer_next(void)
;
parse_next:

;
; VARIABLE_TYPE tokenizer_num(void)
;
; Hack for now input characters are ascii hex format HHHH
;
; value returned in R7
;
; Should this advance the line ptr?
;
parse_num:
    JSR parse_getnibble
    SHL
    SHL
    SHL
    SHL
    ANDI 0f0h
    Push
    JSR parse_getnibble
    ANDI 0FH
    MVAT
    Pop
    ORT
    MVARH R7

    JSR parse_getnibble
    SHL
    shl
    shl
    shl
    ANDI 0f0h
    push
    JSR parse_getnibble
    ANDI 0FH
    MVAT
    pop
    ORT
    MVARL R7
    RET

;
; add error checking
;
; return hex nibble in accumulator
;
parse_getnibble:
      MVIW r3,parse_input_line
      mvrla r4
      mvarl r3
;
      LDAVR R3
;
; Risk if input line is greater then 255 chars, maybe test at input
;
      incr r4

      LDTI '9'
      BRGT parse_af
      SUBI '0'
      RET
parse_af:
      JSR toupper
      SUBI 'A'
      ADDI 10
      RET
;
; void tokenizer_string(char *dest, int len)
;
parse_string:
    JSR parse_token
    LDTI TOKENIZER_STRING
    BREQ parse_string1
    ret

parse_string1:
    MVIW r3,parse_input_line
    mvrla r4
    mvarl r3
    ;
    LDAVR R3


;
; void tokenizer_error_print(void)
;
parse_error_print:

;
; int tokenizer_finished(void)
;
parse_finished:

;
; int tokenizer_variable_num(void)
;
parse_variable_num:

;
; char *const tokenizer_pos(void)
;
parse_pos:

;not used old
; char *tokenize(char *program)
;
; parse:

;
; char *tokenizeLine(char *line)
;
parse_line:
    MVIW R3,parse_token_buffer
    LDAI 0
    mvarl R3
    mvarl R4
    MVARL R5
    LDAI TOKENIZER_LINENUM
    STAVR R3
    INCR R3

    JSR parse_num ; testexamine

    ;
    LDAVR R3

JSR parse_token
LDTI TOKENIZER_STRING
BREQ parse_string1
ret


;
; void addLine(char *buff)
;
parse_addline:

;
; void removeLine(int lineNum)
;
parse_removeline:

;
; parse utilites
;

;
; is digit
; returns 1 if yes and 0 if no
;
; hack for now include HEX
;
; destroys tmp register
parse_isdigit:
   ldti '0'
   brlt parse_isdigit_no
   ldti '9'
   brgt parse_isdigit_af
   br parse_isdigit_yes

parse_isdigit_af:
    ldti 'A'
    brlt parse_isdigit_no
    ldti 'F'
    brgt parse_isdigit_no

parse_isdigit_yes:
    ldai 1
    ret

parse_isdigit_no:
    ldai 0
    ret

basic_test:
    DB  25h,0ah,00h,0eh,00h,06h,03h,68h,65h,6ch,6ch,6fh,00h,24h,25h,14h
    DB  00h,0dh,00h,04h,02h,00h,23h,02h,09h,00h,24h,25h,1eh,00h,0ah,00h
    DB  06h,04h,02h,00h,24h,25h,28h,00h,0dh,00h,04h,04h,00h,23h,02h,32h
    DB  00h,24h,25h,32h,00h,17h,00h,06h,03h,68h,32h,00h,15h,04h,02h,00h
    DB  15h,04h,04h,00h,15h,02h,16h,00h,24h,25h,3ch,00h,12h,00h,0ah,04h
    DB  03h,00h,23h,02h,01h,00h,0bh,02h,05h,00h,24h,25h,46h,00h,0ah,00h
    DB  06h,04h,03h,00h,24h,25h,50h,00h,0ah,00h,0ch,04h,03h,00h,24h,25h
    DB  51h,00h,12h,00h,06h,03h,6eh,65h,78h,74h,20h,64h,6fh,6eh,65h,00h
    DB  24h,25h,52h,00h,0ah,00h,0eh,02h,6eh,00h,24h,25h,55h,00h,0ah,00h
    DB  0dh,02h,7dh,00h,24h,25h,5ah,00h,12h,00h,06h,03h,6eh,65h,78h,74h
    DB  20h,64h,6fh,6eh,65h,00h,24h,25h,6eh,00h,11h,00h,06h,03h,69h,6eh
    DB  20h,67h,6fh,73h,75h,62h,00h,24h,25h,70h,00h,11h,00h,06h,03h,69h
    DB  6eh,20h,73h,75h,62h,20h,32h,00h,24h,25h,72h,00h,07h,00h,0fh,24h
    DB  25h,7dh,00h,0ch,00h,06h,03h,65h,6eh,64h,00h,24h,25h,7eh,00h,07h
    DB  00h,14h,24h,01h,00h,00h,00h,00h,00h,00h,00h,00h,00h,00h,00h,00h

;
; The End
;
ZZZZ:
  DB   0
